cdelor02/mres-thesis/computer_vision/copper_wire_actuator_35fast_chamber_100g_weight_lift-2021-09-06.jpg_502.jpg

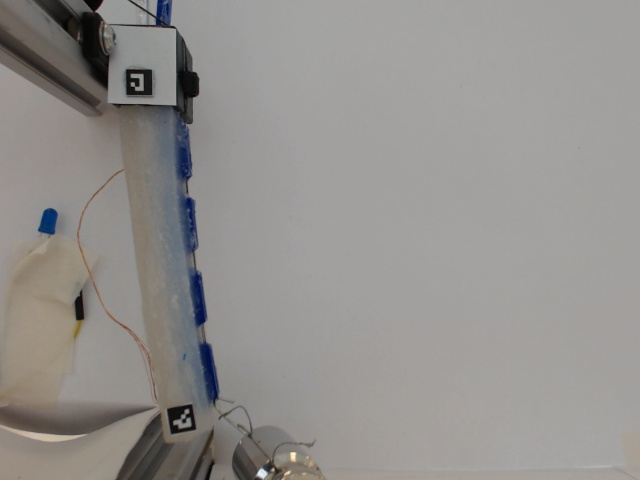
computer_vision/copper_wire_actuator_35fast_chamber_100g_weight_lift-2021-09-06.jpg_502.jpg
