cdelor02/mres-thesis/computer_vision/figure_images.png_1524.jpg

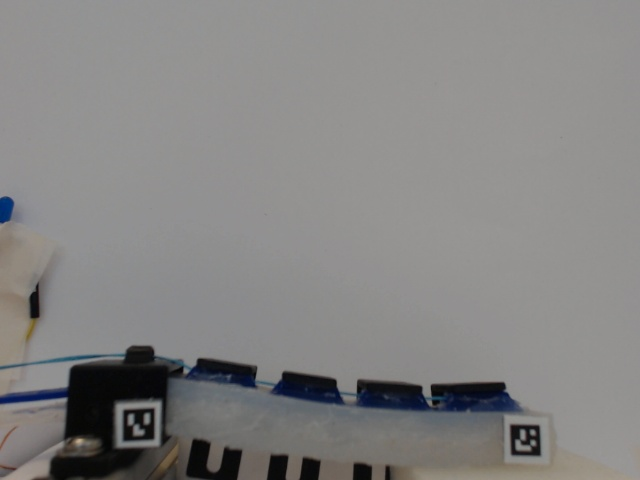
computer_vision/figure_images.png_1524.jpg
