cdelor02/mres-thesis/computer_vision/firstframe.jpg

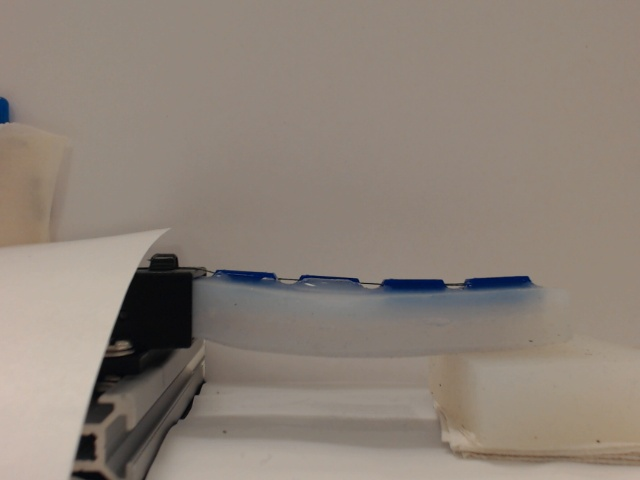
computer_vision/firstframe.jpg
