cdelor02/mres-thesis/computer_vision/firstframe_edited.jpg

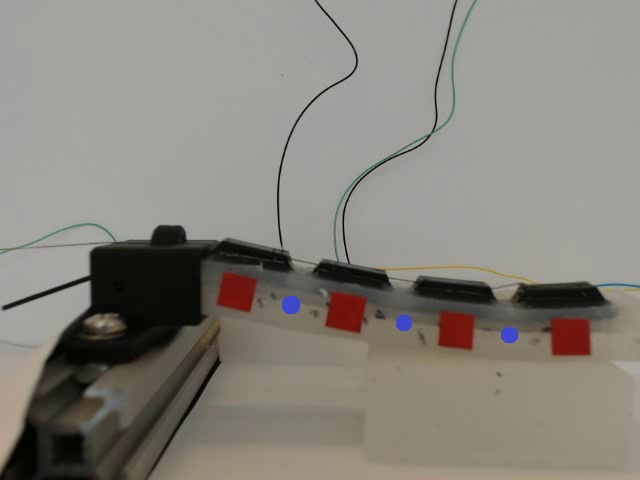
computer_vision/firstframe_edited.jpg
