cdelor02/mres-thesis/computer_vision/hihihi2021-09-06.jpg_659.jpg

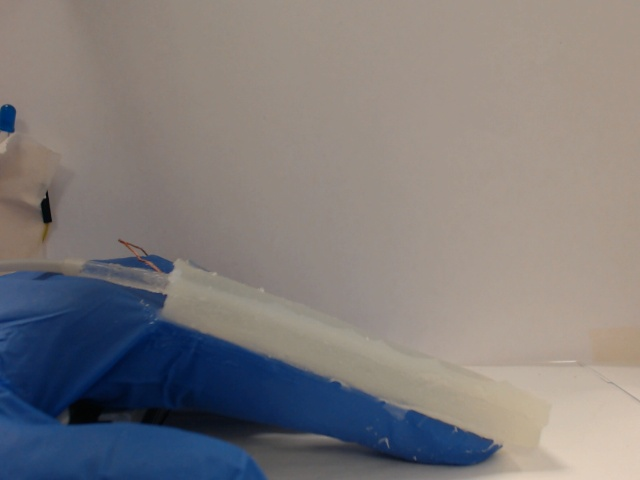
computer_vision/hihihi2021-09-06.jpg_659.jpg
