cdelor02/mres-thesis/computer_vision/imcap_187.jpg

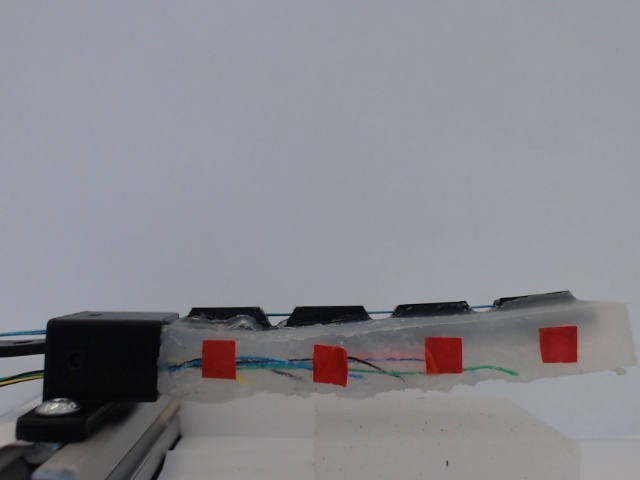
computer_vision/imcap_187.jpg
