cdelor02/mres-thesis/computer_vision/opencv_images/firstframe.jpg

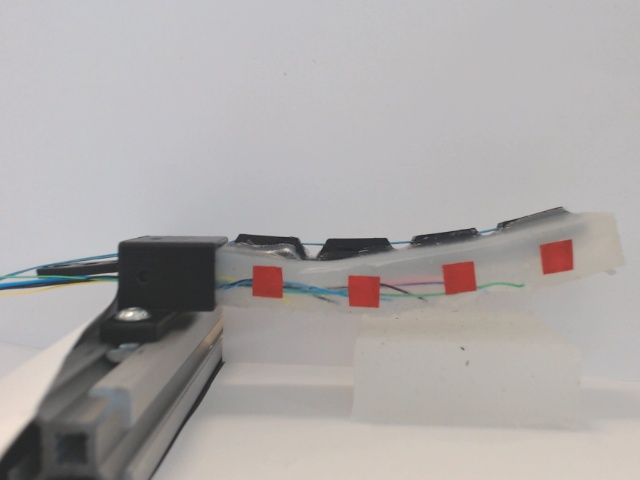
computer_vision/opencv_images/firstframe.jpg
