cdelor02/mres-thesis/computer_vision/opencv_images/myframe_348.jpg

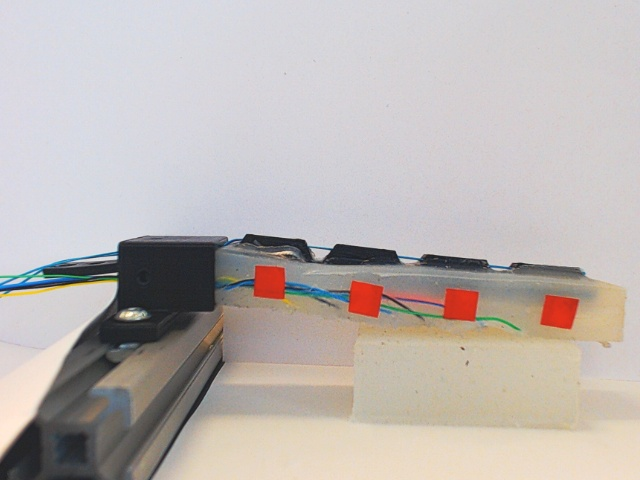
computer_vision/opencv_images/myframe_348.jpg
