cdelor02/mres-thesis/computer_vision/opencv_images/myframe_360.jpg

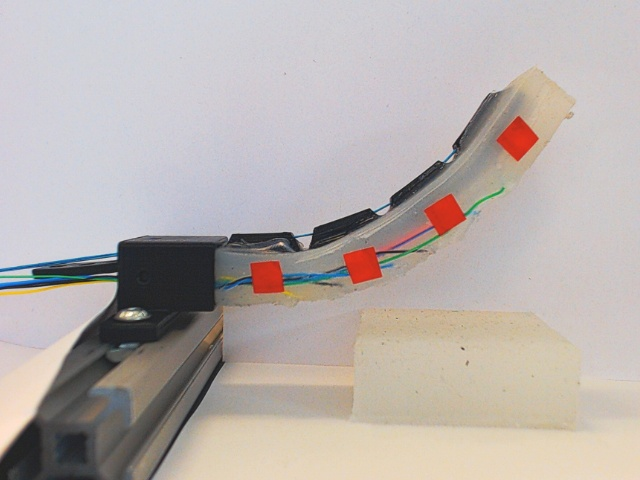
computer_vision/opencv_images/myframe_360.jpg
