cdelor02/mres-thesis/computer_vision/opencv_images/myframe_1371.jpg

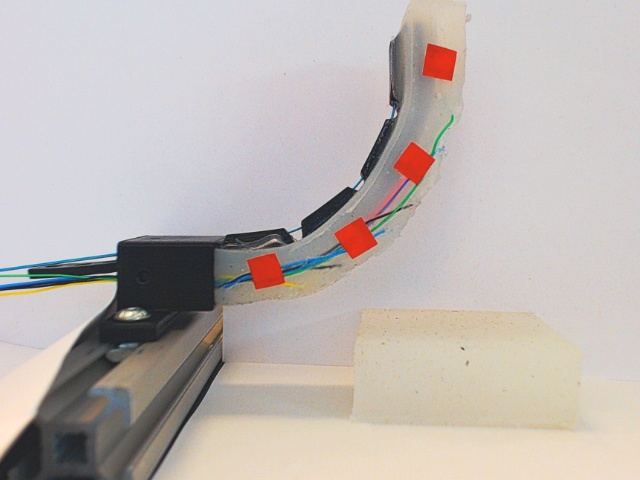
computer_vision/opencv_images/myframe_1371.jpg
