cdelor02/mres-thesis/computer_vision/opencv_images/myframe_1525.jpg

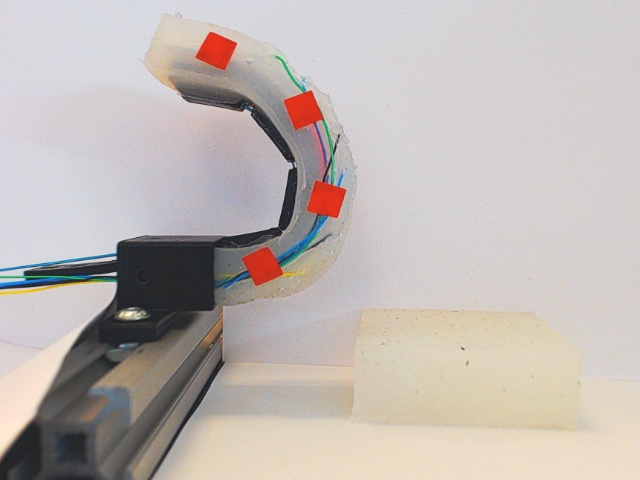
computer_vision/opencv_images/myframe_1525.jpg
