cdelor02/mres-thesis/computer_vision/opencv_images/tracked_points_paths.png

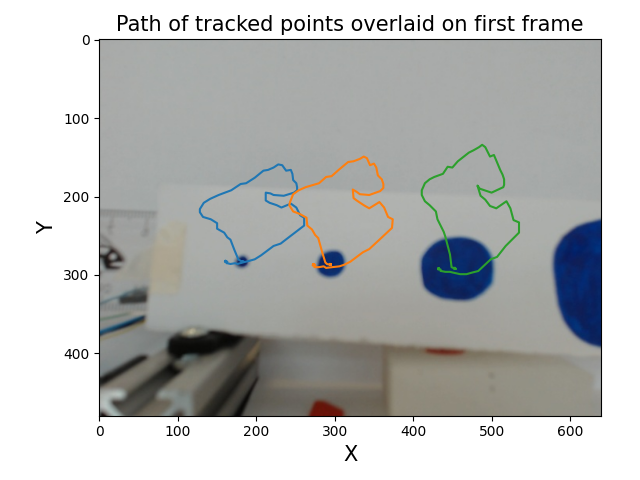
computer_vision/opencv_images/tracked_points_paths.png
