cdelor02/mres-thesis/computer_vision/opencv_images/tracked_points_simple_arcs.png

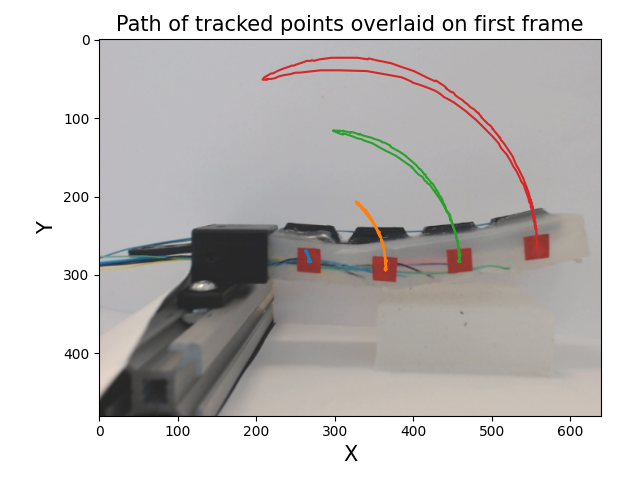
computer_vision/opencv_images/tracked_points_simple_arcs.png
