cdelor02/mres-thesis/computer_vision/red.png

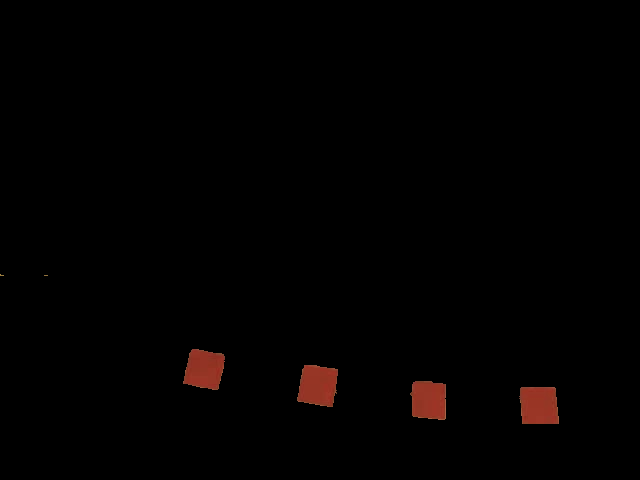
computer_vision/red.png
