cdelor02/mres-thesis/FPC_design/whole_system_block_diagram_v1.png

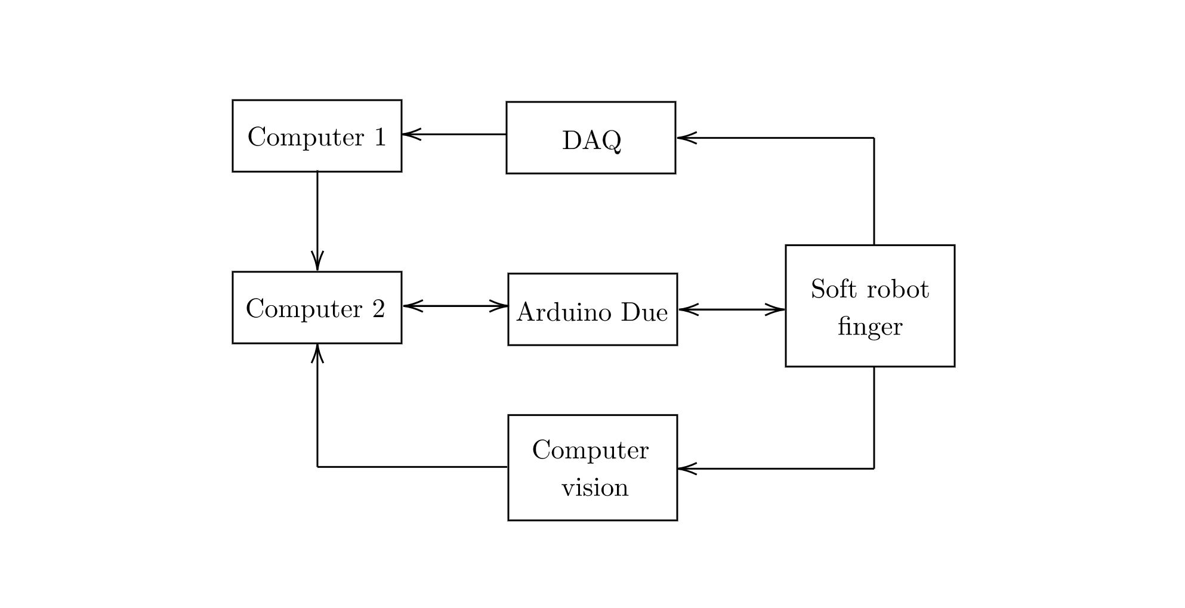
FPC_design/whole_system_block_diagram_v1.png
