cdelor02/mres-thesis/images/1_in_two_stages_duetimer_bettertest_data.png

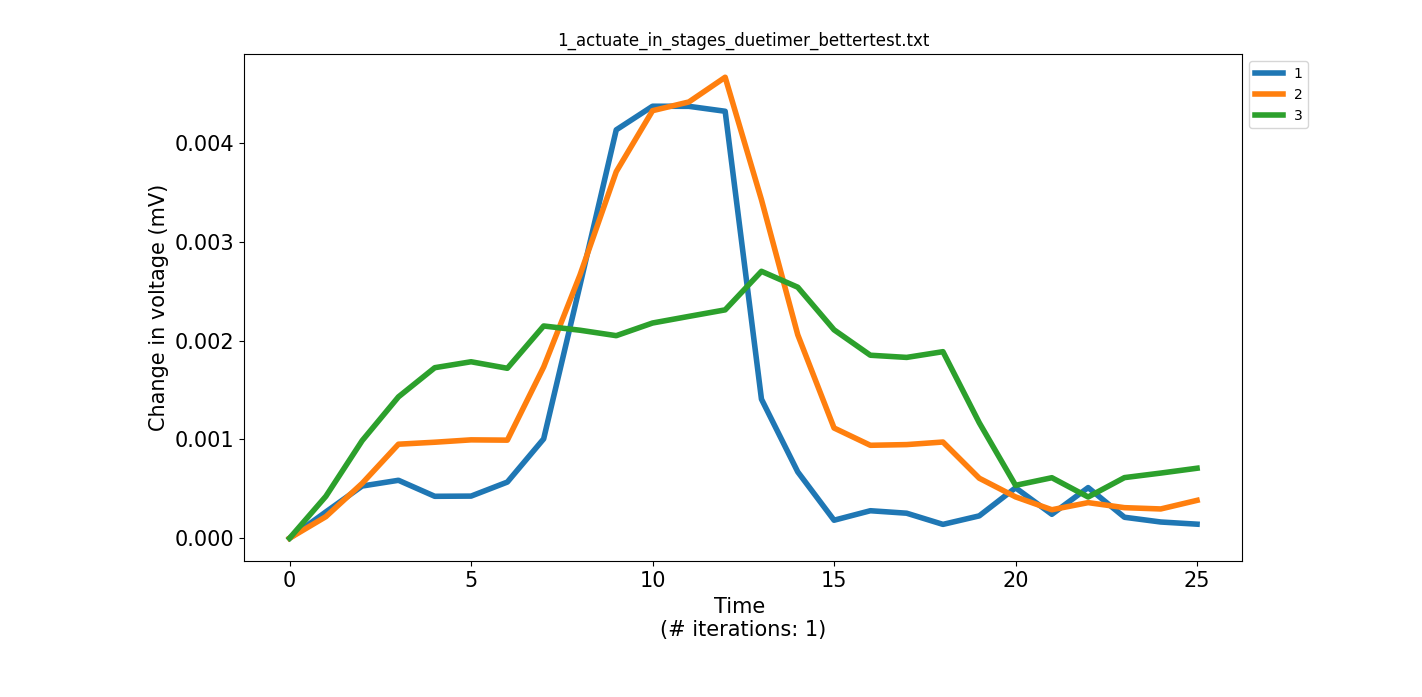
images/1_in_two_stages_duetimer_bettertest_data.png
