cdelor02/mres-thesis/images/5__duetimer_bettertest_data.png

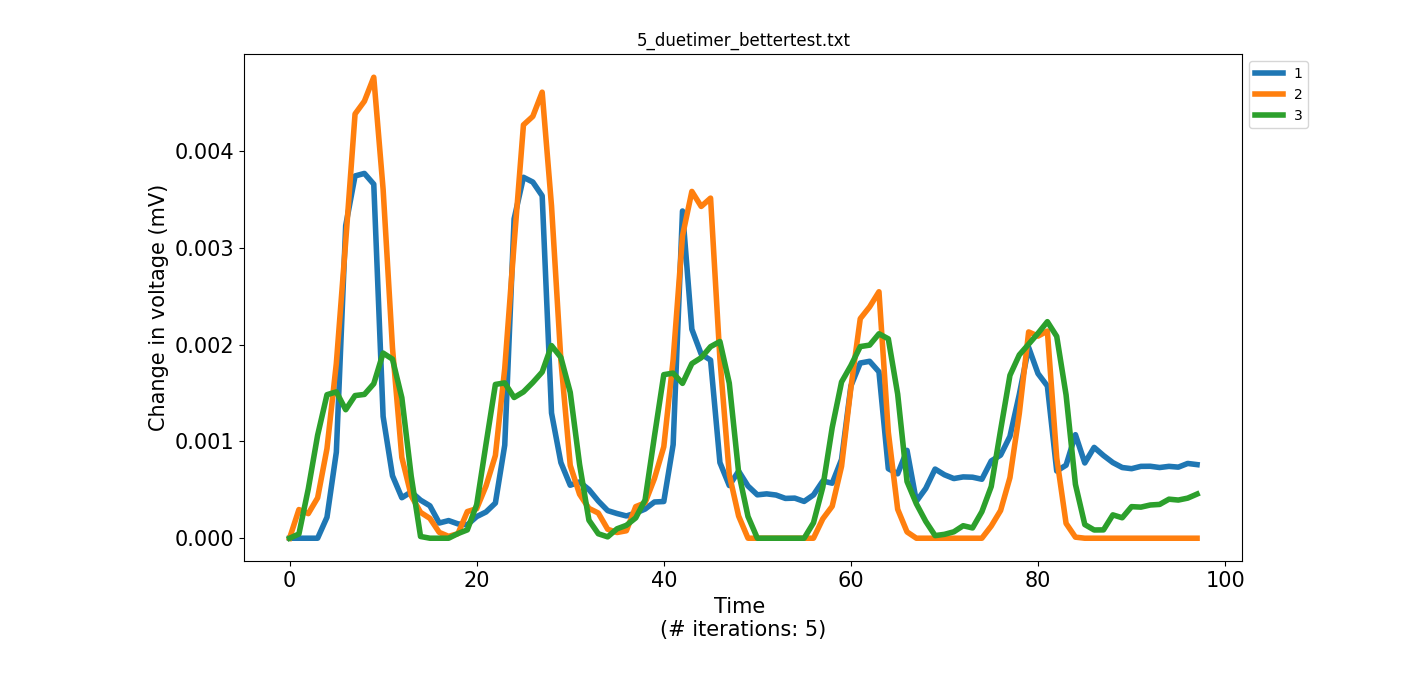
images/5__duetimer_bettertest_data.png
