cdelor02/mres-thesis/images/5_in_two_stages_duetimer_bettertest_data.png

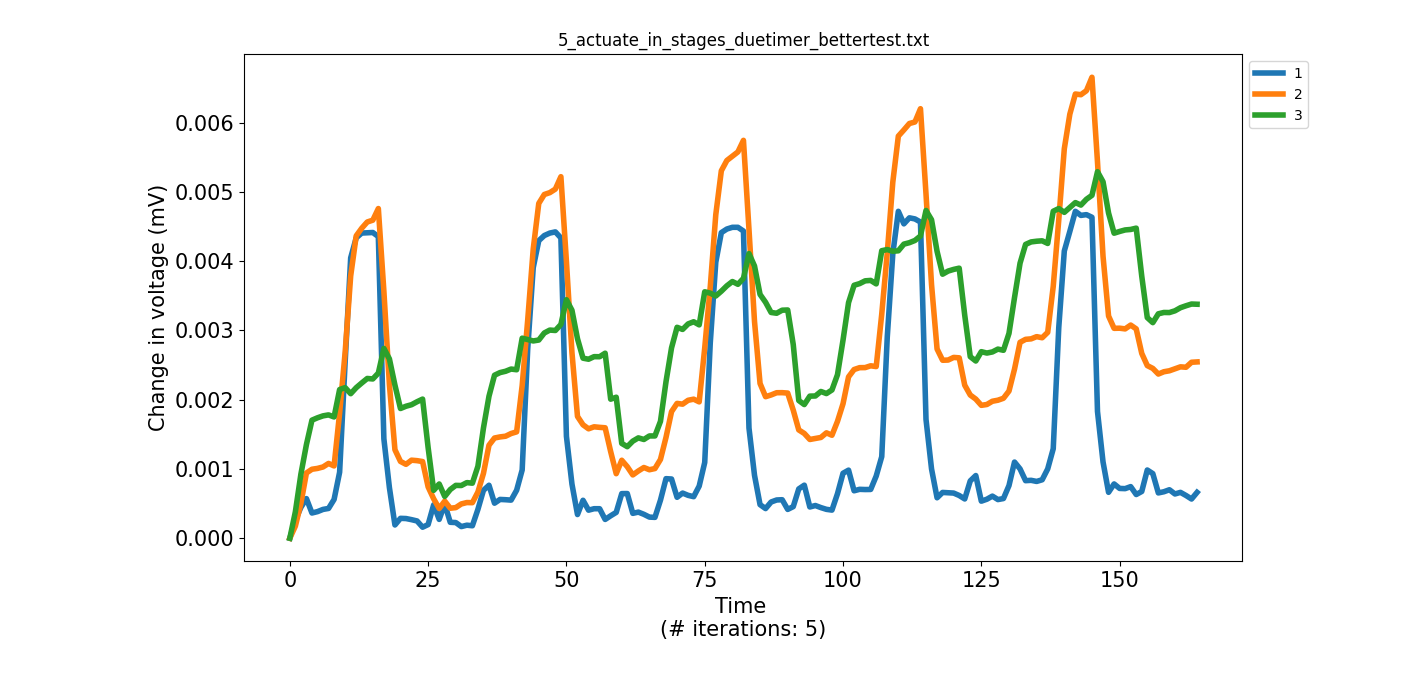
images/5_in_two_stages_duetimer_bettertest_data.png
