cdelor02/mres-thesis/images/10-iteration_episodes_eit_plots/ep2.png

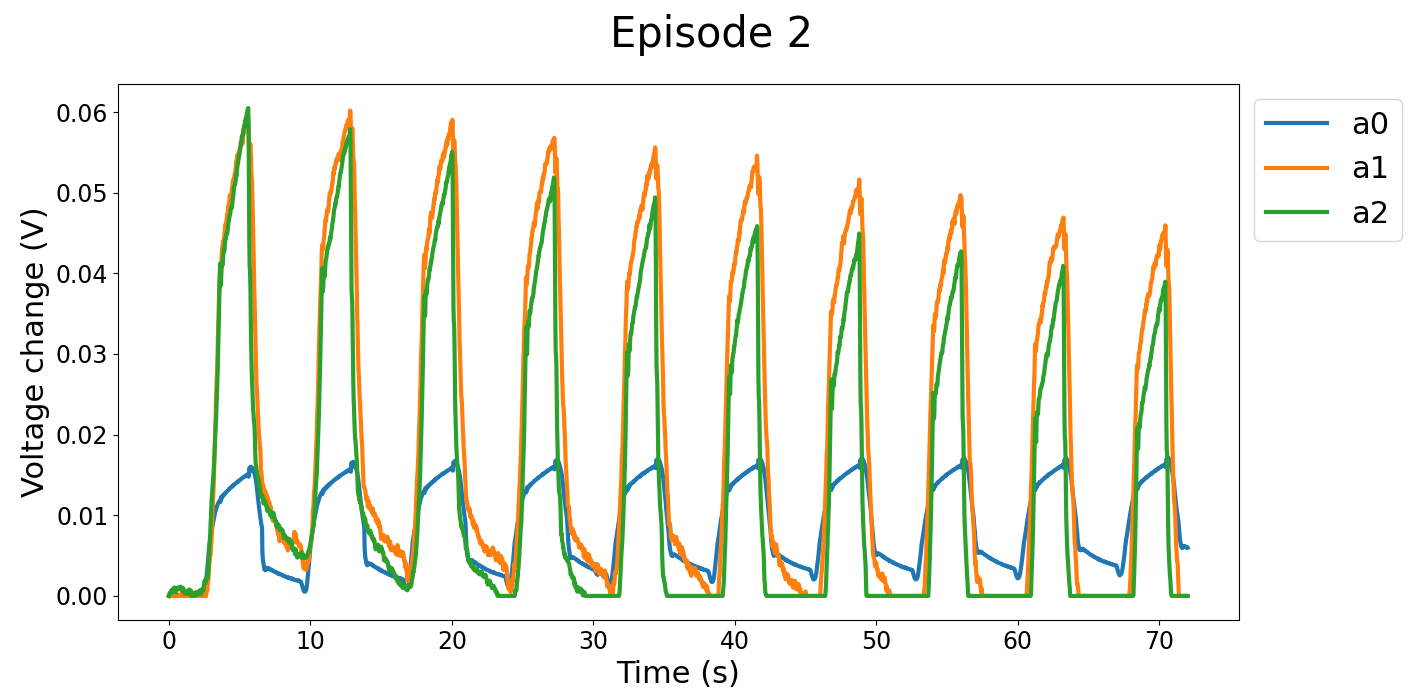
images/10-iteration_episodes_eit_plots/ep2.png
