cdelor02/mres-thesis/images/10-iteration_episodes_eit_plots/ep9.png

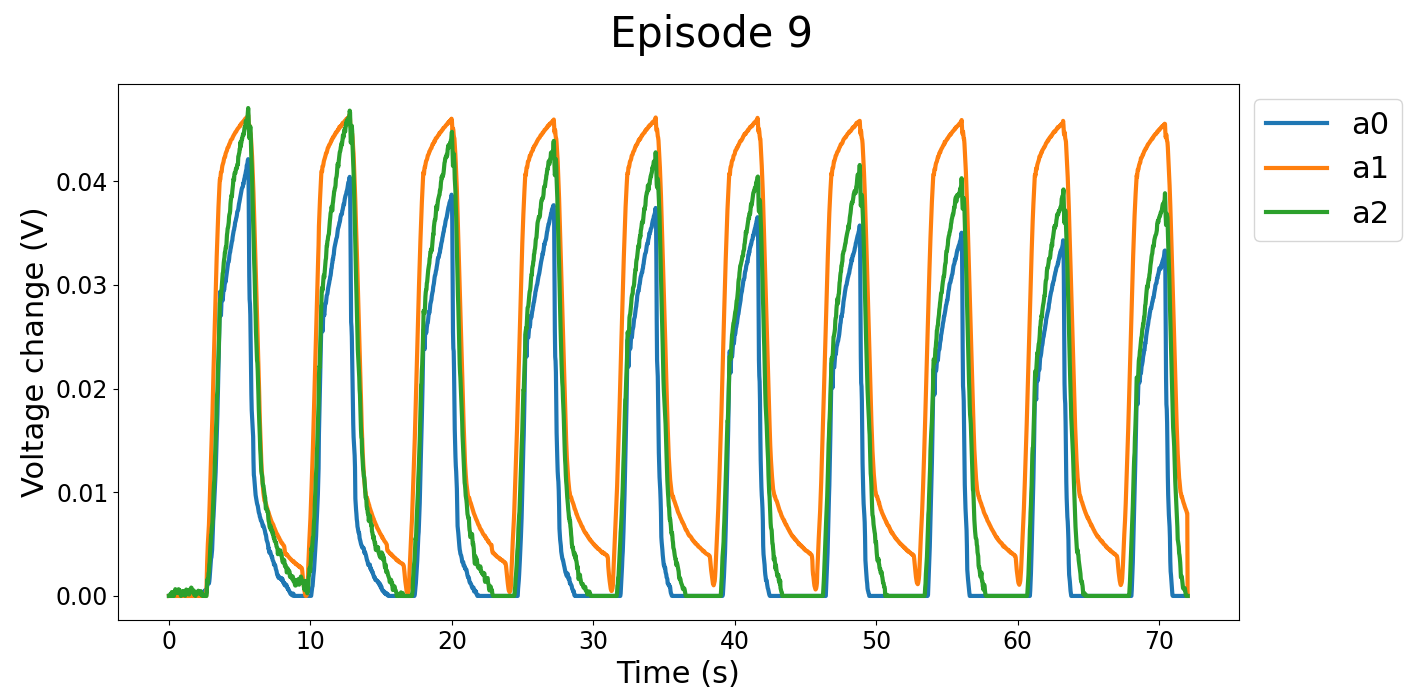
images/10-iteration_episodes_eit_plots/ep9.png
