cdelor02/mres-thesis/images/10_duetimer_bettertest_data.png

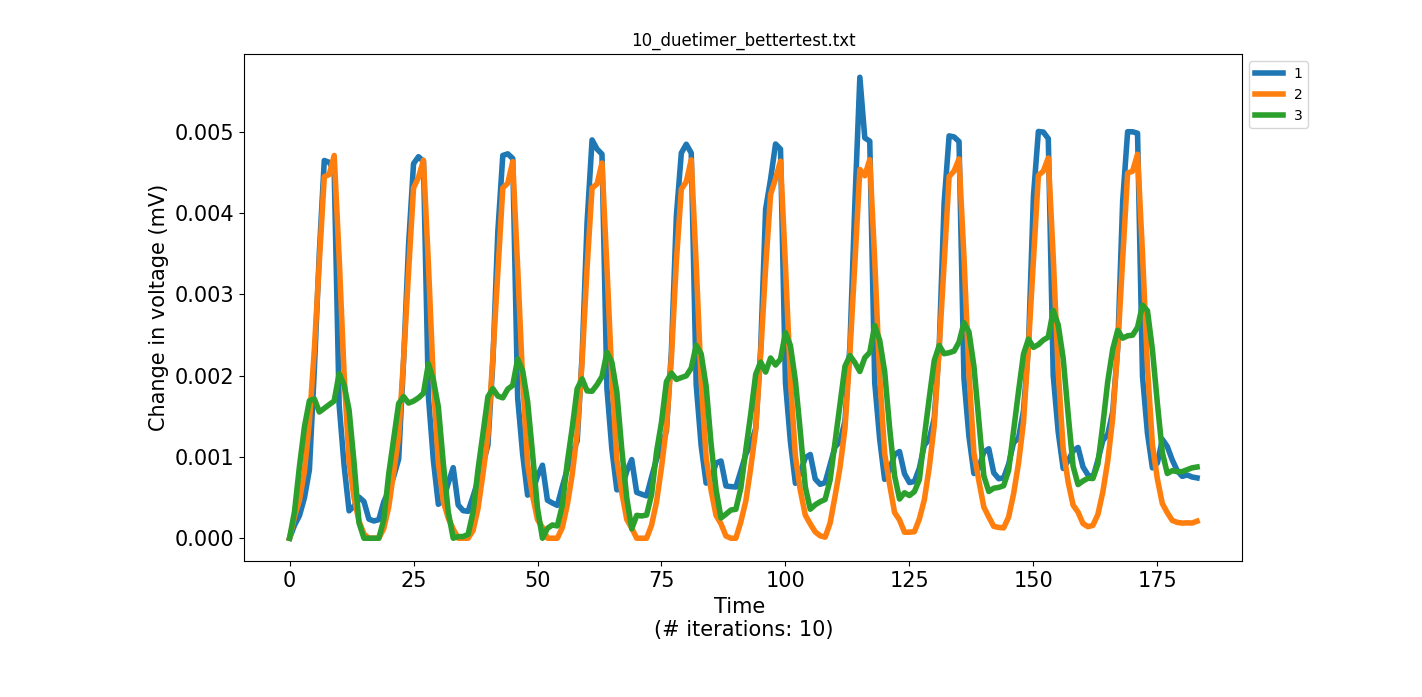
images/10_duetimer_bettertest_data.png
