cdelor02/mres-thesis/images/35fast_chamber_100g_weight_plots/35fast_chamber_100g_lift-flawed_data-had_to_be_adjusted_each_iteration.png

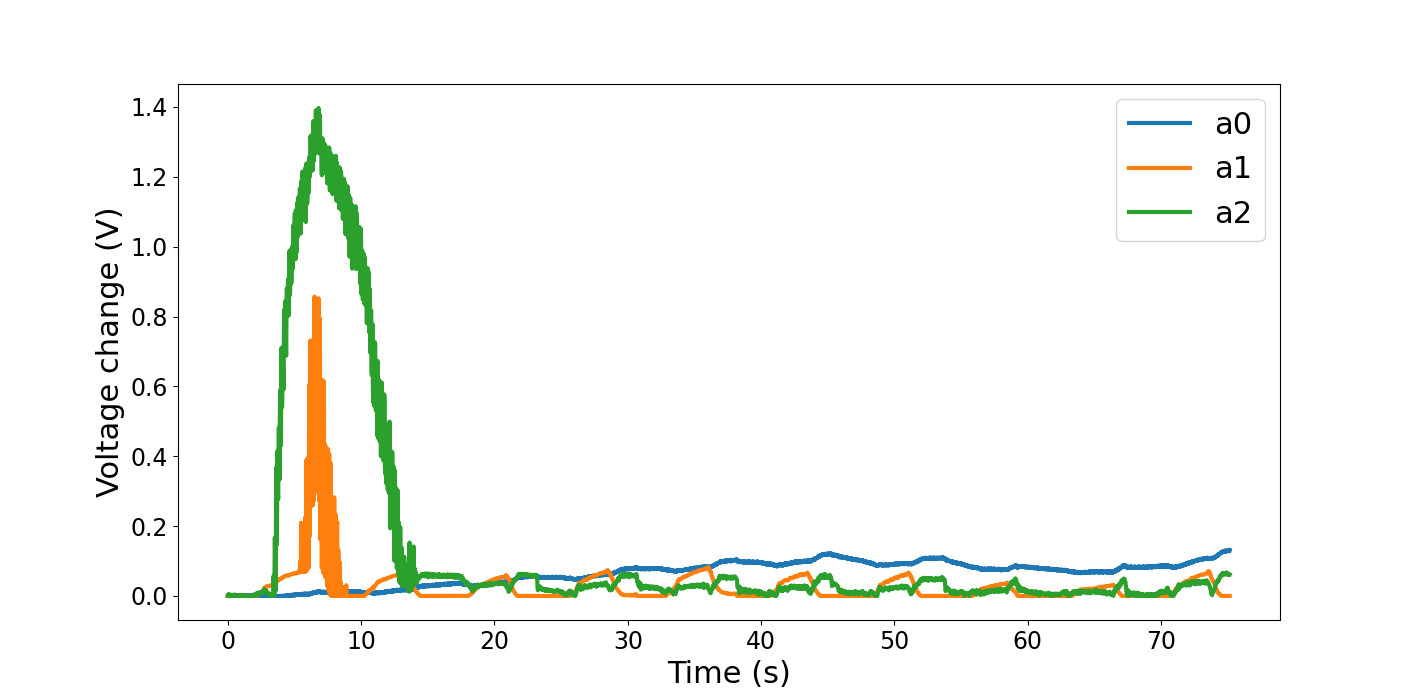
images/35fast_chamber_100g_weight_plots/35fast_chamber_100g_lift-flawed_data-had_to_be_adjusted_each_iteration.png
