cdelor02/mres-thesis/images/35fast_chamber_100g_weight_plots/35fast_chamber_100g_lift-flawed_data_cropped_to_good.png

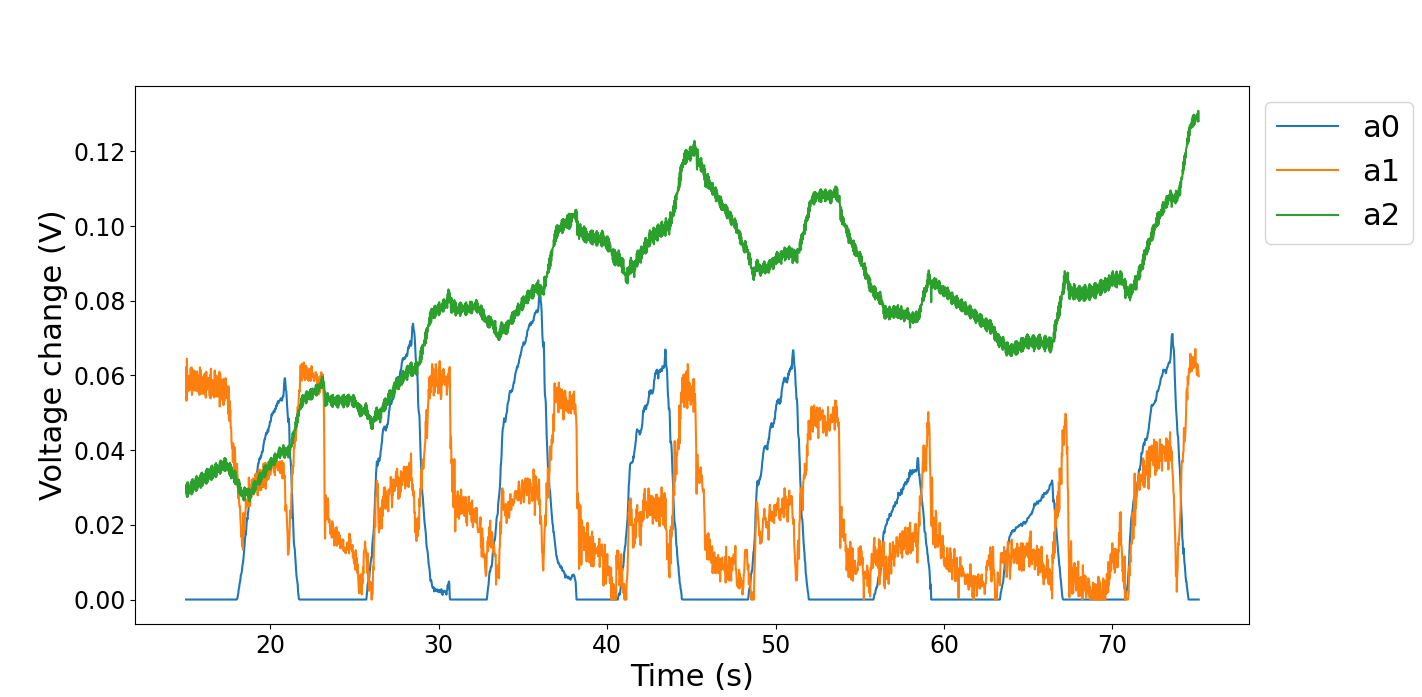
images/35fast_chamber_100g_weight_plots/35fast_chamber_100g_lift-flawed_data_cropped_to_good.png
