cdelor02/mres-thesis/images/35fast_chamber_100g_weight_plots/35fast_chamber_100g_lift.png

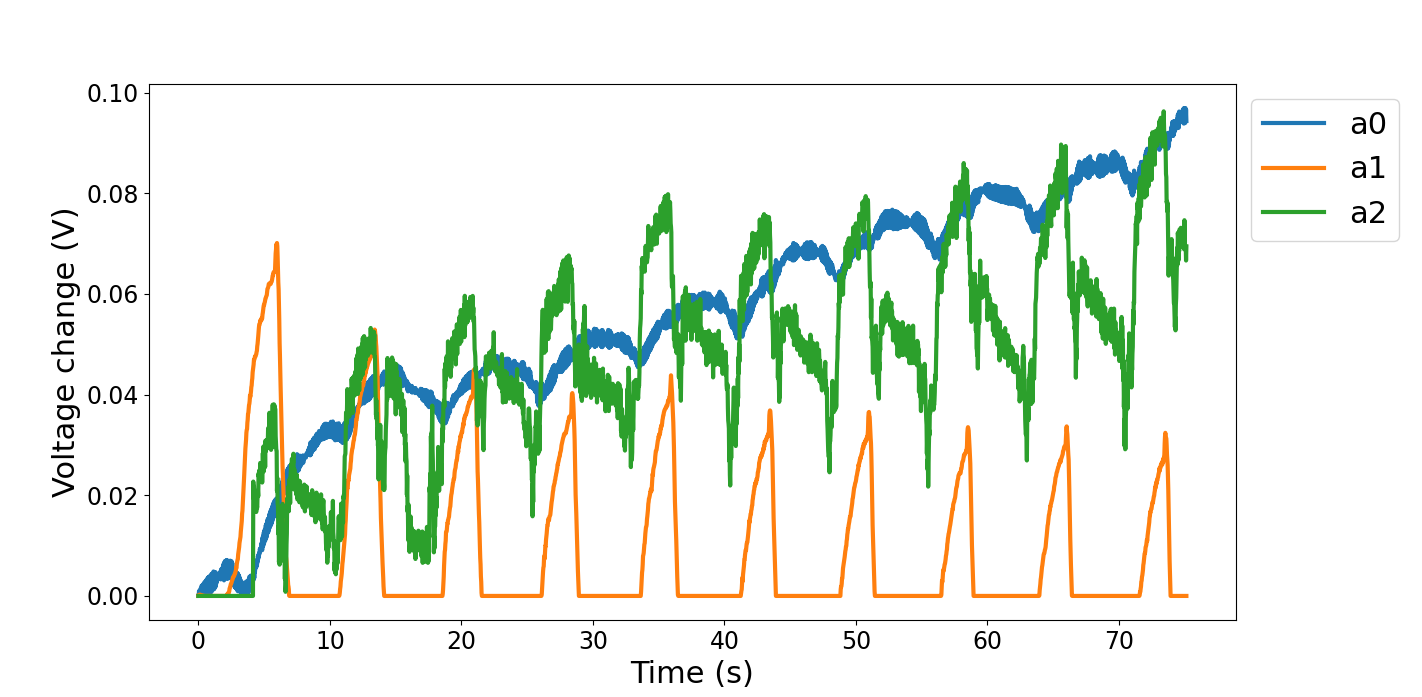
images/35fast_chamber_100g_weight_plots/35fast_chamber_100g_lift.png
