cdelor02/mres-thesis/images/35fast_chamber_100g_weight_plots/35fast_chamber_vertical_no_weight.png

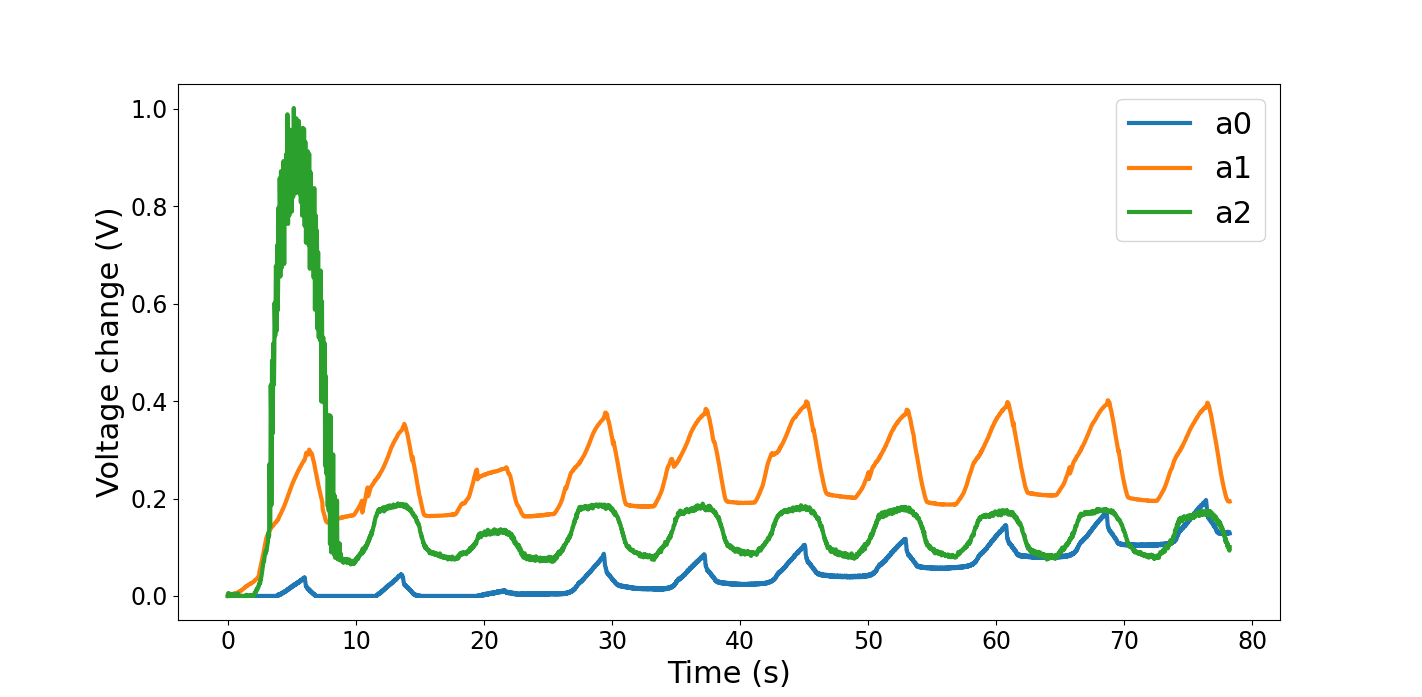
images/35fast_chamber_100g_weight_plots/35fast_chamber_vertical_no_weight.png
