cdelor02/mres-thesis/images/35fast_chamber_100g_weight_plots/weight_vs_noweight_EIT_signals.png

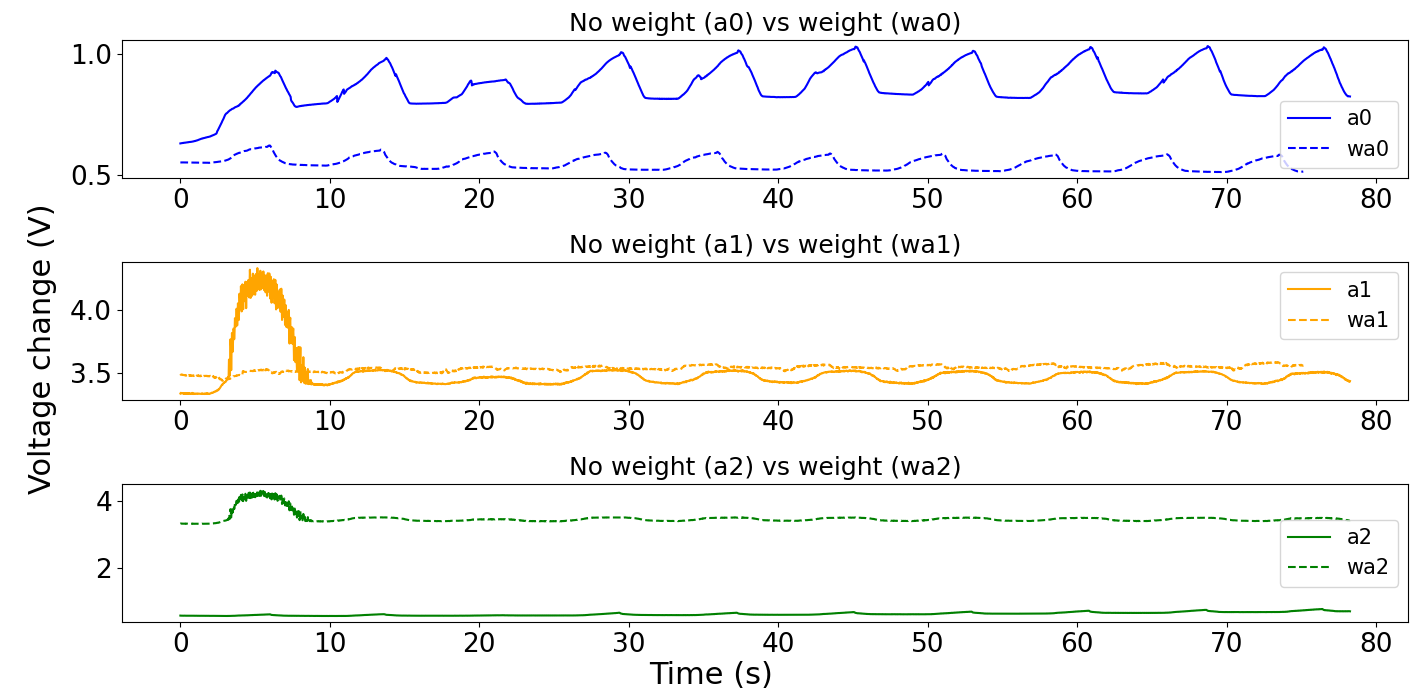
images/35fast_chamber_100g_weight_plots/weight_vs_noweight_EIT_signals.png
