cdelor02/mres-thesis/images/actuator_cross-section_electrode_pins.png

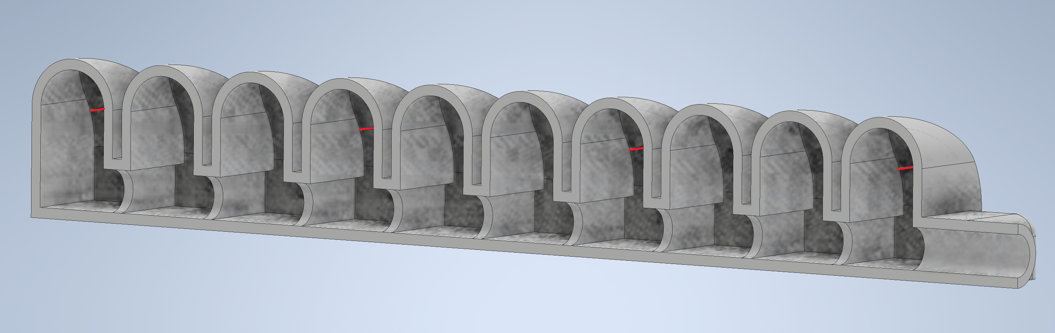
images/actuator_cross-section_electrode_pins.png
