cdelor02/mres-thesis/images/actuator_parallel_EIT_chamber_iso.jpg

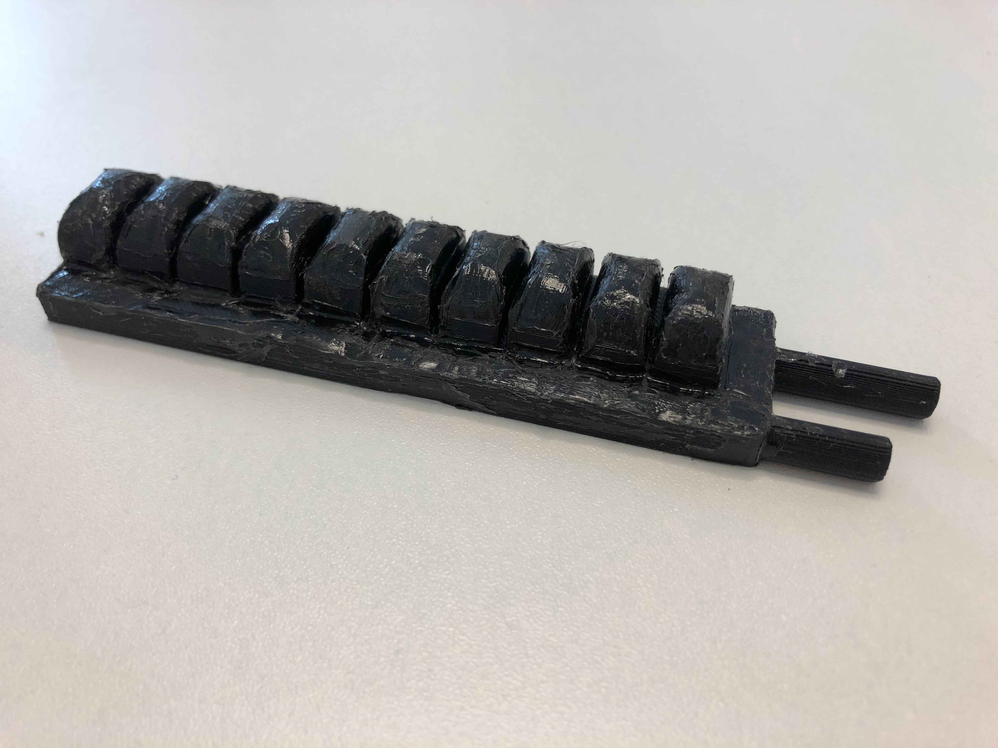
images/actuator_parallel_EIT_chamber_iso.jpg
