cdelor02/mres-thesis/images/actuator_parallel_EIT_chamber_mounted_wired.jpg

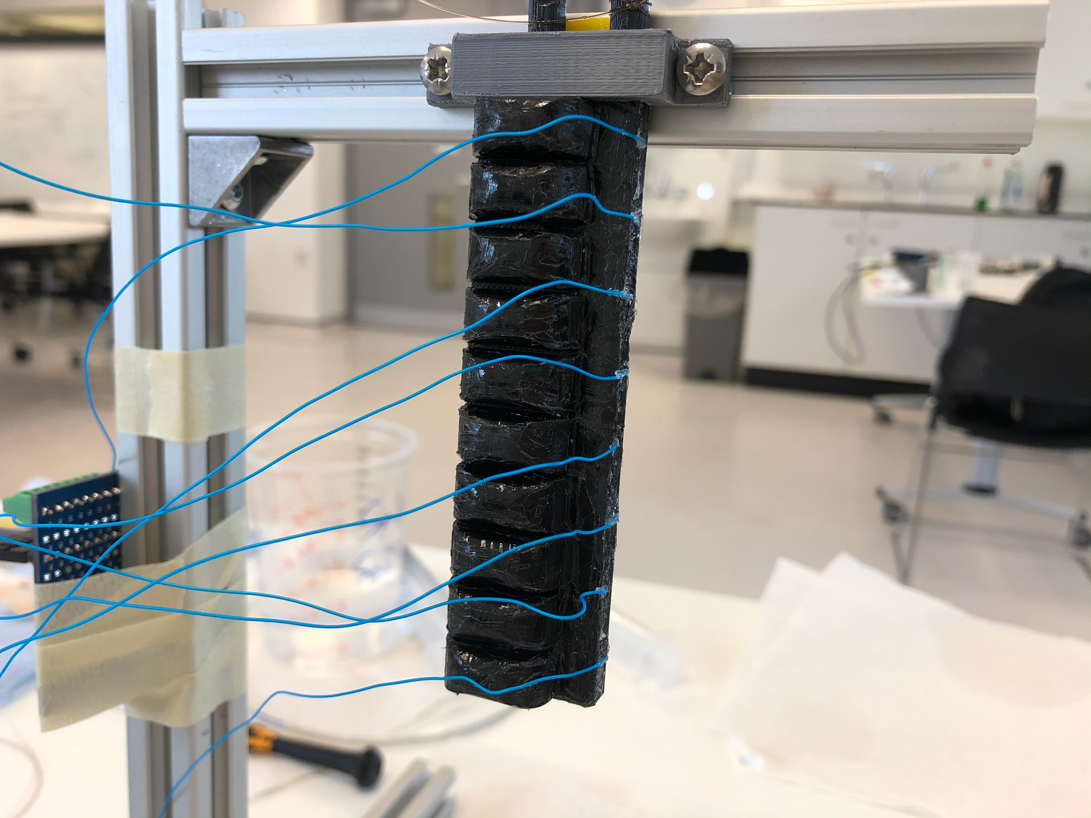
images/actuator_parallel_EIT_chamber_mounted_wired.jpg
