cdelor02/mres-thesis/images/actuator_tube_w_electrodes.jpg

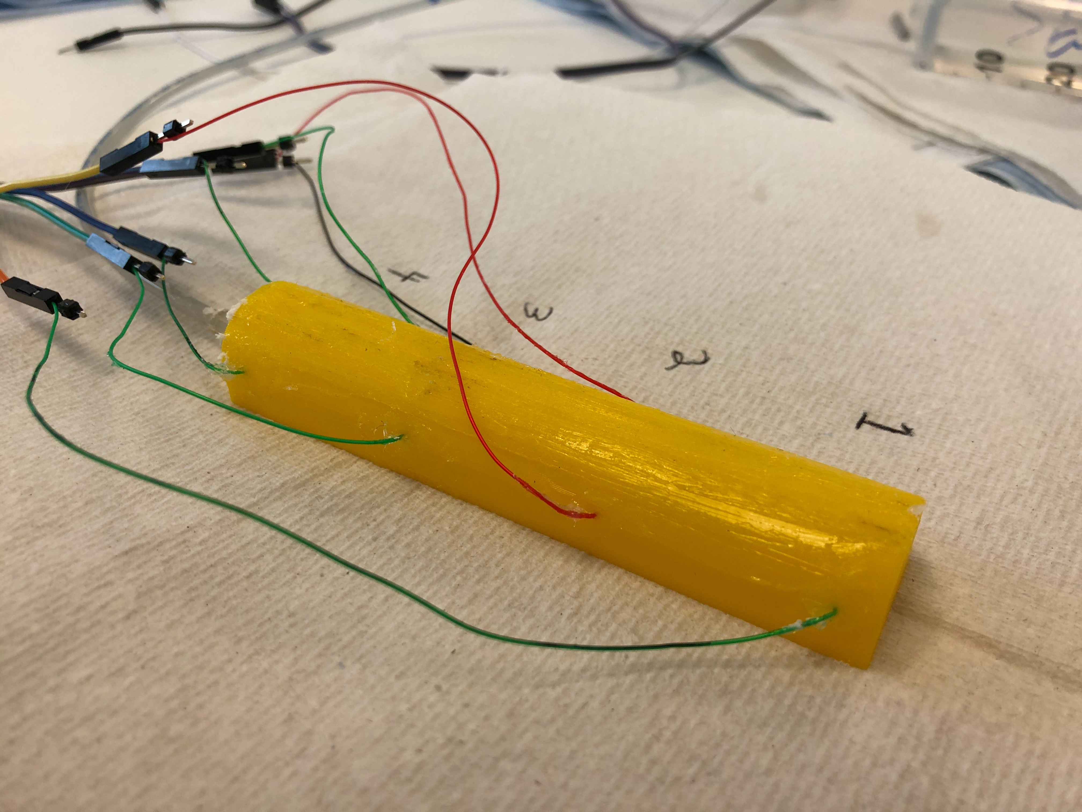
images/actuator_tube_w_electrodes.jpg
