cdelor02/mres-thesis/images/anterior_electrodes_actuator.jpg

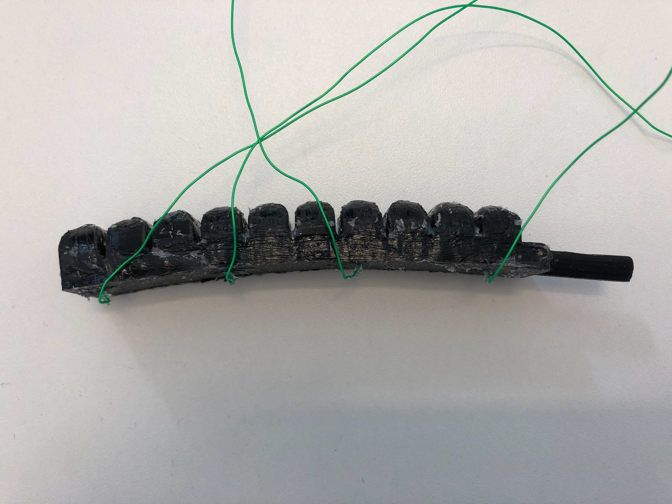
images/anterior_electrodes_actuator.jpg
