cdelor02/mres-thesis/images/bending_angle_vs_voltage_standard_deviations-2021-09-05.png

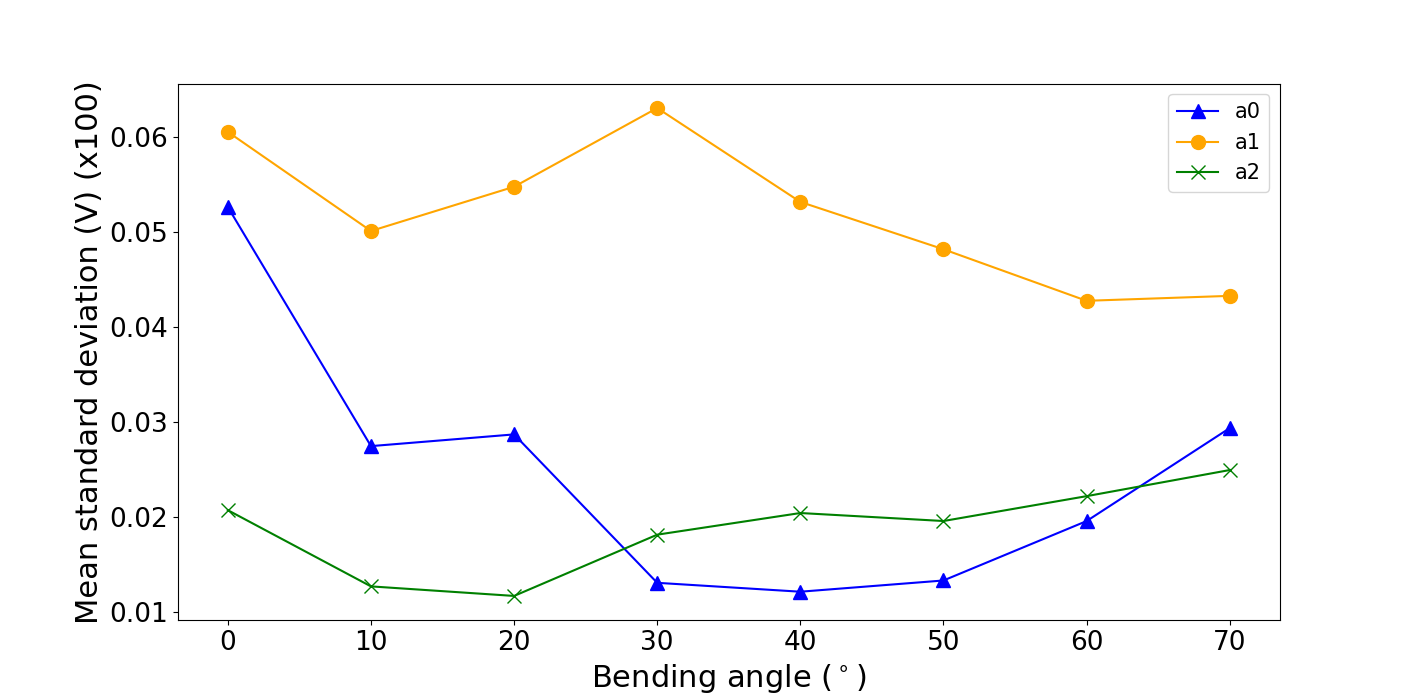
images/bending_angle_vs_voltage_standard_deviations-2021-09-05.png
