cdelor02/mres-thesis/images/bending_angle_vs_voltages-2021-09-03.png

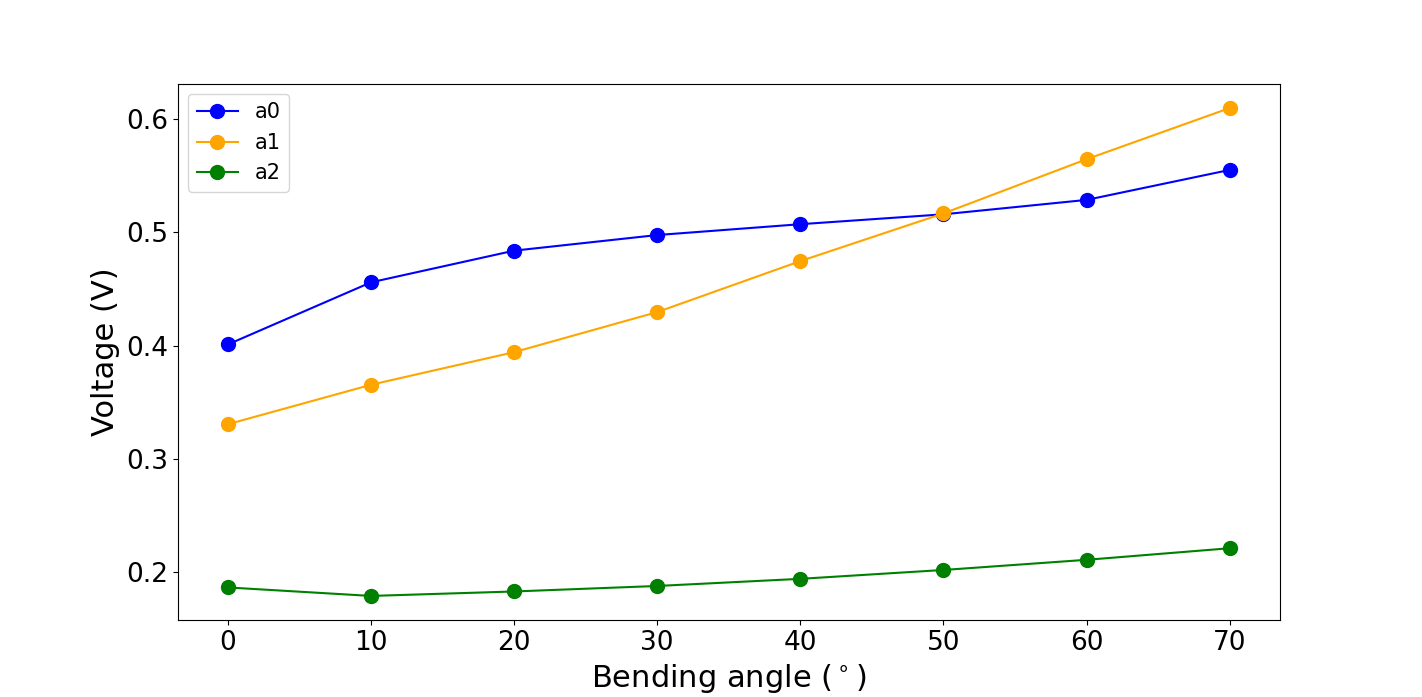
images/bending_angle_vs_voltages-2021-09-03.png
