cdelor02/mres-thesis/images/bone_piece_side_view.png

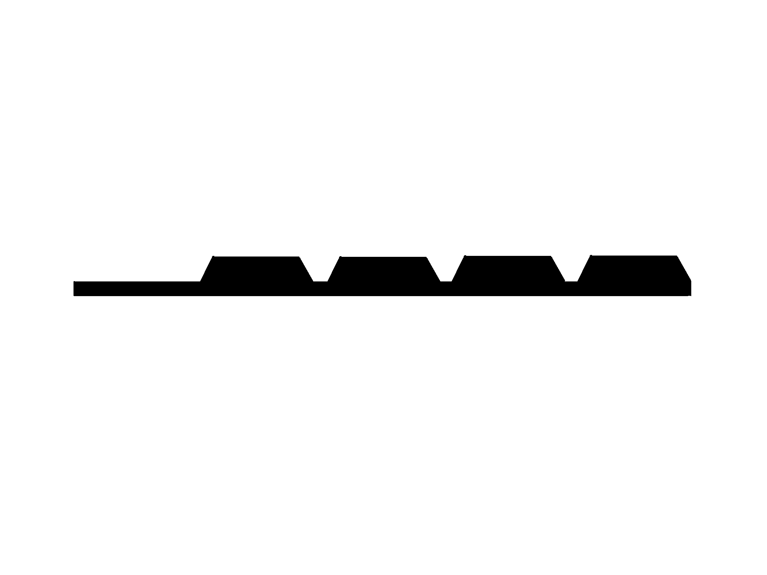
images/bone_piece_side_view.png
