cdelor02/mres-thesis/images/continuous.png

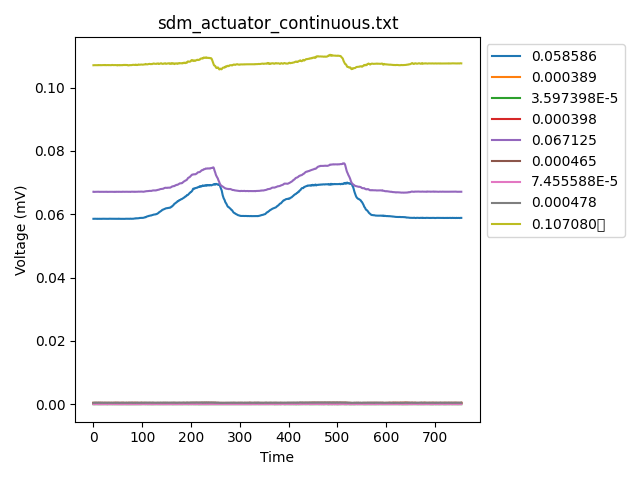
images/continuous.png
