cdelor02/mres-thesis/images/continuous_best_plot.png

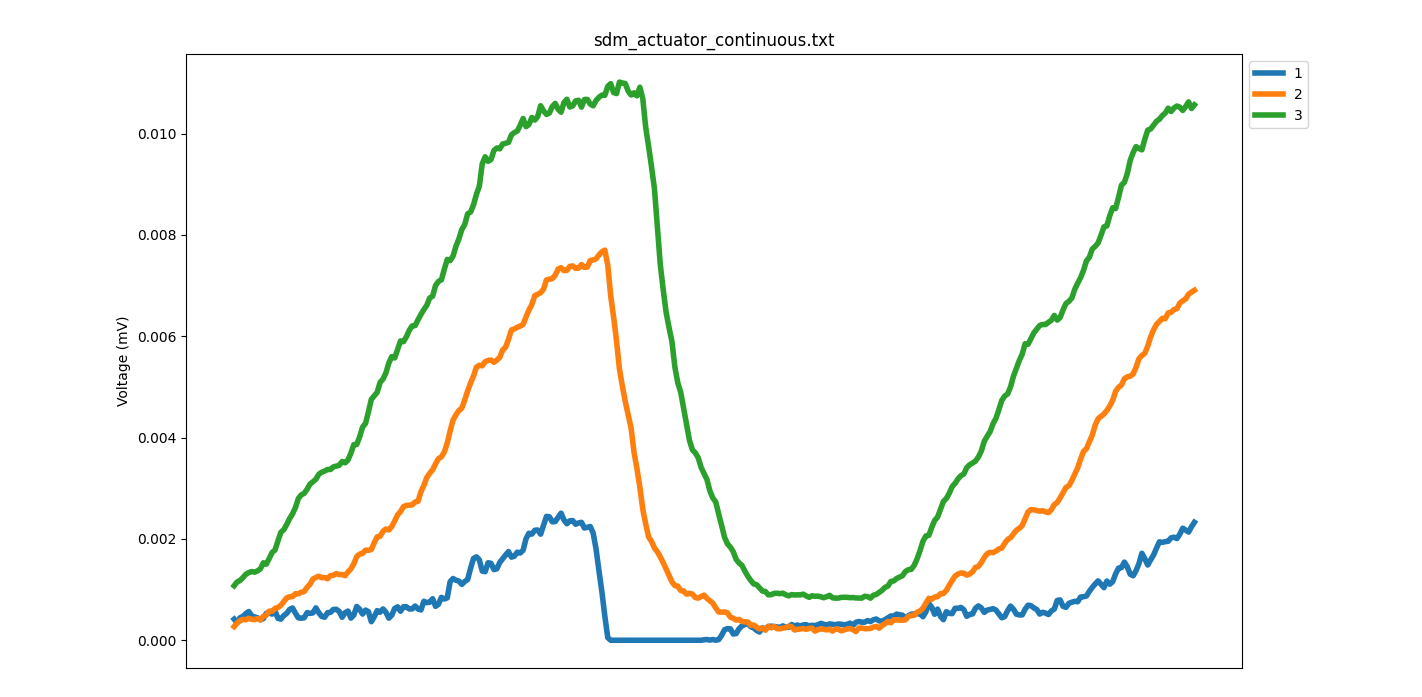
images/continuous_best_plot.png
