cdelor02/mres-thesis/images/continuous_no_x_labels.png

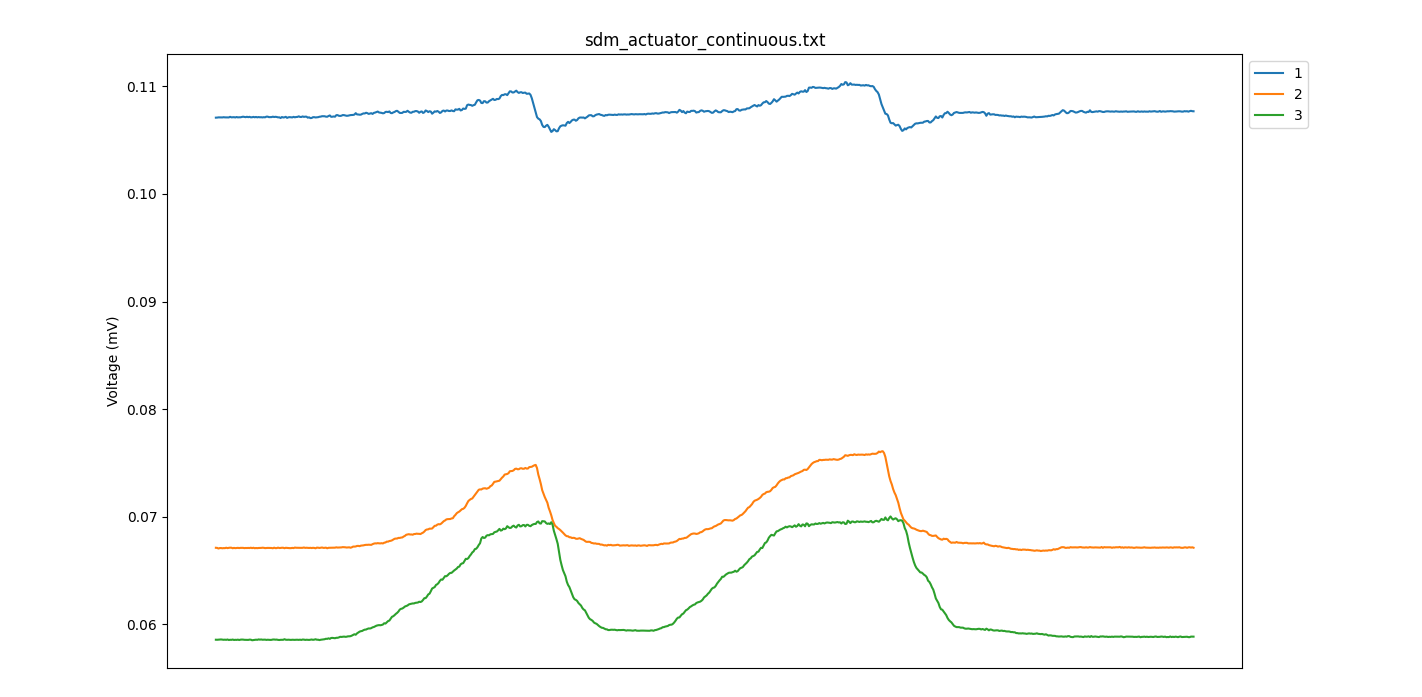
images/continuous_no_x_labels.png
