cdelor02/mres-thesis/images/copper_actuator_500_samples_40Hz--EIT_vs_stepper_data.png

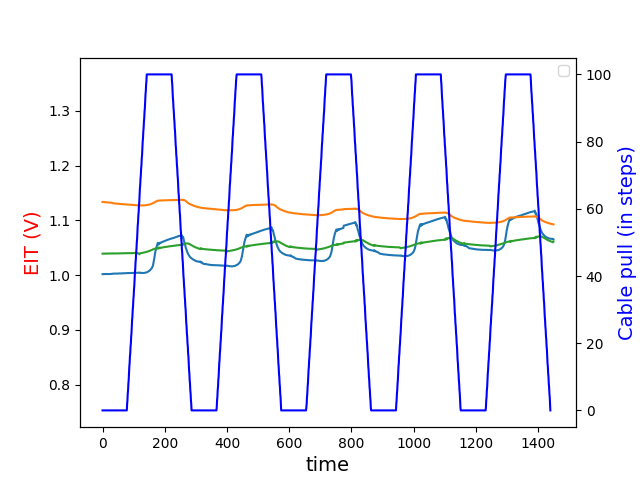
images/copper_actuator_500_samples_40Hz--EIT_vs_stepper_data.png
