cdelor02/mres-thesis/images/current_field_stim_1.png

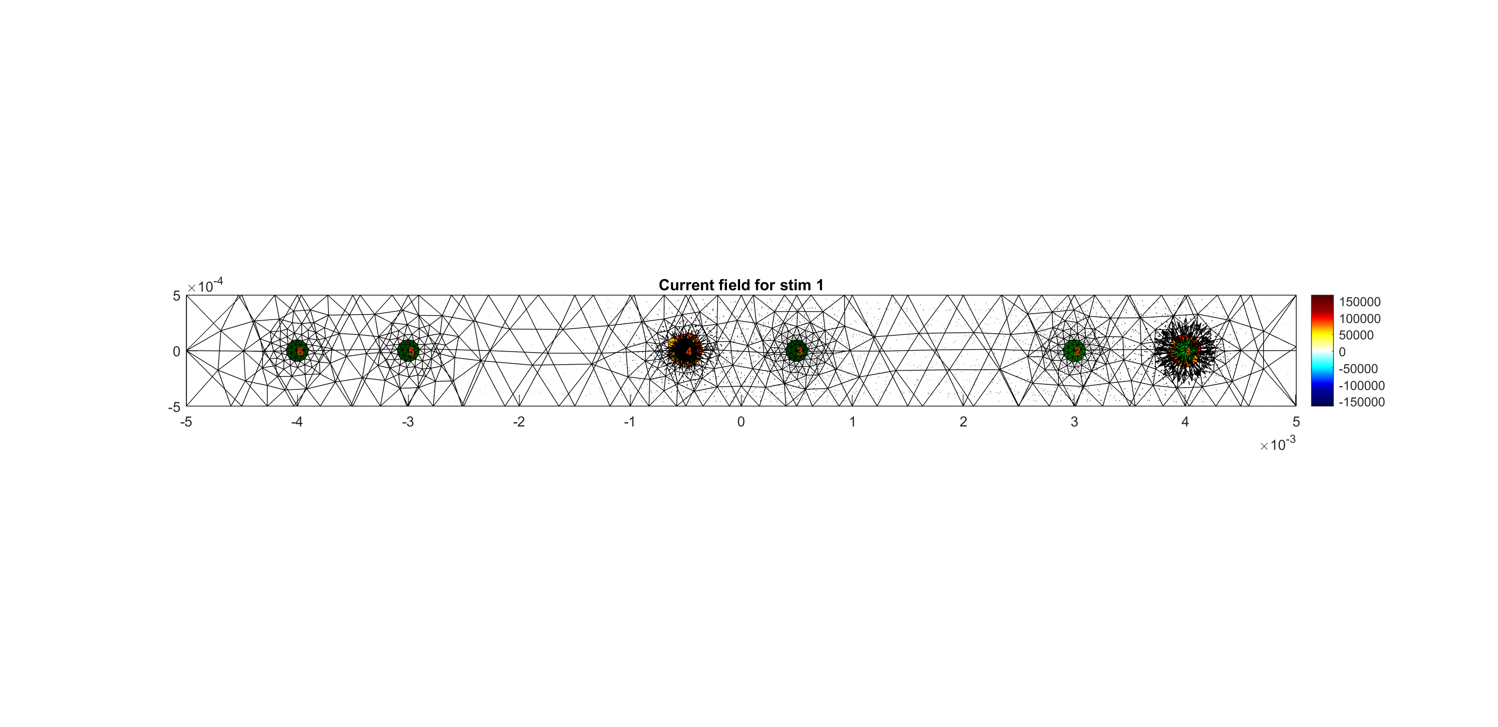
images/current_field_stim_1.png
