cdelor02/mres-thesis/images/eit_chamber_glove_plots/eit_chamber_glove_ep2.png

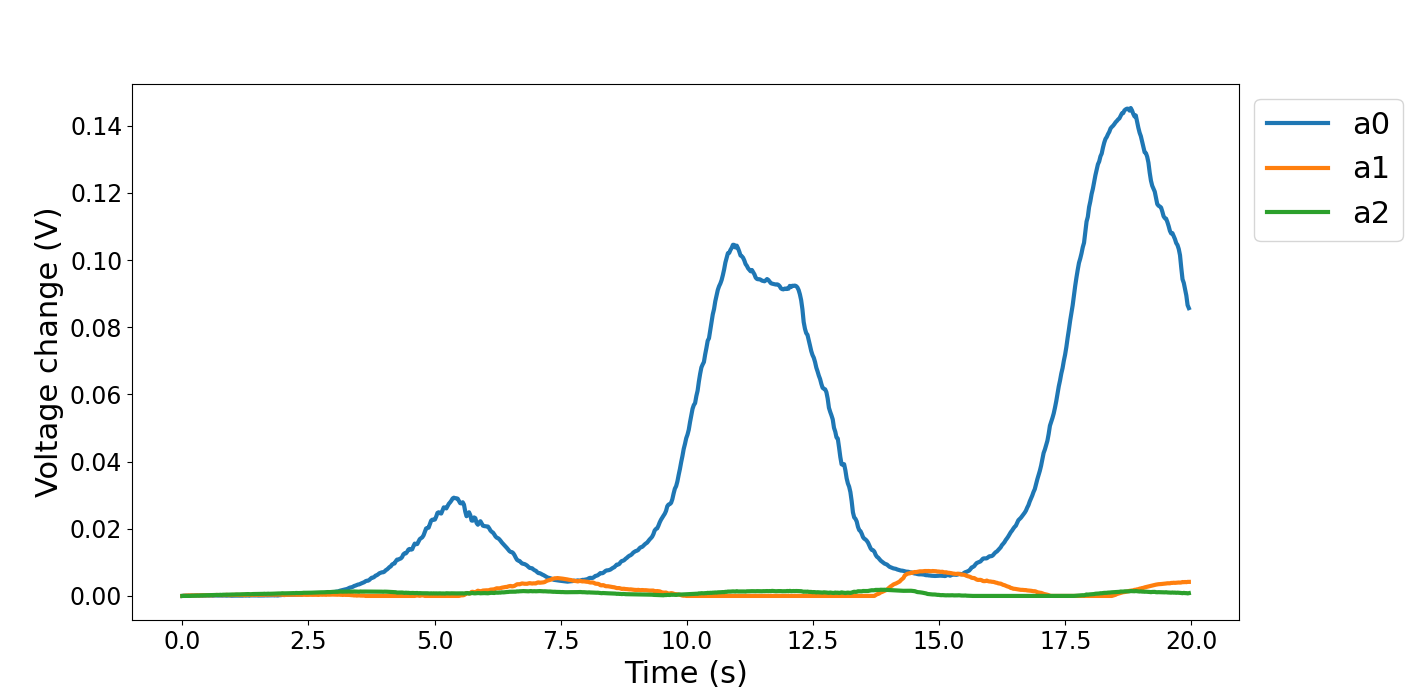
images/eit_chamber_glove_plots/eit_chamber_glove_ep2.png
