cdelor02/mres-thesis/images/eit_chamber_two_electrode_pairs.jpg

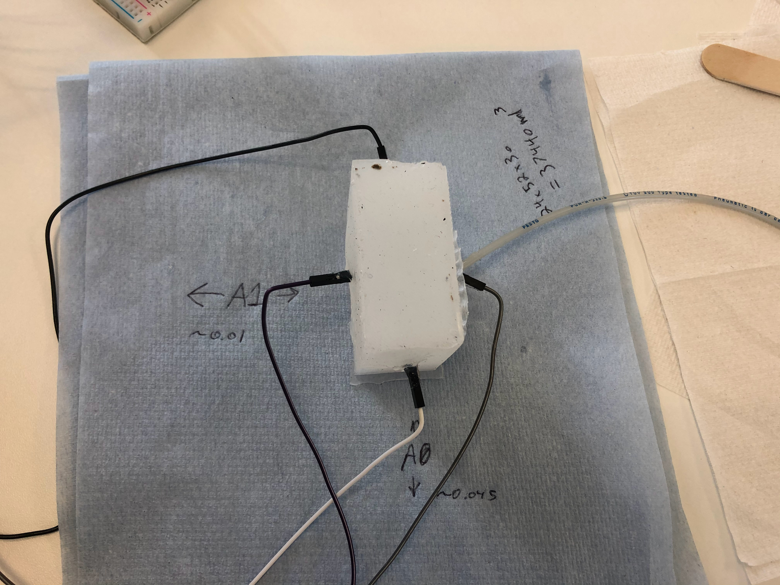
images/eit_chamber_two_electrode_pairs.jpg
