cdelor02/mres-thesis/images/electrode_locations_hollow_straight_finger.png

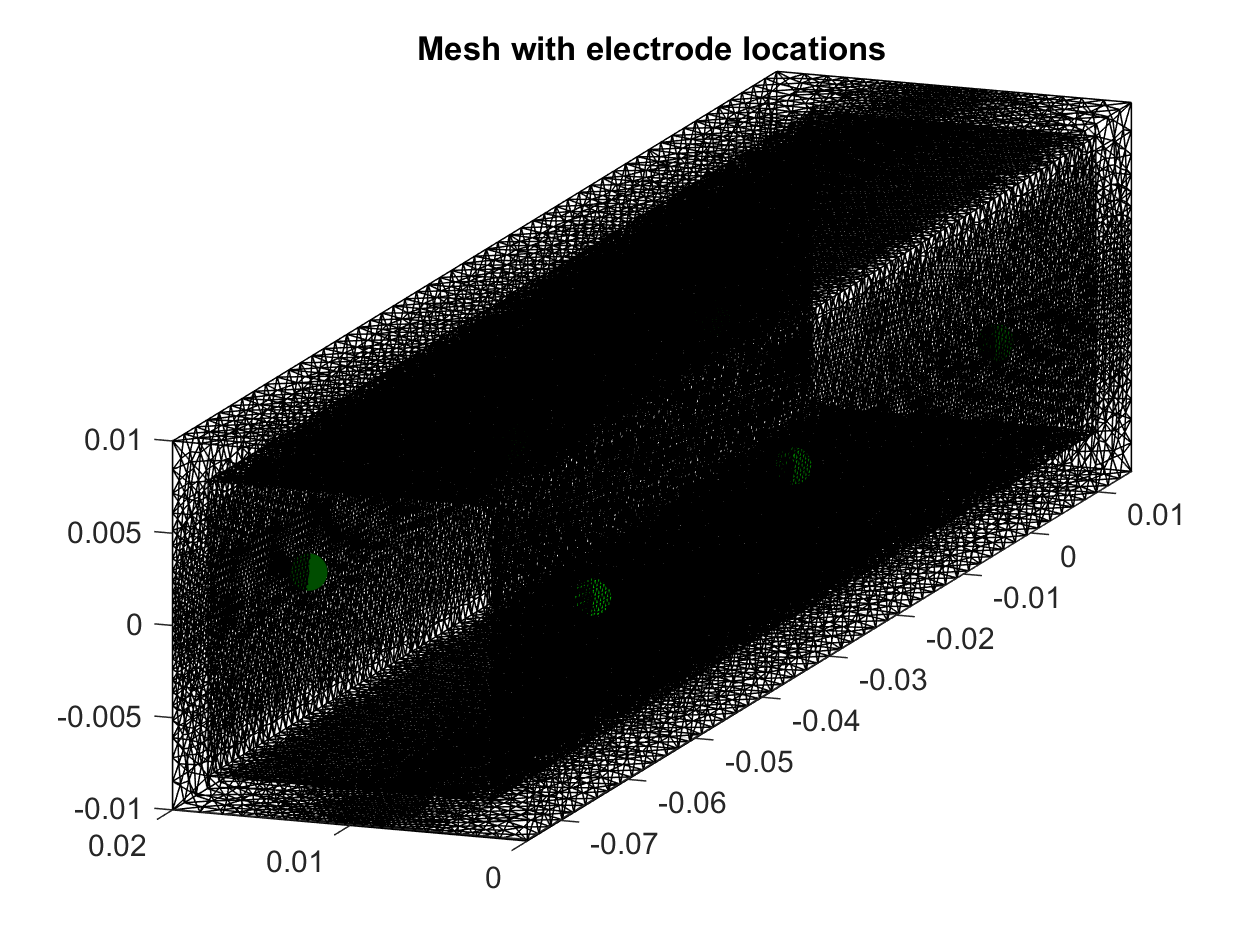
images/electrode_locations_hollow_straight_finger.png
