cdelor02/mres-thesis/images/ep11_all_channels_values_plotted.png

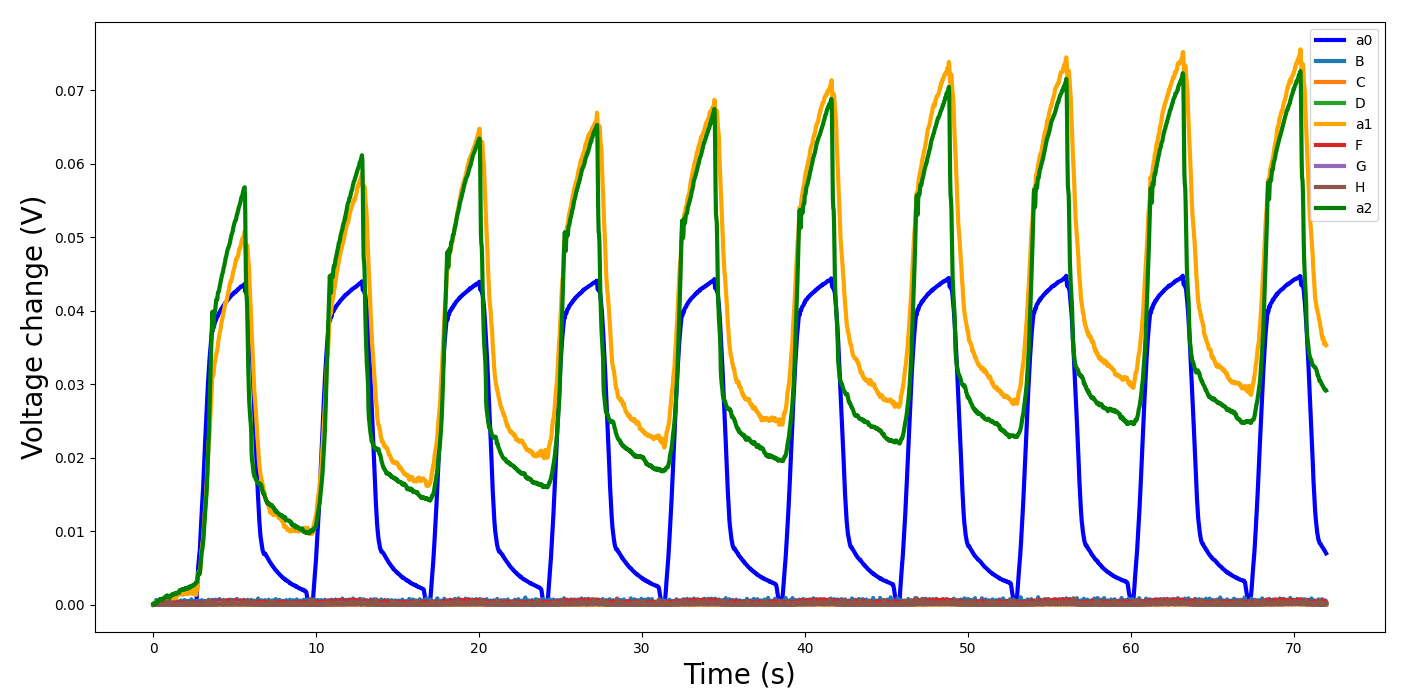
images/ep11_all_channels_values_plotted.png
