cdelor02/mres-thesis/images/final_eit_chamber_eidors_iso_view.png

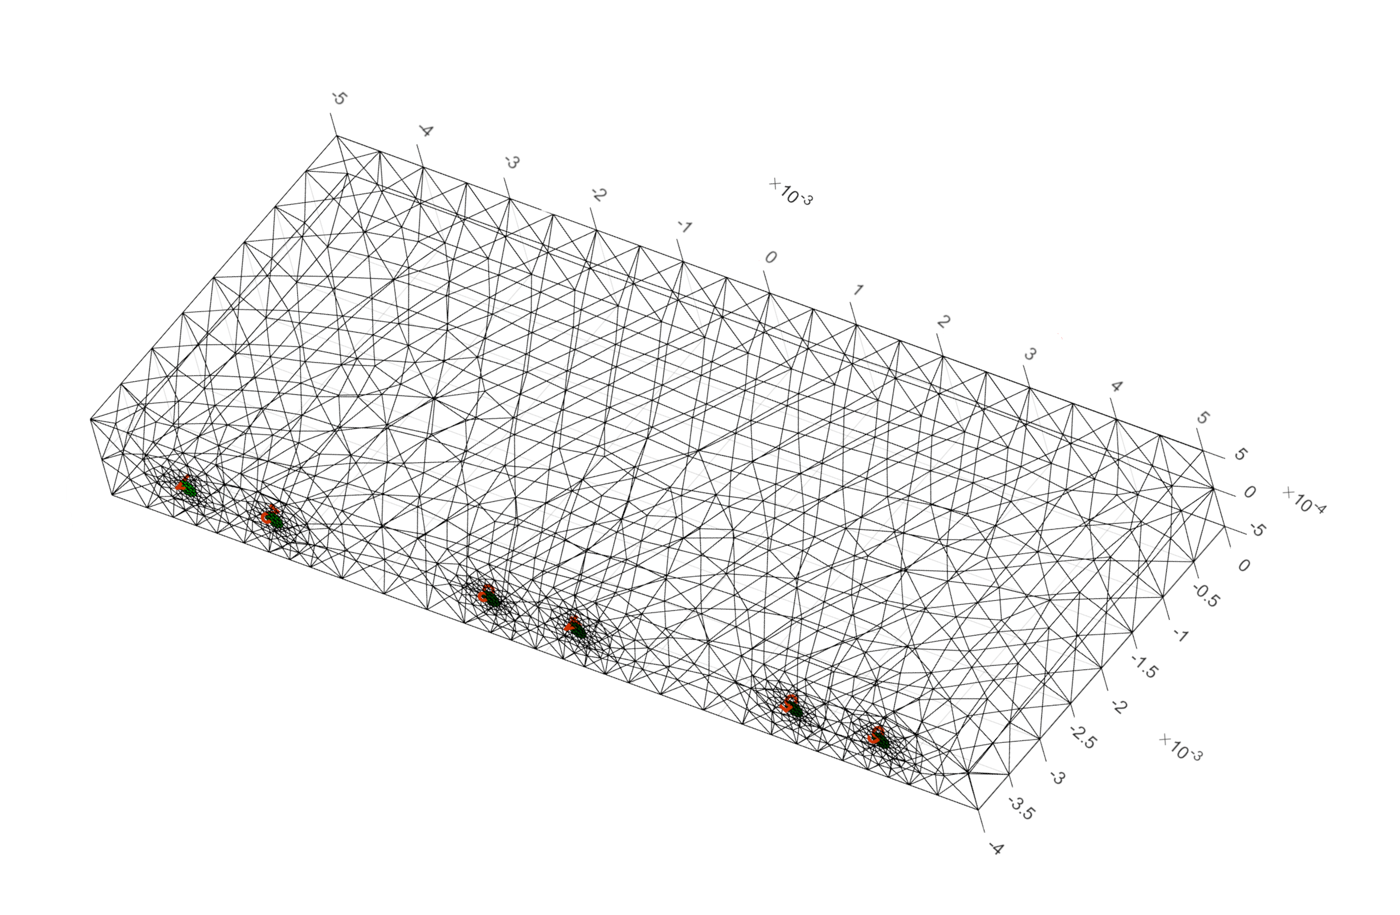
images/final_eit_chamber_eidors_iso_view.png
