cdelor02/mres-thesis/images/finger_one_bend_h_J.png

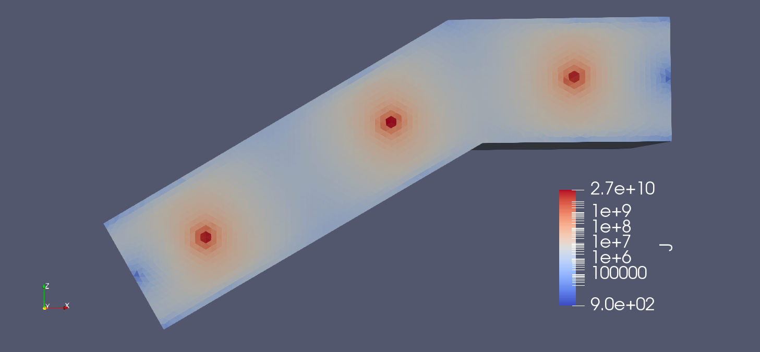
images/finger_one_bend_h_J.png
