cdelor02/mres-thesis/images/finger_straight_h_J.png

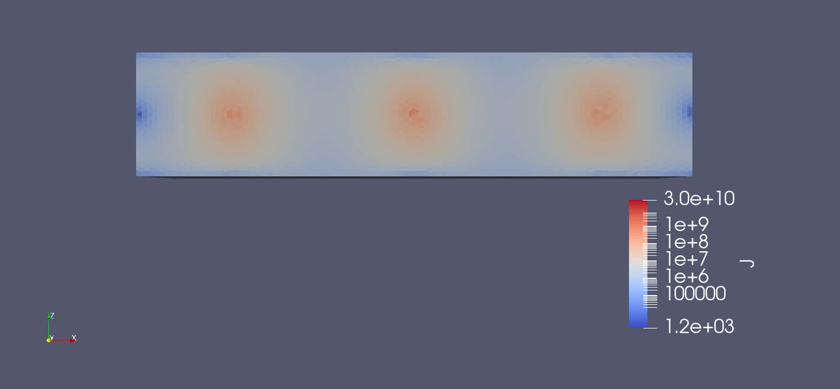
images/finger_straight_h_J.png
