cdelor02/mres-thesis/images/finger_straight_J_log_scale_conductivity.png

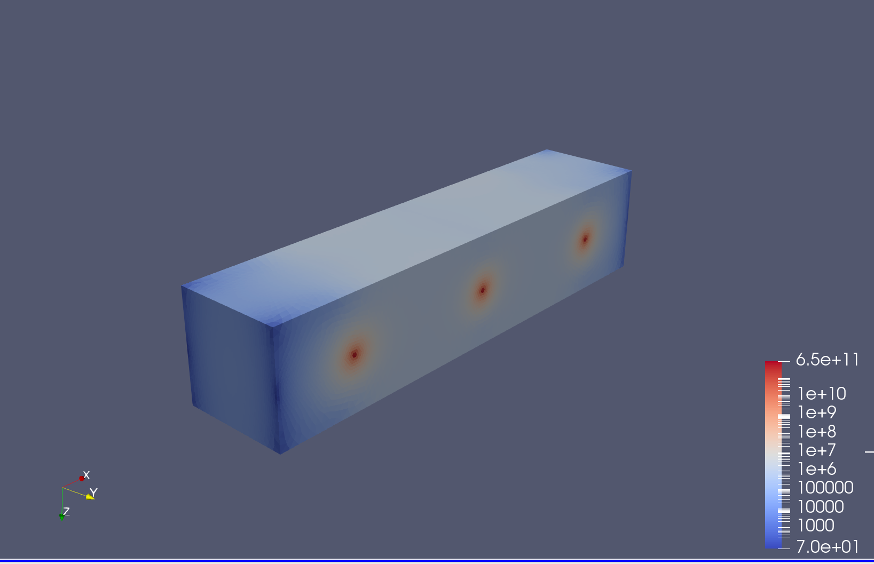
images/finger_straight_J_log_scale_conductivity.png
