cdelor02/mres-thesis/images/finger_straight_stim_1_current_field_low_mesh_count.png

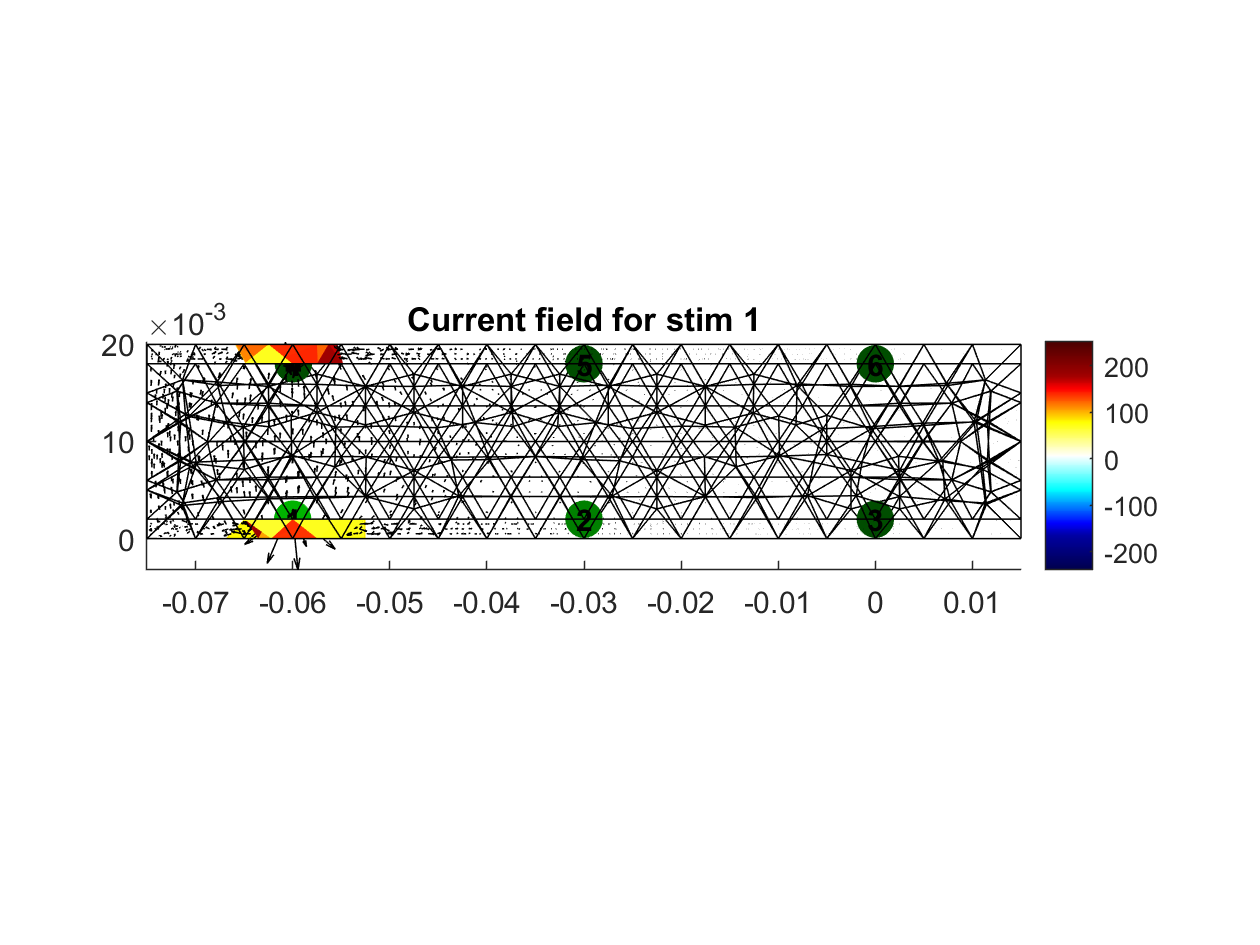
images/finger_straight_stim_1_current_field_low_mesh_count.png
