cdelor02/mres-thesis/images/finger_two_bend_fem_xz.png

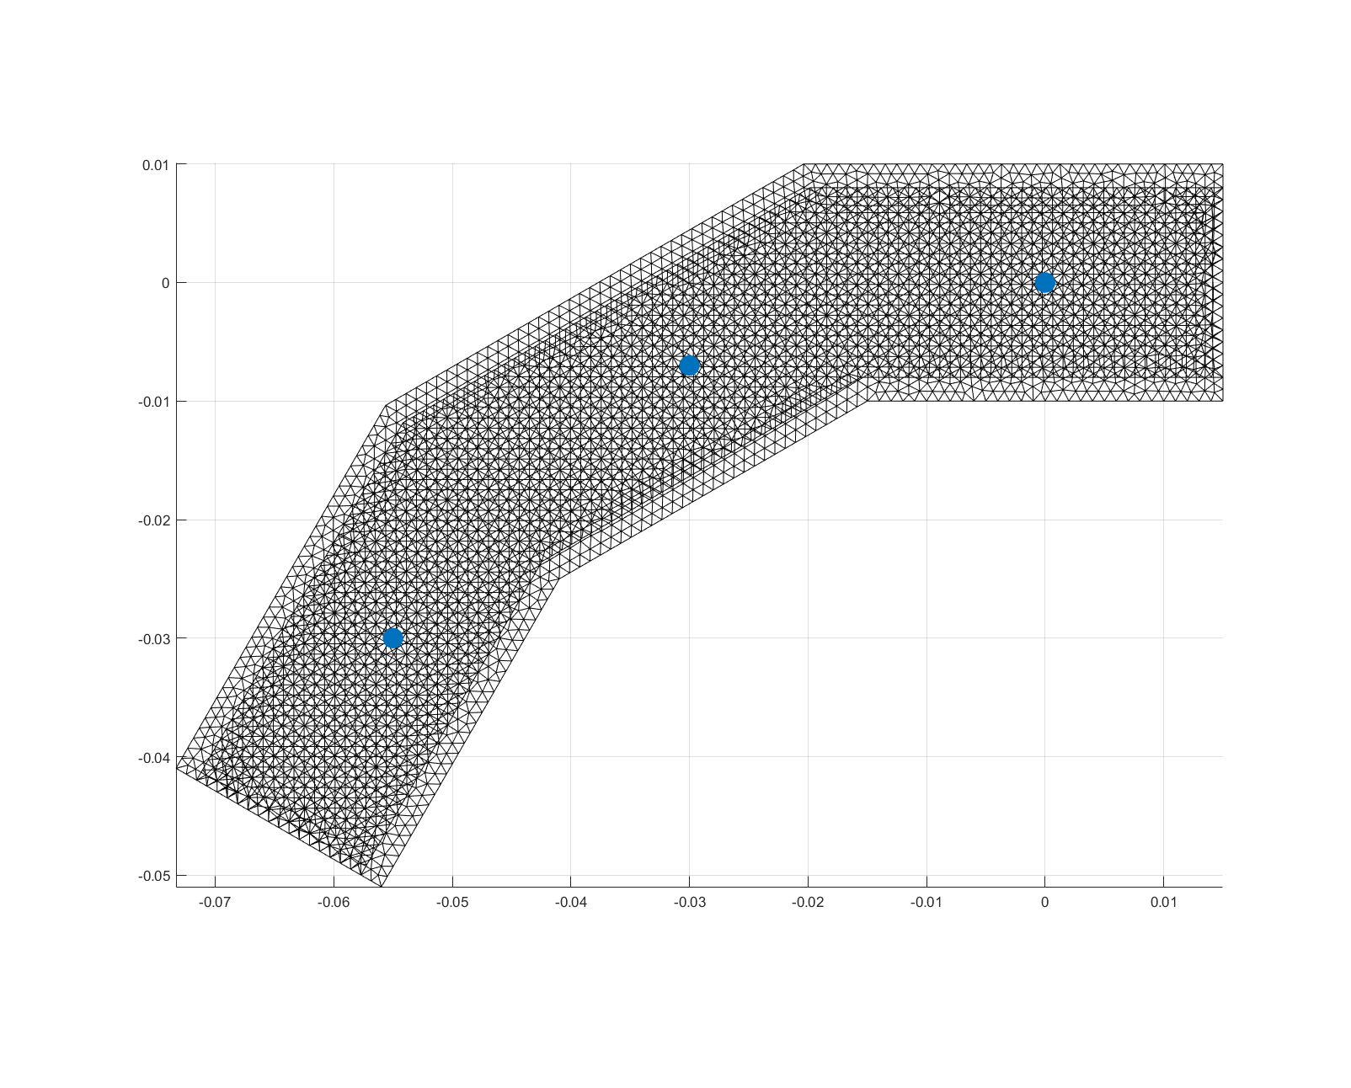
images/finger_two_bend_fem_xz.png
