cdelor02/mres-thesis/images/finger_two_bend_h_J.png

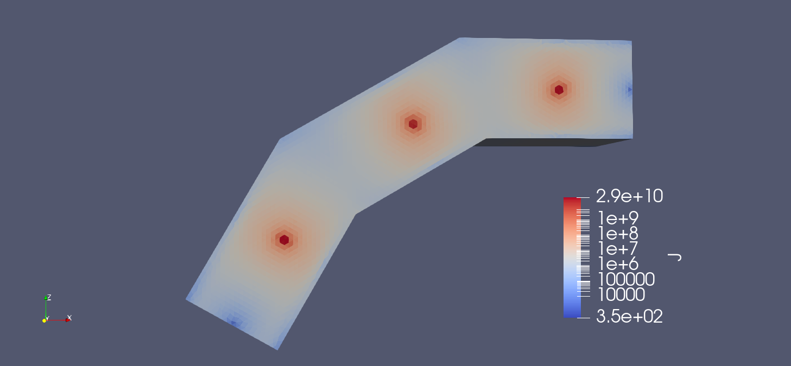
images/finger_two_bend_h_J.png
