cdelor02/mres-thesis/images/header_pins_for_electrode.jpg

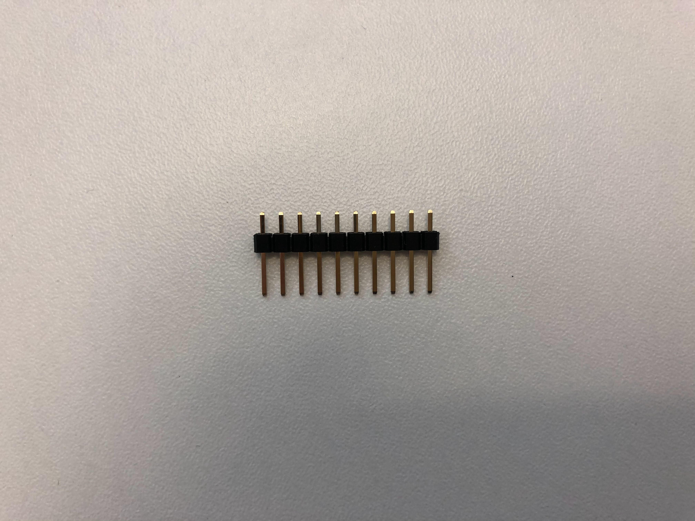
images/header_pins_for_electrode.jpg
