cdelor02/mres-thesis/images/incremental.png

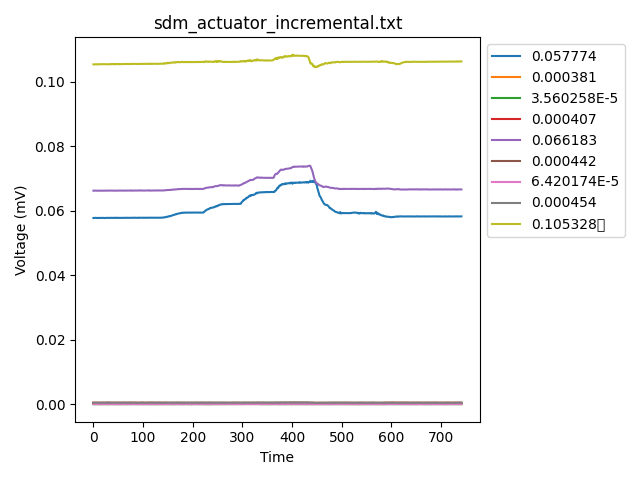
images/incremental.png
