cdelor02/mres-thesis/images/incremental_best_correct_bigger_text.png

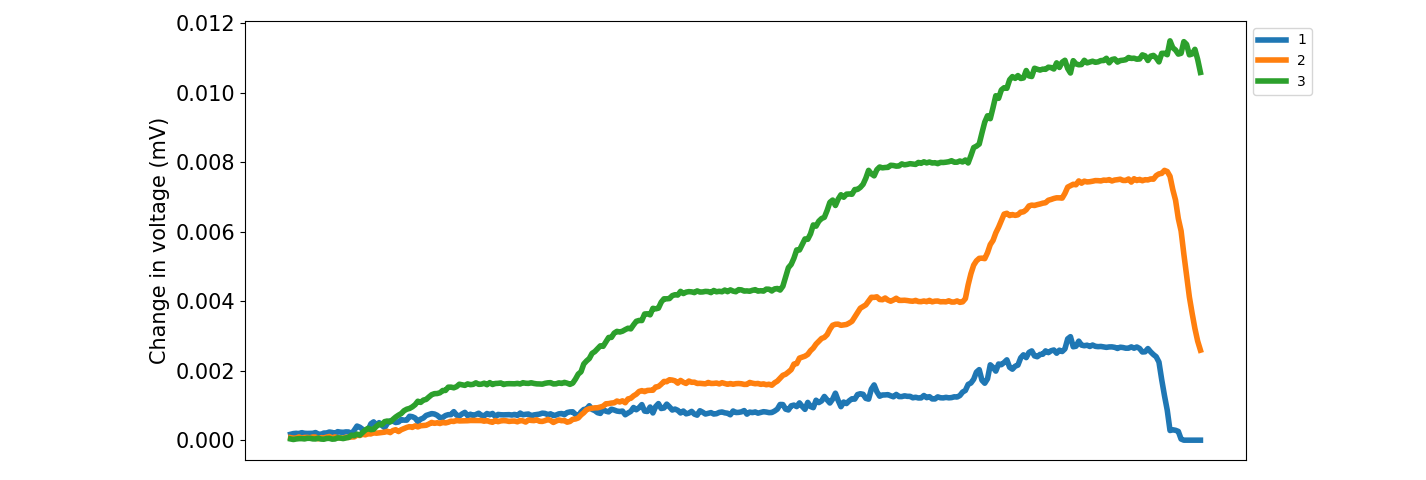
images/incremental_best_correct_bigger_text.png
