cdelor02/mres-thesis/images/incremental_best_correct_y_label.png

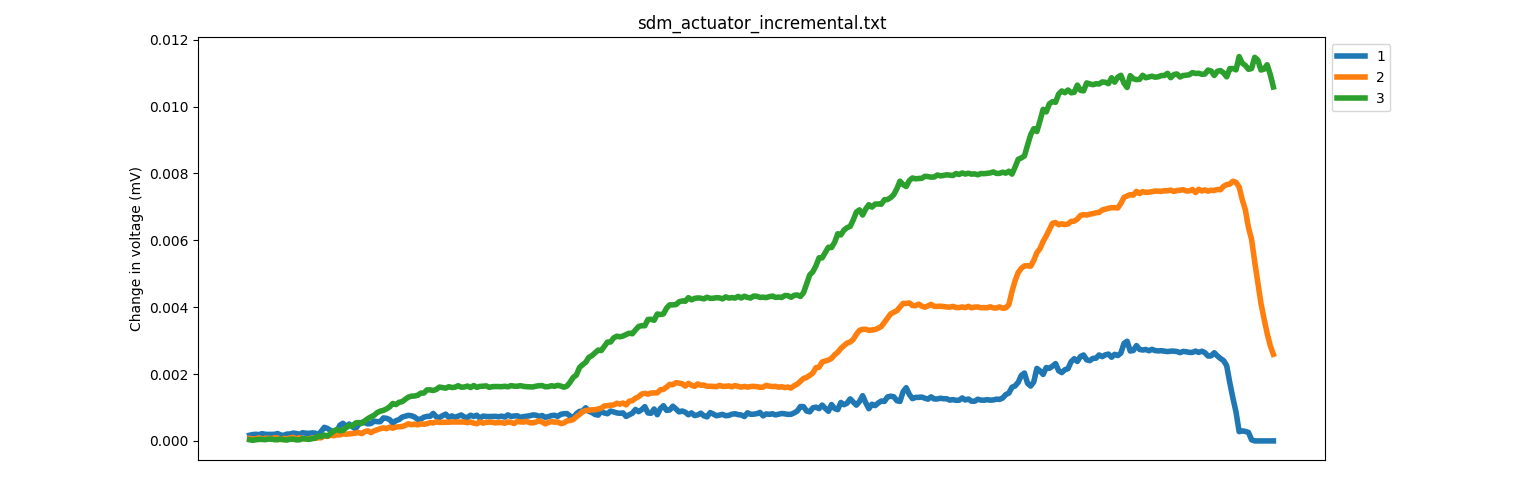
images/incremental_best_correct_y_label.png
