cdelor02/mres-thesis/images/incremental_horizontal_heatmap_plot.png

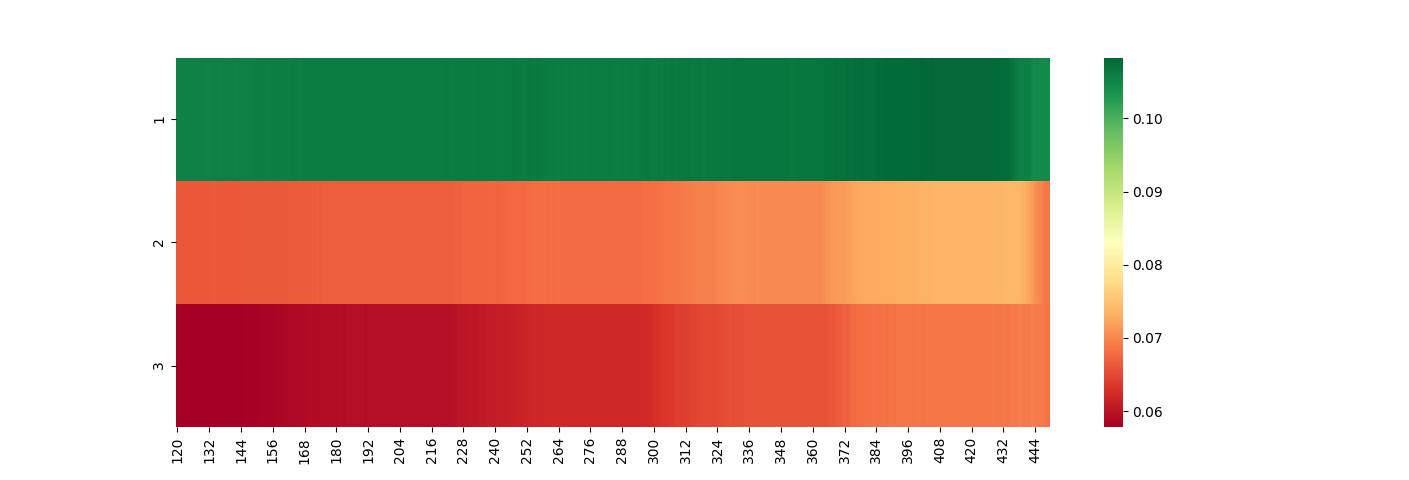
images/incremental_horizontal_heatmap_plot.png
