cdelor02/mres-thesis/images/incremental_no_x_labels.png

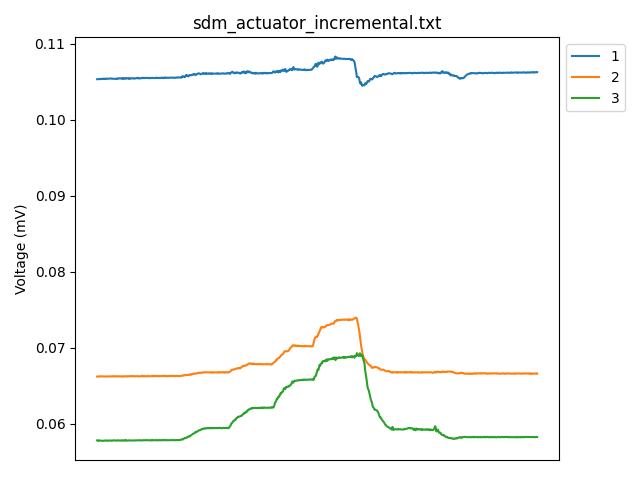
images/incremental_no_x_labels.png
