cdelor02/mres-thesis/images/incremental_no_x_labels_interesting_data_only_long_plot.png

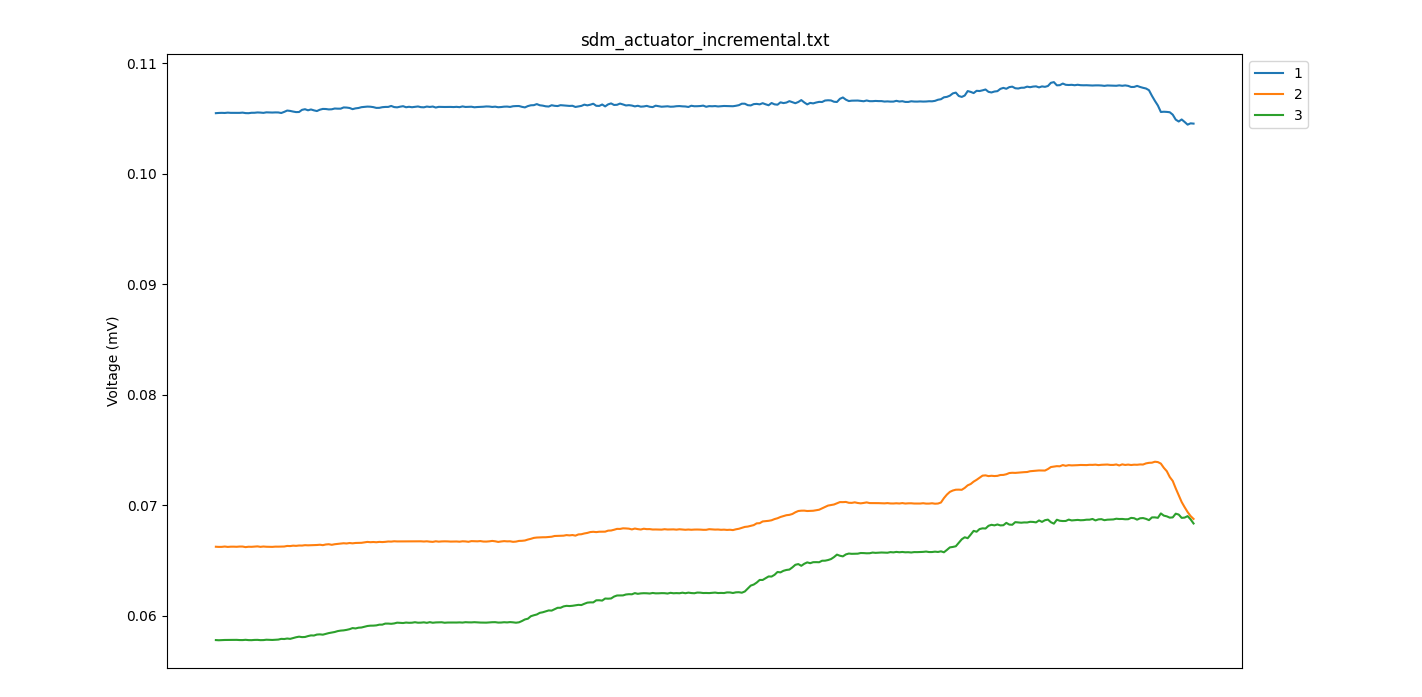
images/incremental_no_x_labels_interesting_data_only_long_plot.png
