cdelor02/mres-thesis/images/marker_detection_example_fewer_points_zoom.png

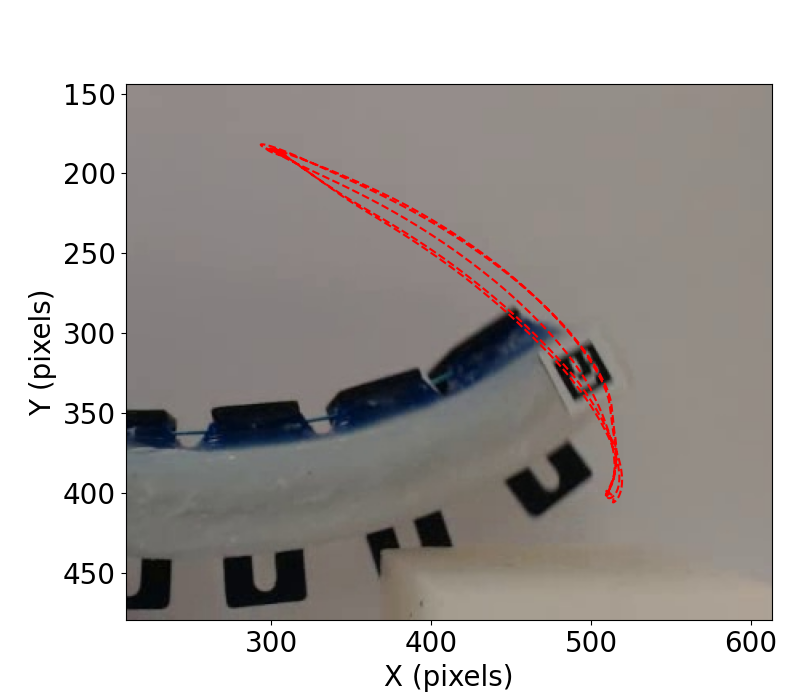
images/marker_detection_example_fewer_points_zoom.png
