cdelor02/mres-thesis/images/marker_detection_example_full.png

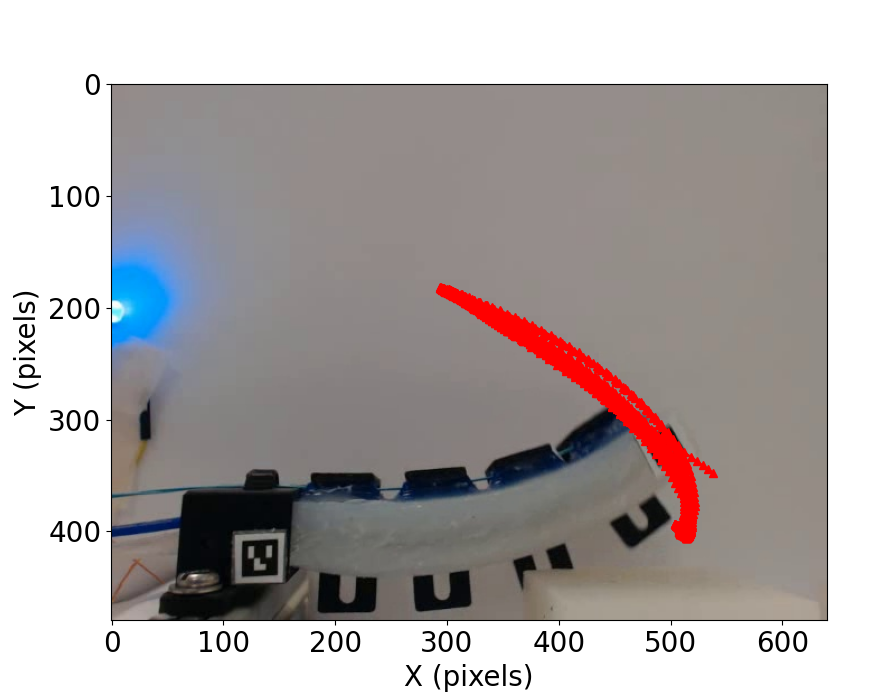
images/marker_detection_example_full.png
