cdelor02/mres-thesis/images/marker_detection_example_full_fewer_points.png

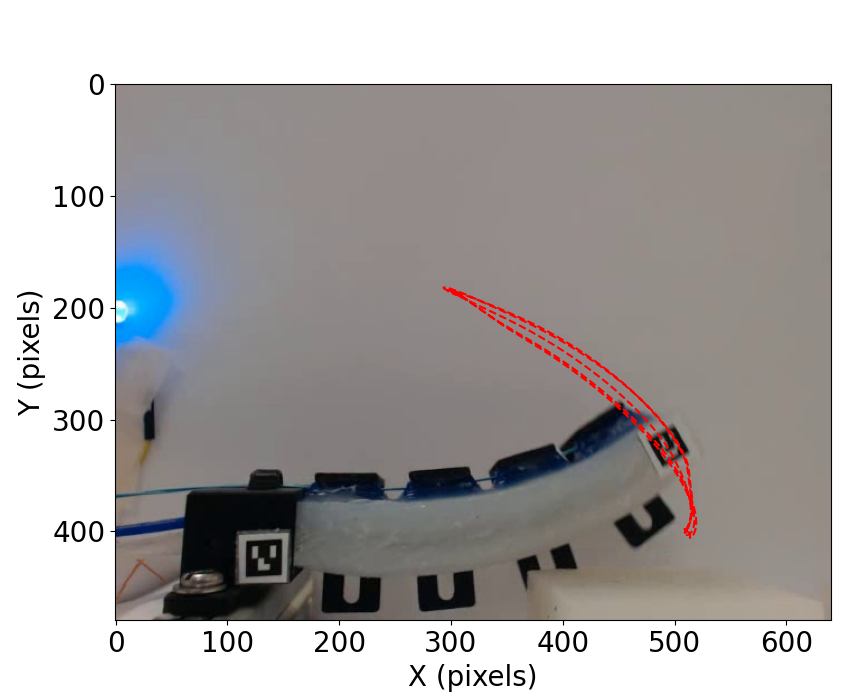
images/marker_detection_example_full_fewer_points.png
