cdelor02/mres-thesis/images/marker_detection_example_zoom2.png

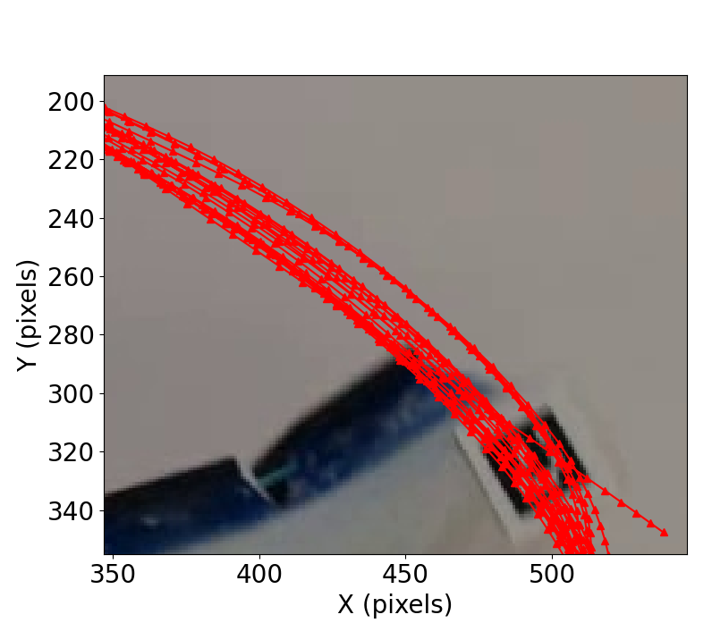
images/marker_detection_example_zoom2.png
