cdelor02/mres-thesis/images/marker_detection_example_zoom.png

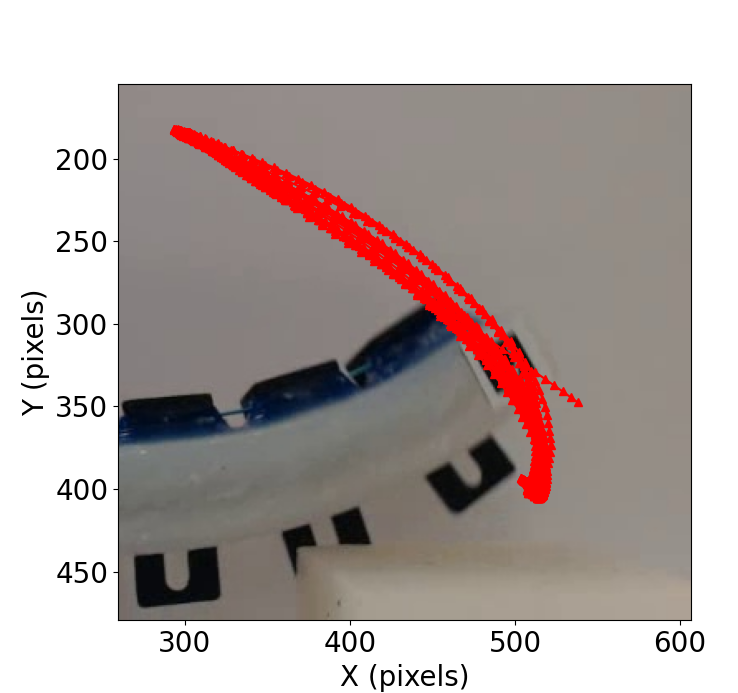
images/marker_detection_example_zoom.png
