cdelor02/mres-thesis/images/means_of_flex_voltages_across_all_episodes.png

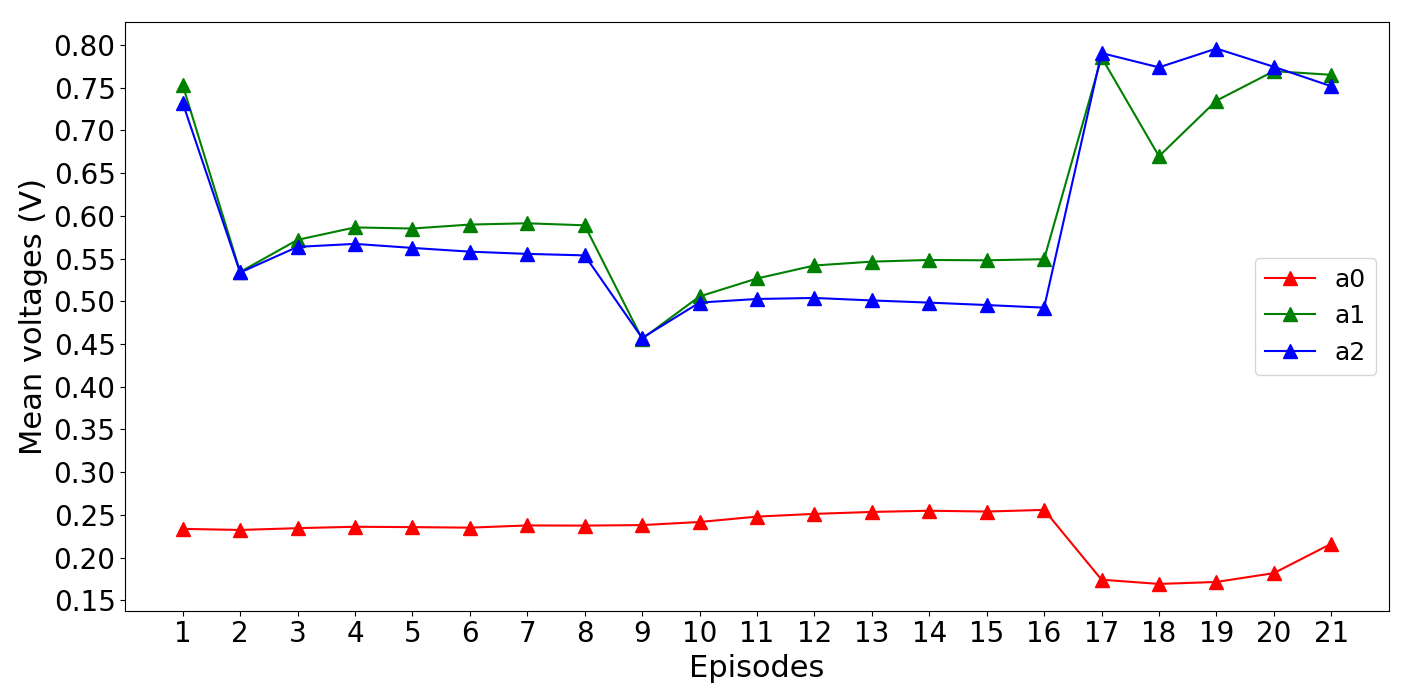
images/means_of_flex_voltages_across_all_episodes.png
