cdelor02/mres-thesis/images/opencv_red_contour_tracking.png

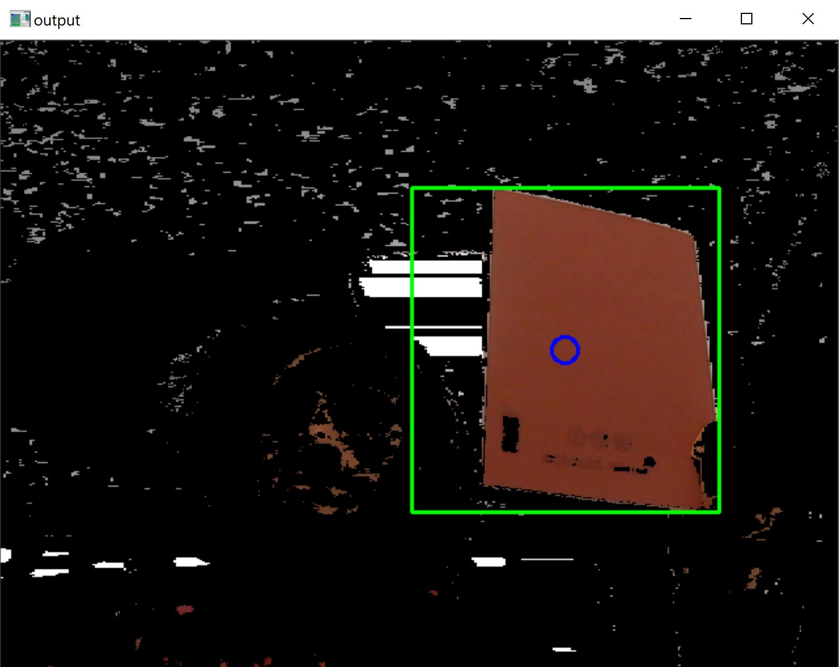
images/opencv_red_contour_tracking.png
