cdelor02/mres-thesis/images/pneunet_first_bend_chamber_voltages.png

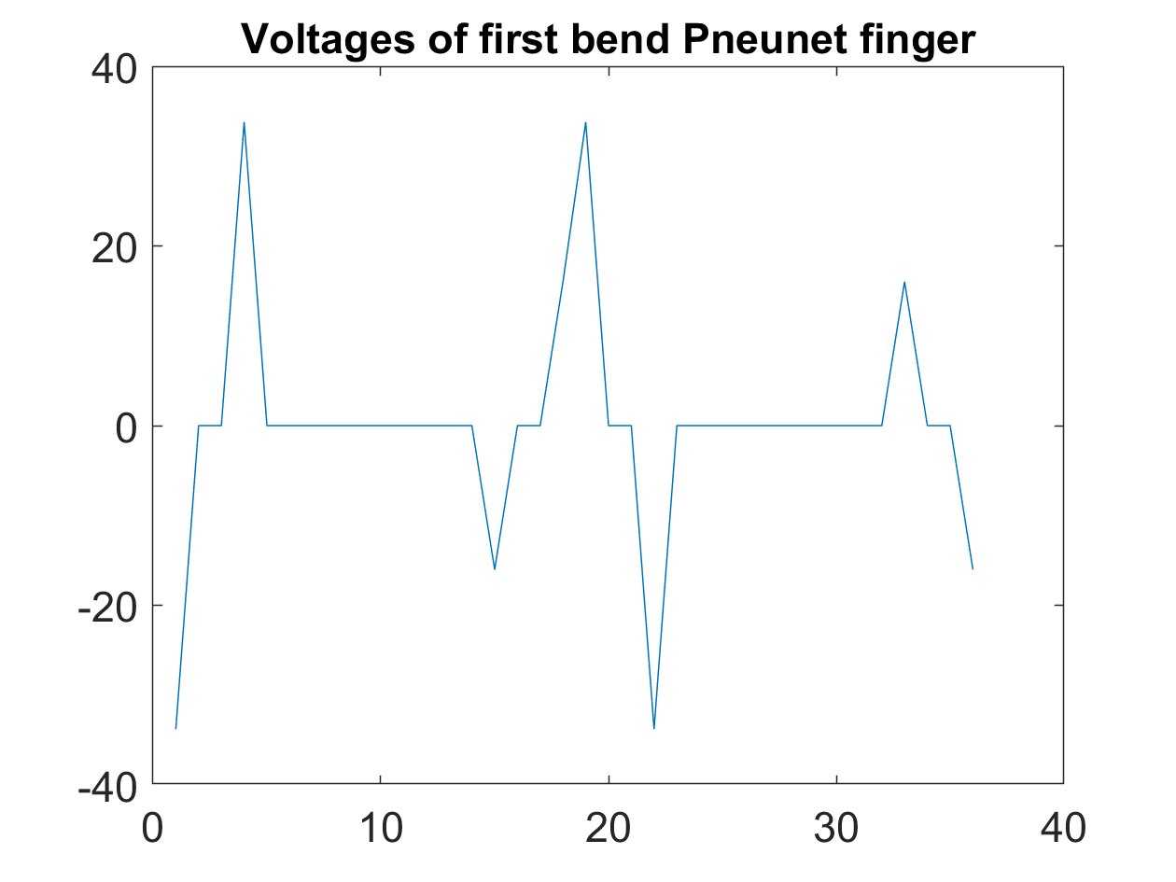
images/pneunet_first_bend_chamber_voltages.png
