cdelor02/mres-thesis/images/pneunet_first_bend_INFLATED_voltages.png

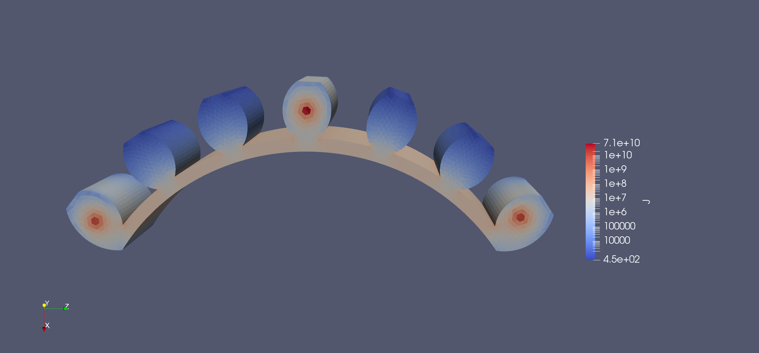
images/pneunet_first_bend_INFLATED_voltages.png
