cdelor02/mres-thesis/images/pneunet_first_bend_J.png

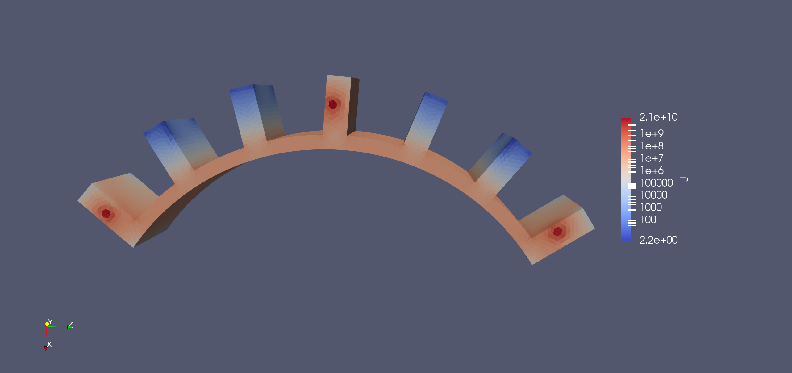
images/pneunet_first_bend_J.png
