cdelor02/mres-thesis/images/pneunet_mesh_electrode_locations.png

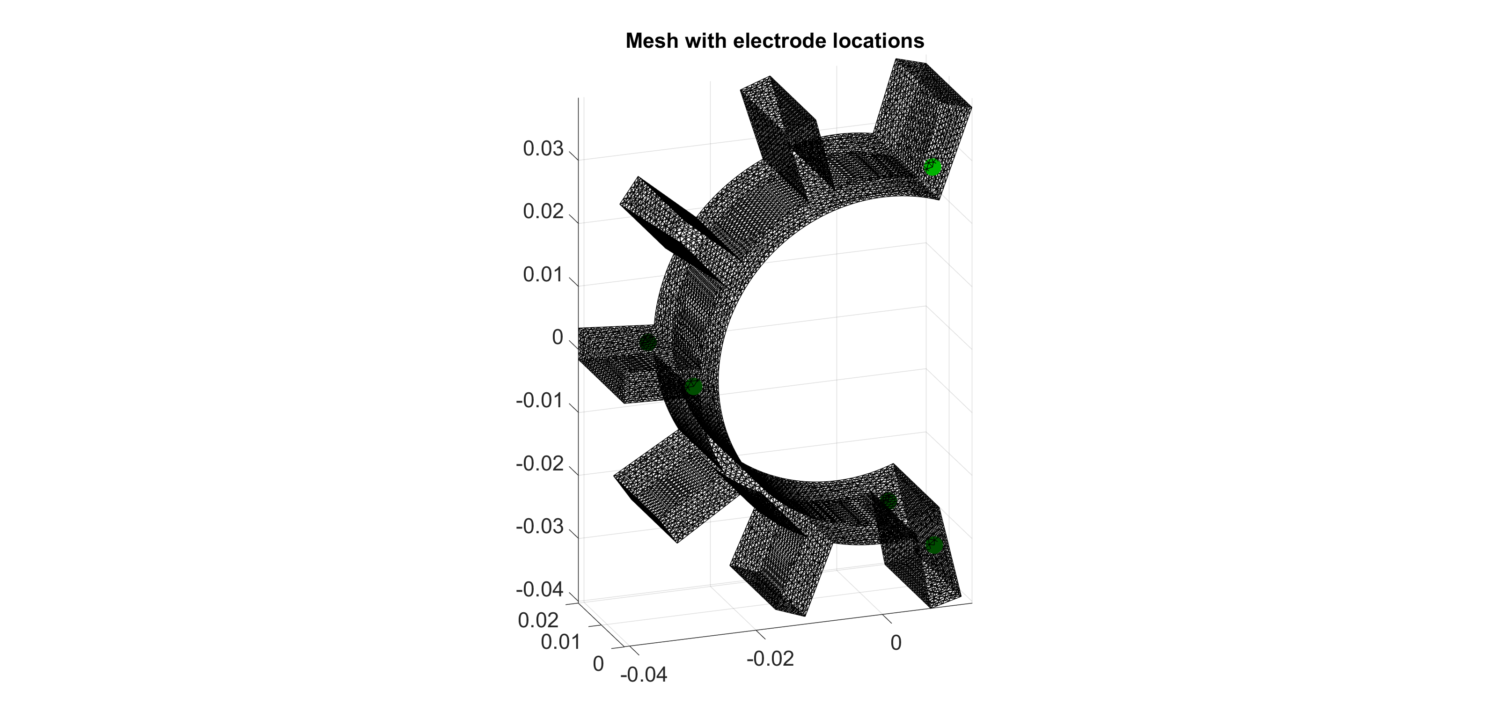
images/pneunet_mesh_electrode_locations.png
