cdelor02/mres-thesis/images/pneunet_second_bend_J.png

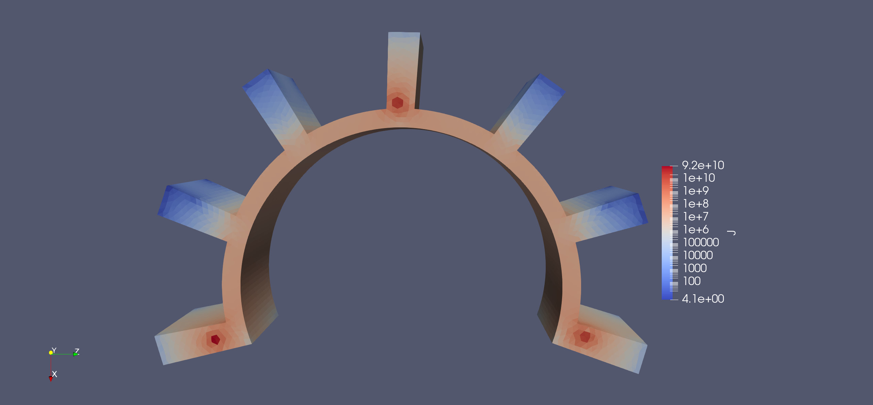
images/pneunet_second_bend_J.png
