cdelor02/mres-thesis/images/pneunet_straight_chamber_voltages.png

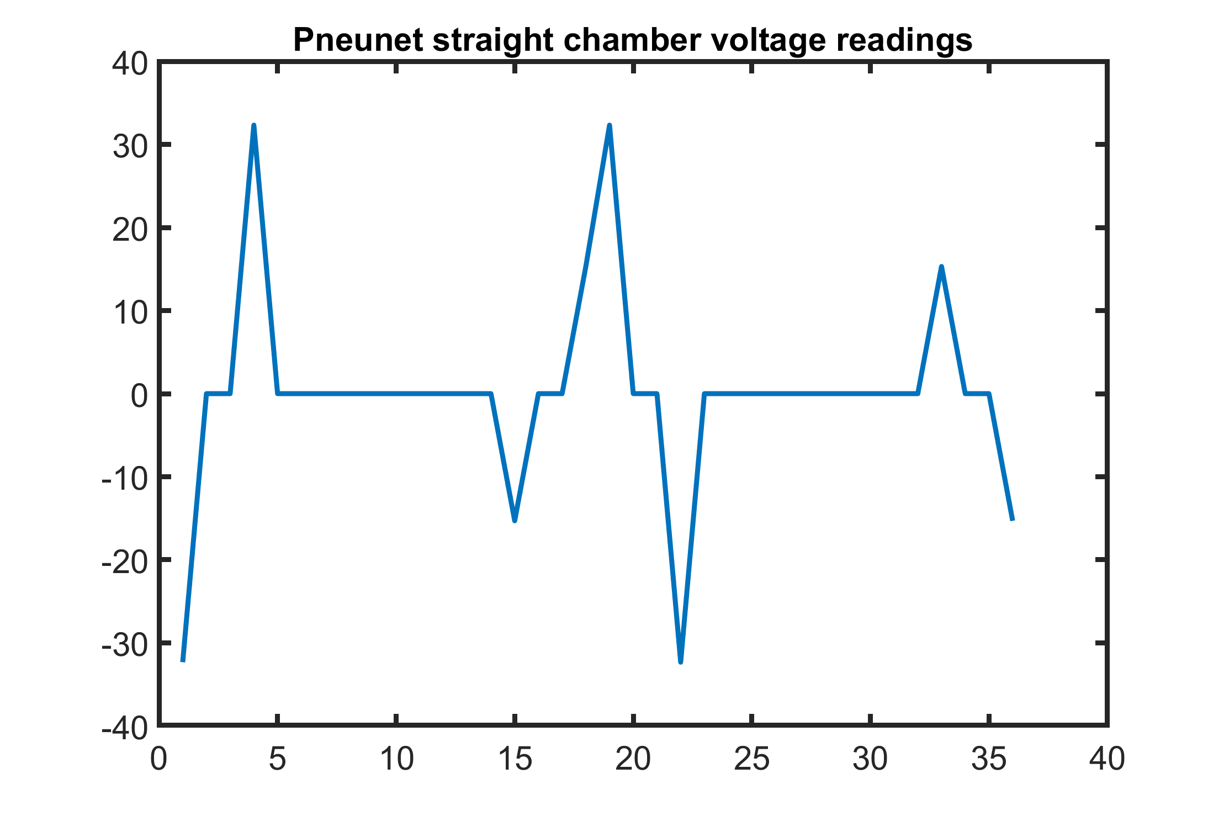
images/pneunet_straight_chamber_voltages.png
