cdelor02/mres-thesis/images/sdm_actuator_continuous.png

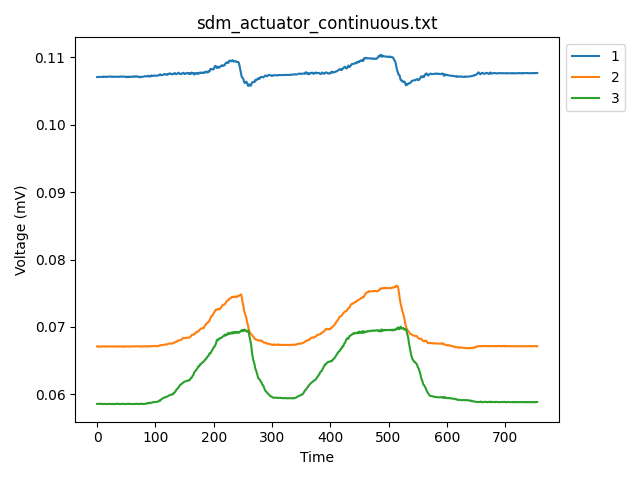
images/sdm_actuator_continuous.png
