cdelor02/mres-thesis/images/sdm_actuator_incremental.png

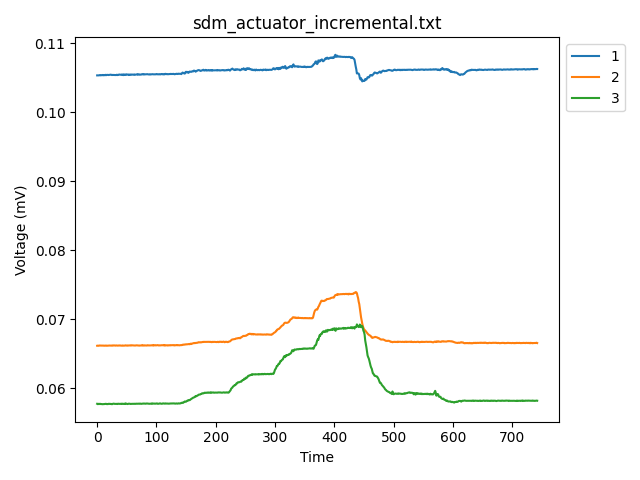
images/sdm_actuator_incremental.png
