cdelor02/mres-thesis/images/sdm_actuator_tip_contact.png

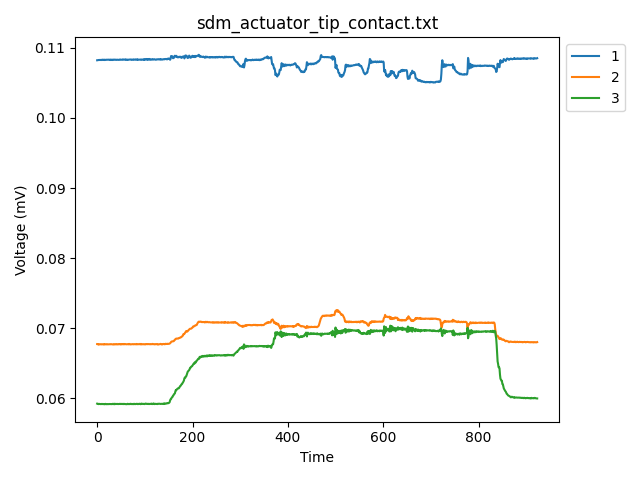
images/sdm_actuator_tip_contact.png
