cdelor02/mres-thesis/images/SDM_finger_w_chamber_flexed.jpg

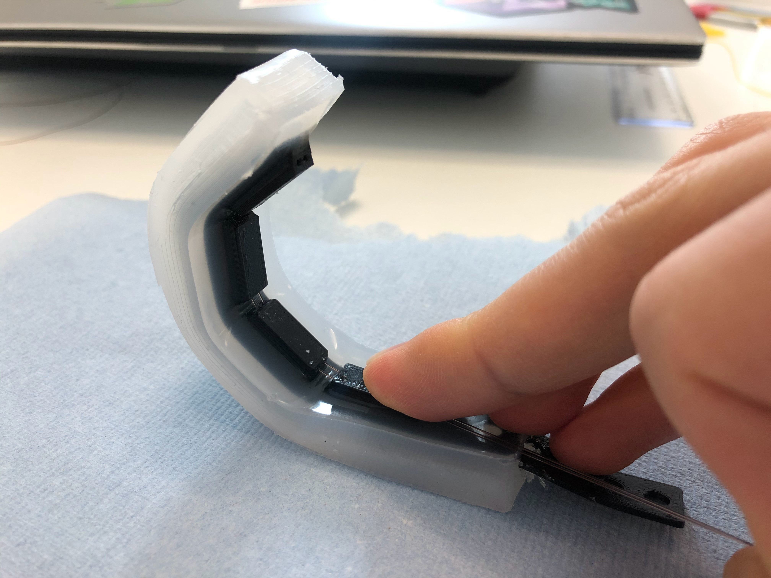
images/SDM_finger_w_chamber_flexed.jpg
