cdelor02/mres-thesis/images/SDM_finger_w_chamber_iso.jpg

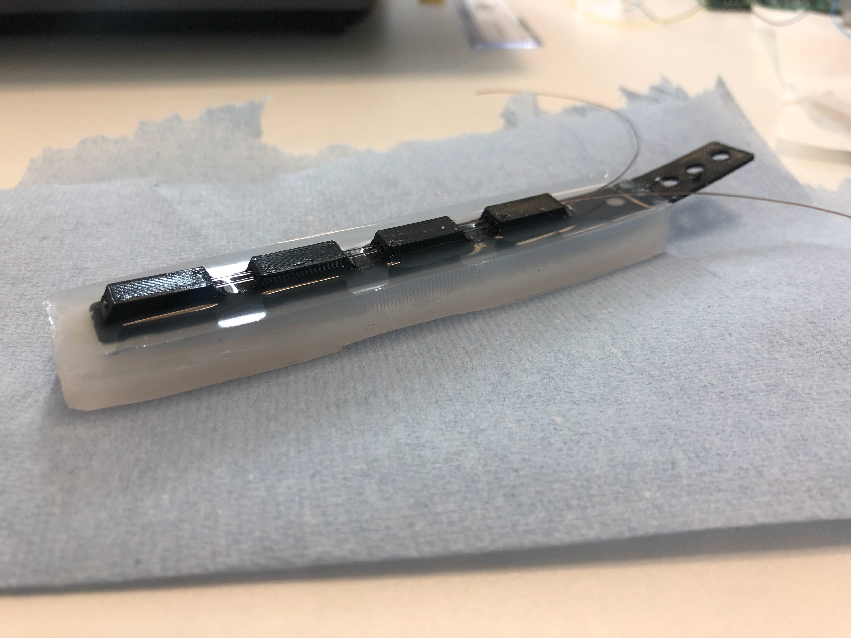
images/SDM_finger_w_chamber_iso.jpg
