cdelor02/mres-thesis/images/sdm_tip_contact.png

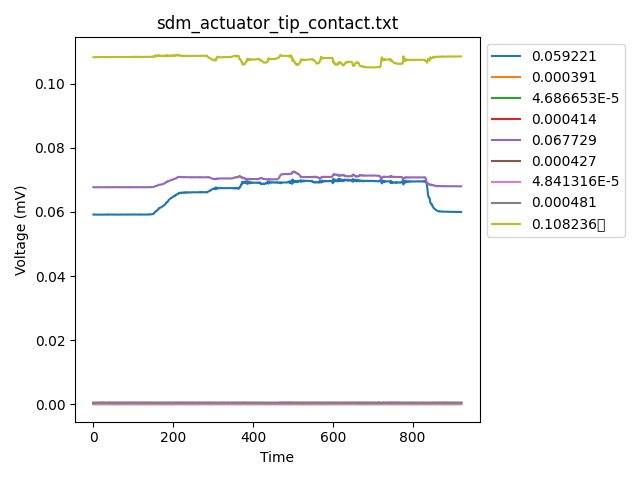
images/sdm_tip_contact.png
