cdelor02/mres-thesis/images/standard_deviation_of_flex_voltages_across_all_episodes.png

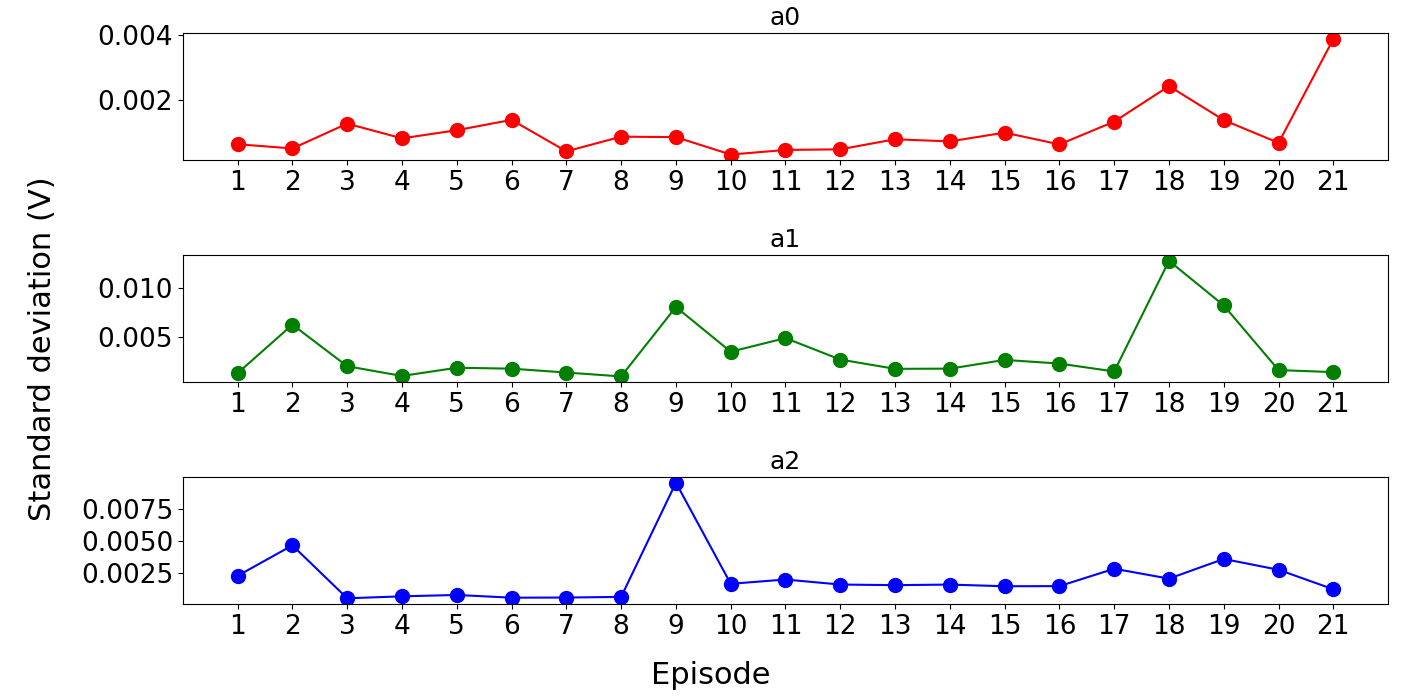
images/standard_deviation_of_flex_voltages_across_all_episodes.png
