cdelor02/mres-thesis/images/two_bend_finger_v_baseline_meas.png

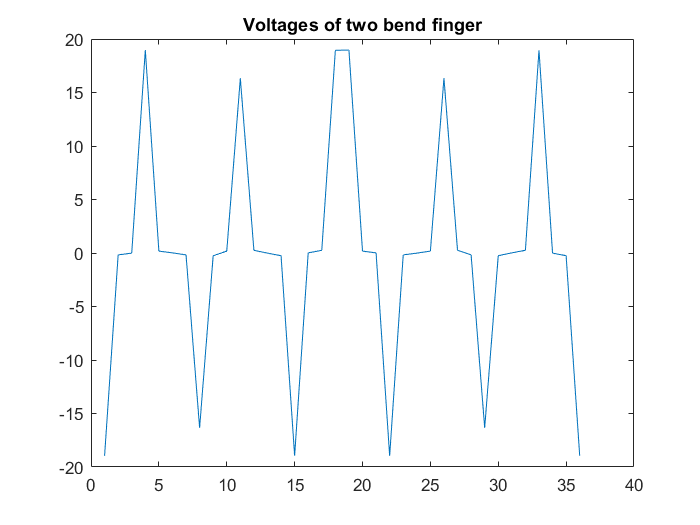
images/two_bend_finger_v_baseline_meas.png
