cdelor02/mres-thesis/images/voltages_overlaid.png

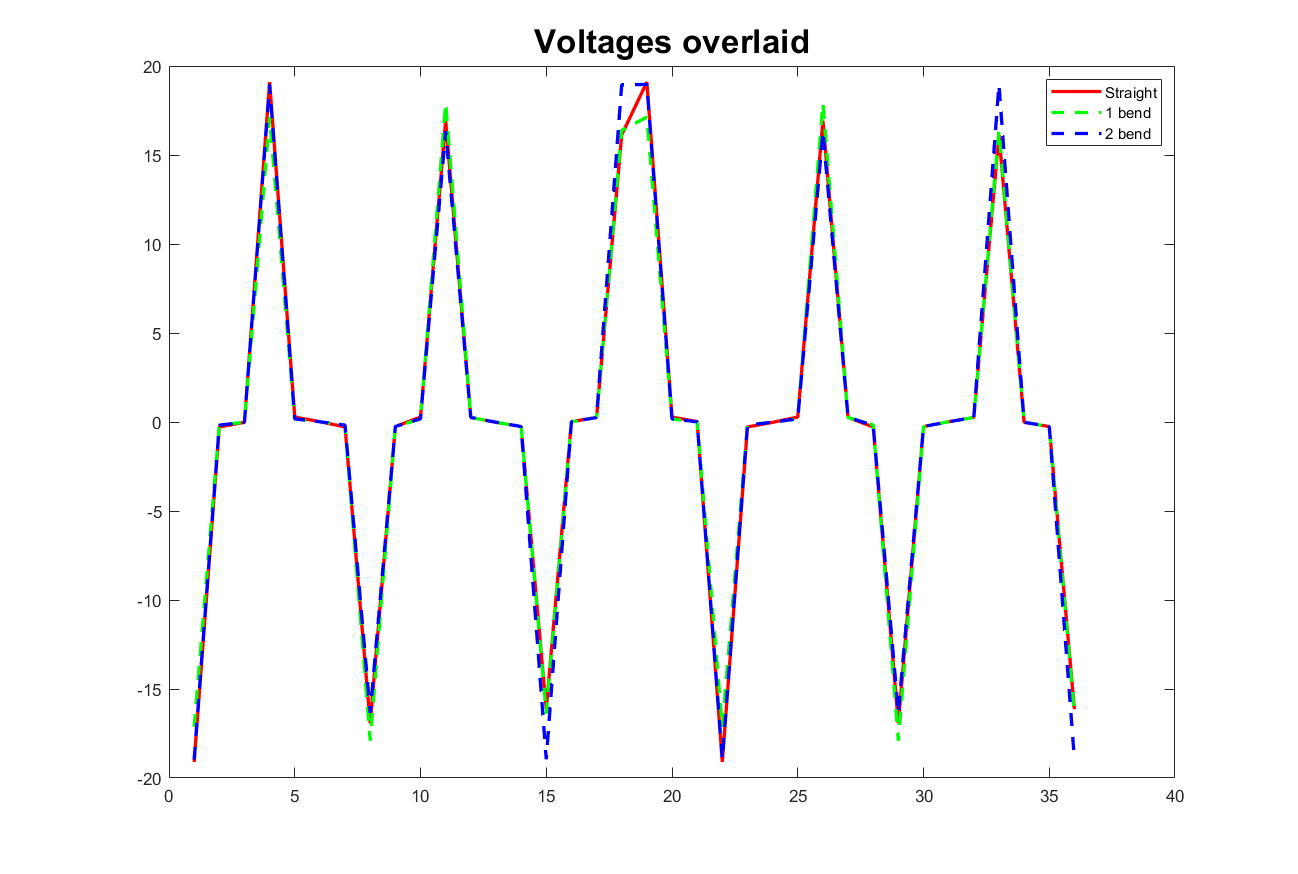
images/voltages_overlaid.png
