cdelor02/mres-thesis/images/voltages_overlaid_zoom.png

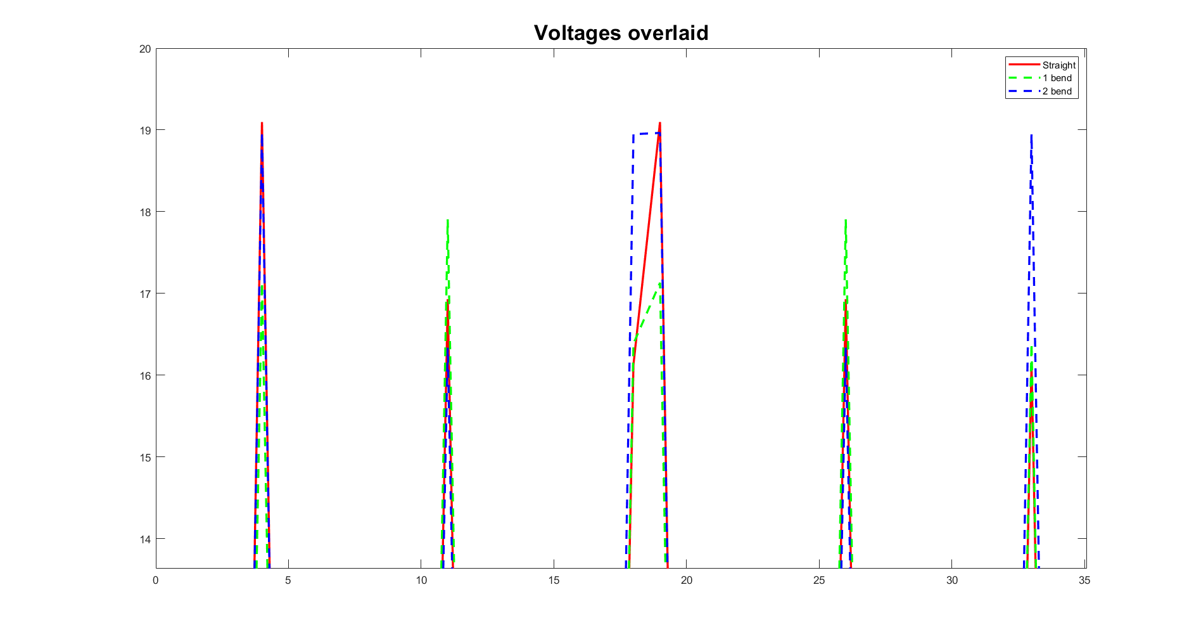
images/voltages_overlaid_zoom.png
