cdelor02/mres-thesis/images/wired_actuator_side.jpg

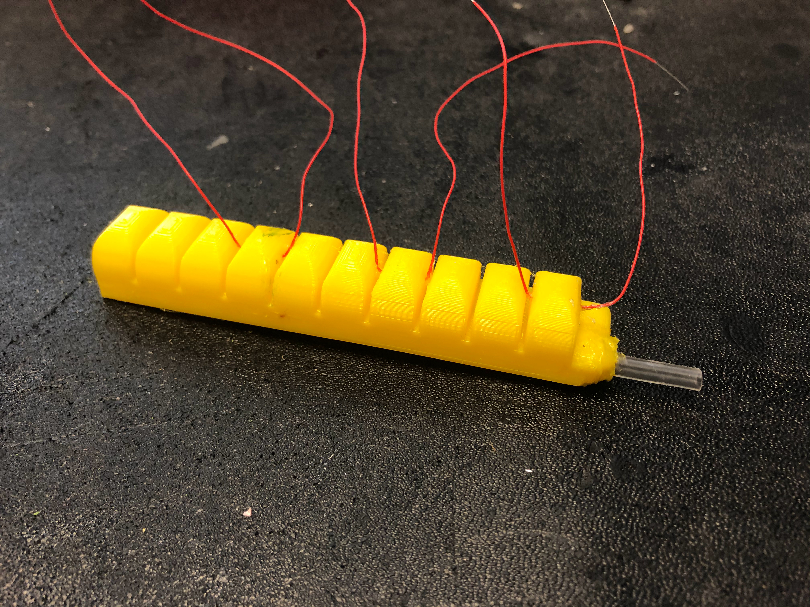
images/wired_actuator_side.jpg
