cdelor02/mres-thesis/images/wired_actuator_side_view.jpg

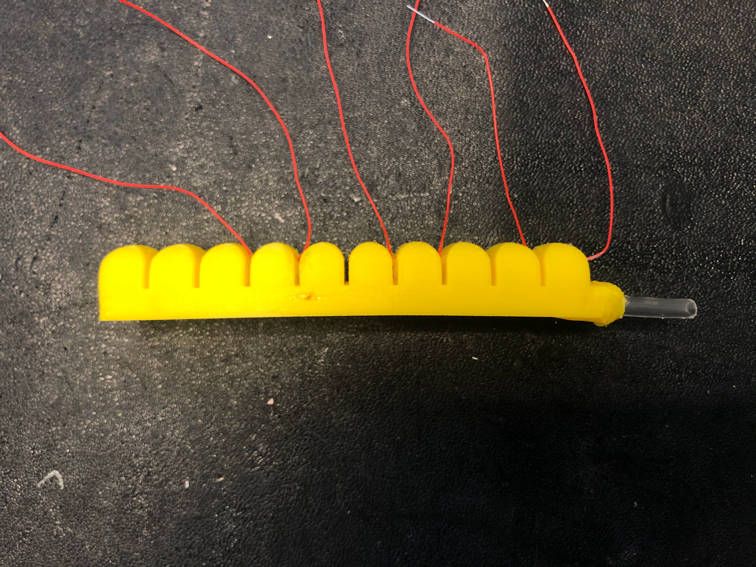
images/wired_actuator_side_view.jpg
