cdelor02/mres-thesis/journal_club_presentation/soft_robot_actuator_figures/Fig_S3_sensor_response_to_tip_contact-kinematic-modeling.png

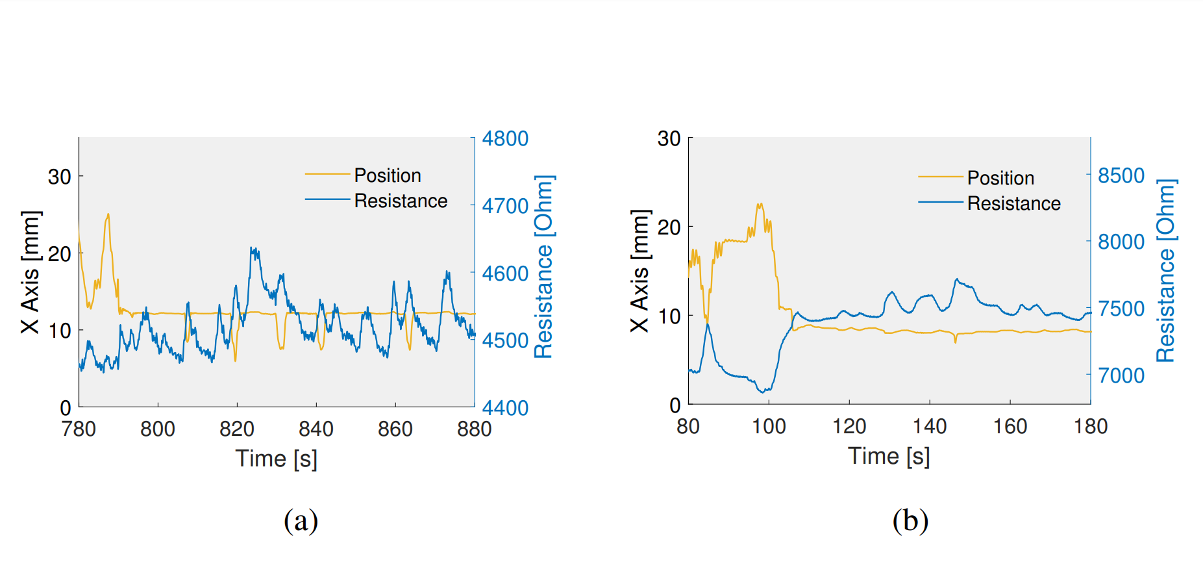
journal_club_presentation/soft_robot_actuator_figures/Fig_S3_sensor_response_to_tip_contact-kinematic-modeling.png
