cdelor02/mres-thesis/journal_club_presentation/soft_robot_actuator_figures/Figure_S1_modeling_architecture.png

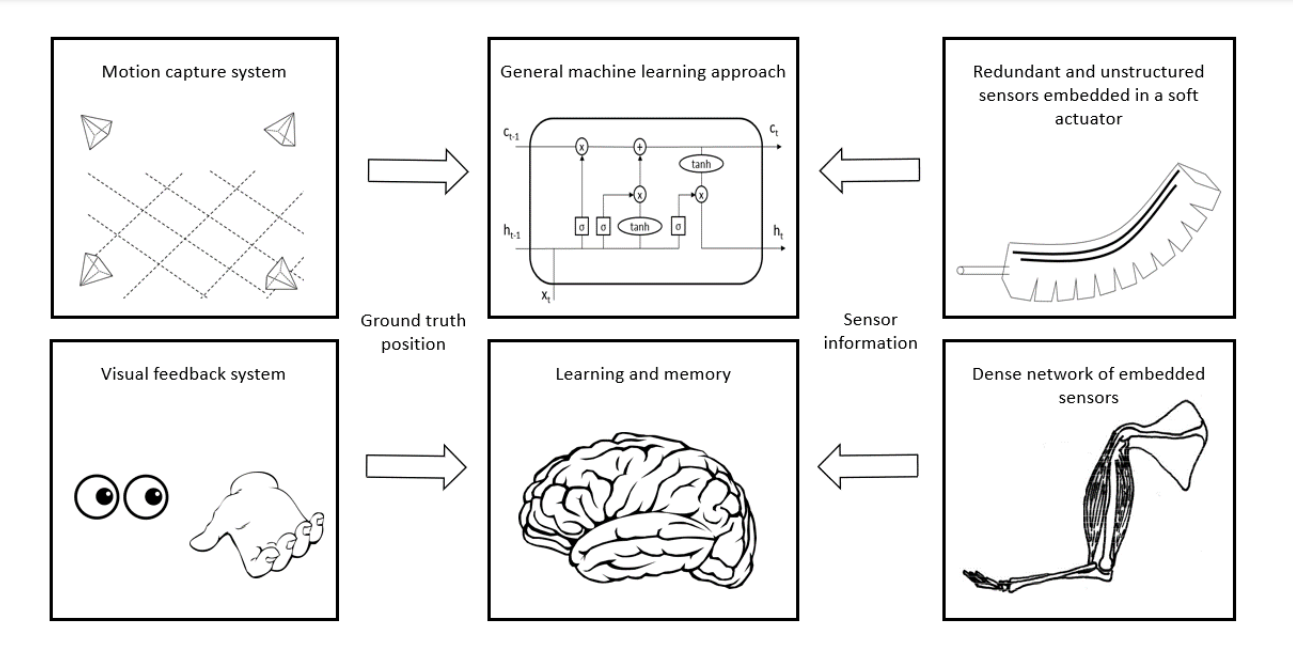
journal_club_presentation/soft_robot_actuator_figures/Figure_S1_modeling_architecture.png
