cdelor02/mres-thesis/literature_review/figures/41598_2019_41774_Fig3_HTML.jpg

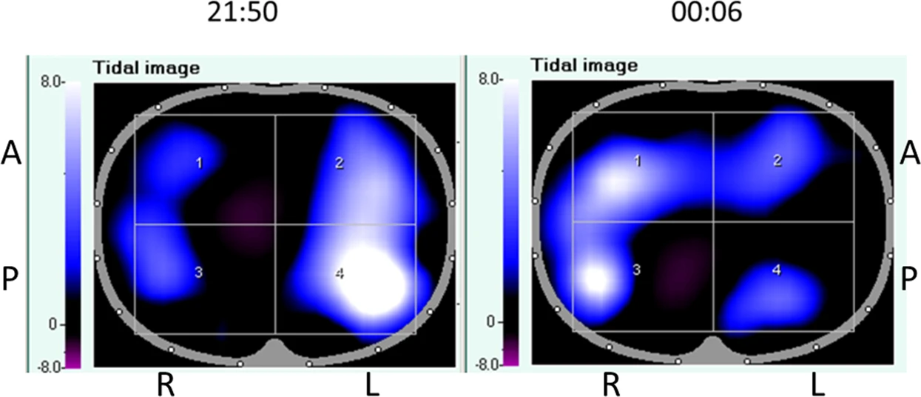
literature_review/figures/41598_2019_41774_Fig3_HTML.jpg
