cdelor02/mres-thesis/literature_review/figures/EIT_principles_diagram.jpg

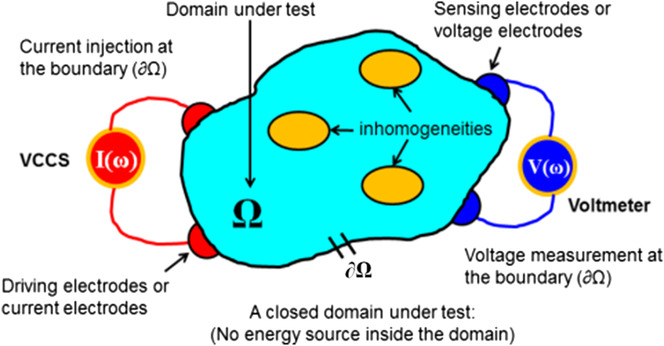
literature_review/figures/EIT_principles_diagram.jpg
