cdelor02/mres-thesis/literature_review/figures/soft_robot_actuator_types.jpg

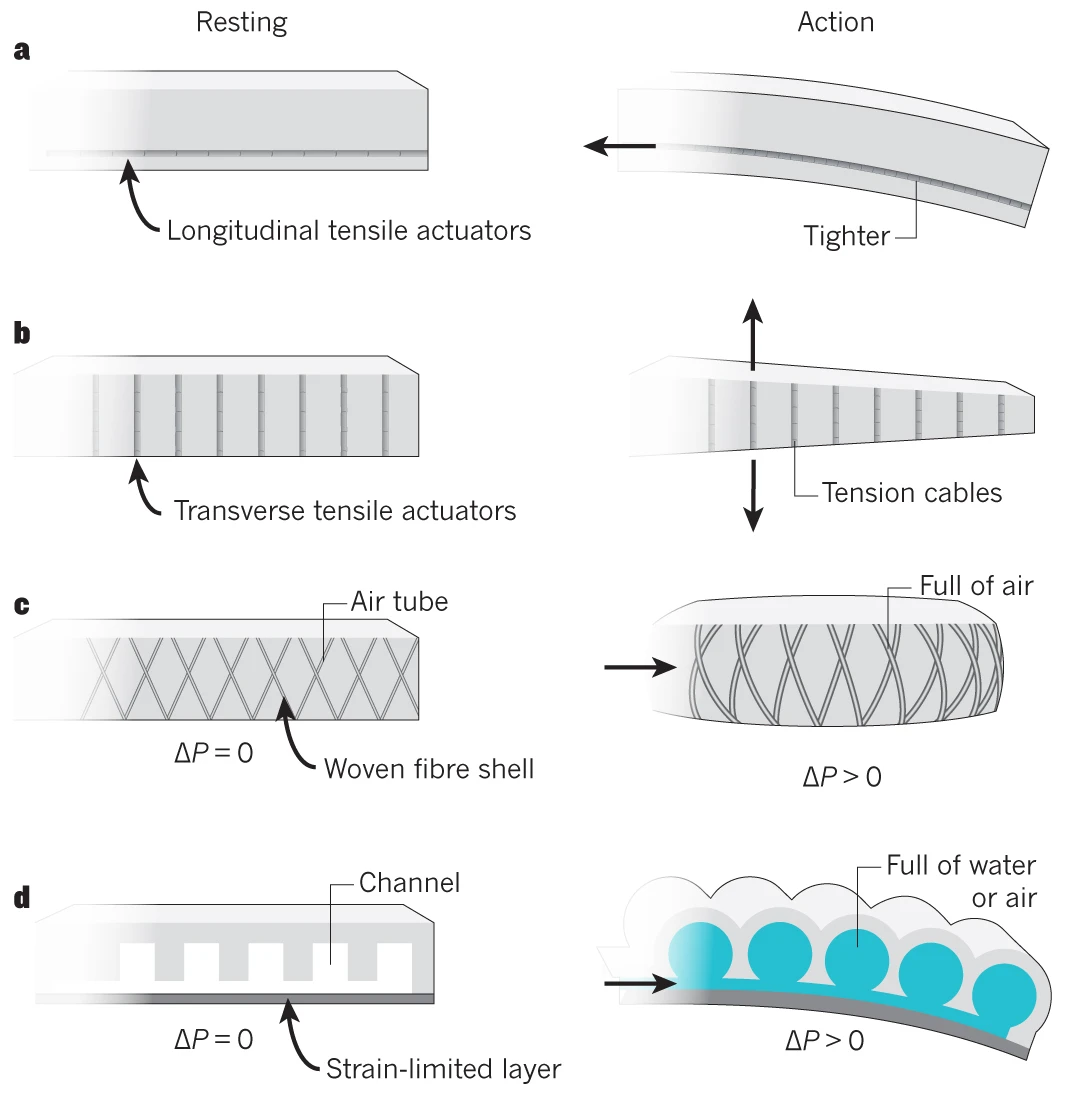
literature_review/figures/soft_robot_actuator_types.jpg
