cdelor02/mres-thesis/literature_review/figures/soft_robot_examples.jpg

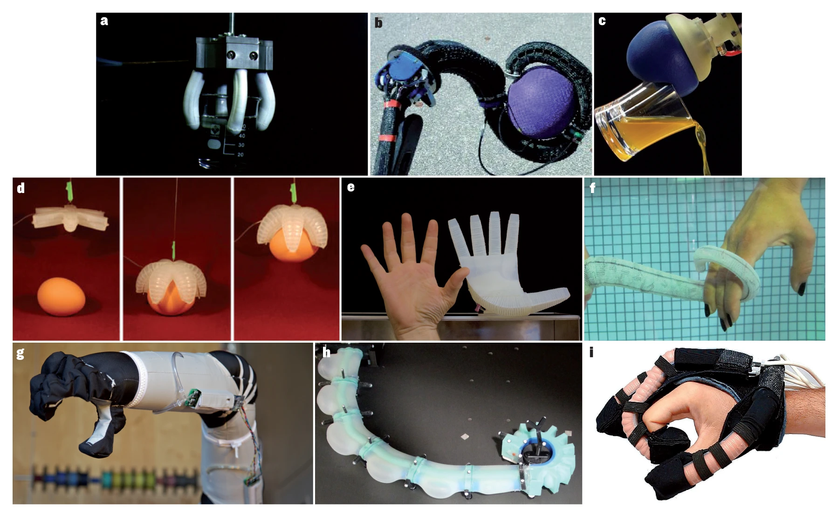
literature_review/figures/soft_robot_examples.jpg
