cdelor02/mres-thesis/ML/EIT_vs_cable_pull_data--5_iterations.jpg

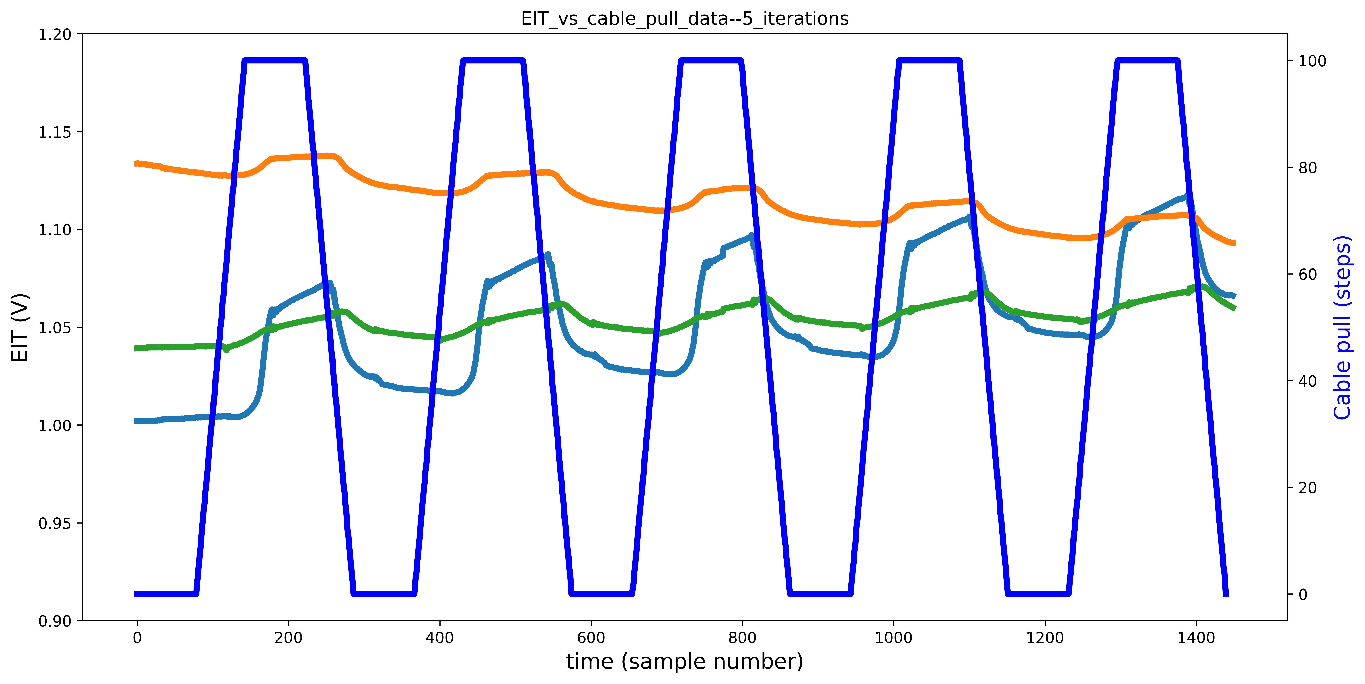
ML/EIT_vs_cable_pull_data--5_iterations.jpg
