cdelor02/mres-thesis/ML/EIT_vs_cable_pull_data--5_iterations_bigger_font.jpg

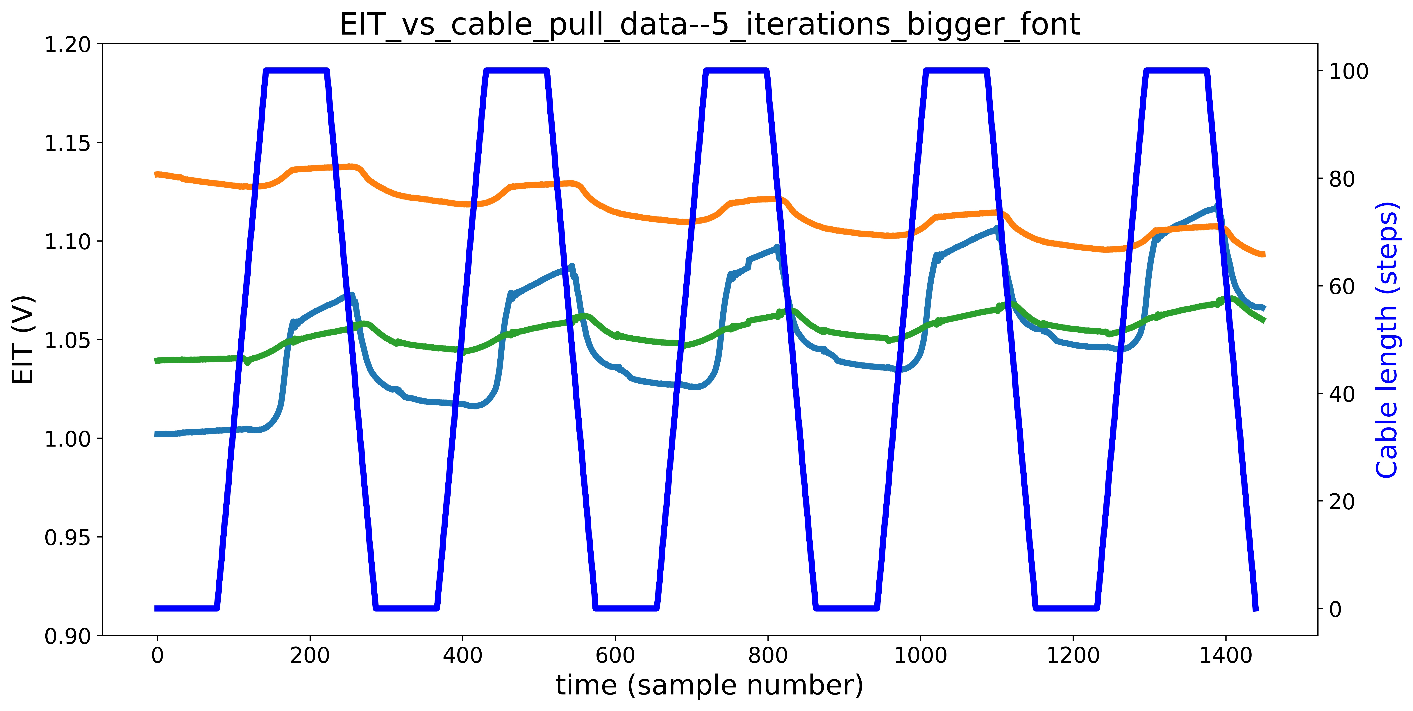
ML/EIT_vs_cable_pull_data--5_iterations_bigger_font.jpg
