cdelor02/mres-thesis/ML/finger_with_plotted_trajectory.png

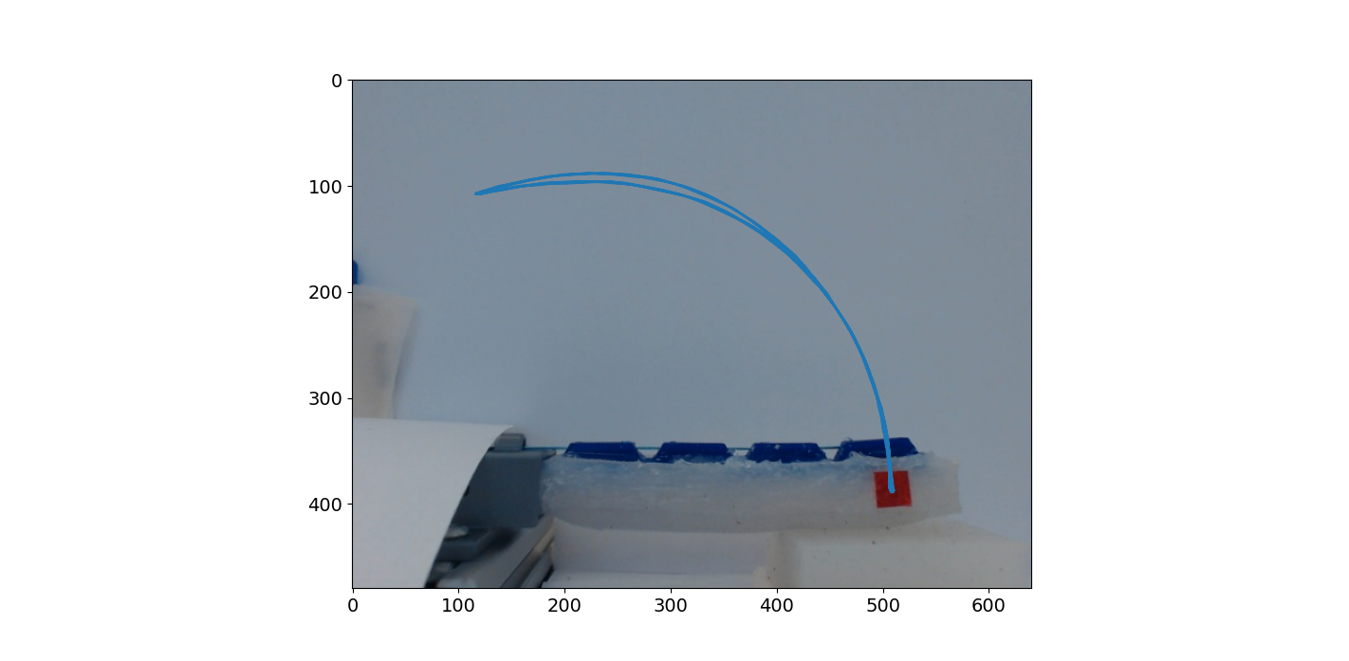
ML/finger_with_plotted_trajectory.png
