cdelor02/mres-thesis/ML/plotted_theta_values_500_samples_40Hz-2021-08-17.png

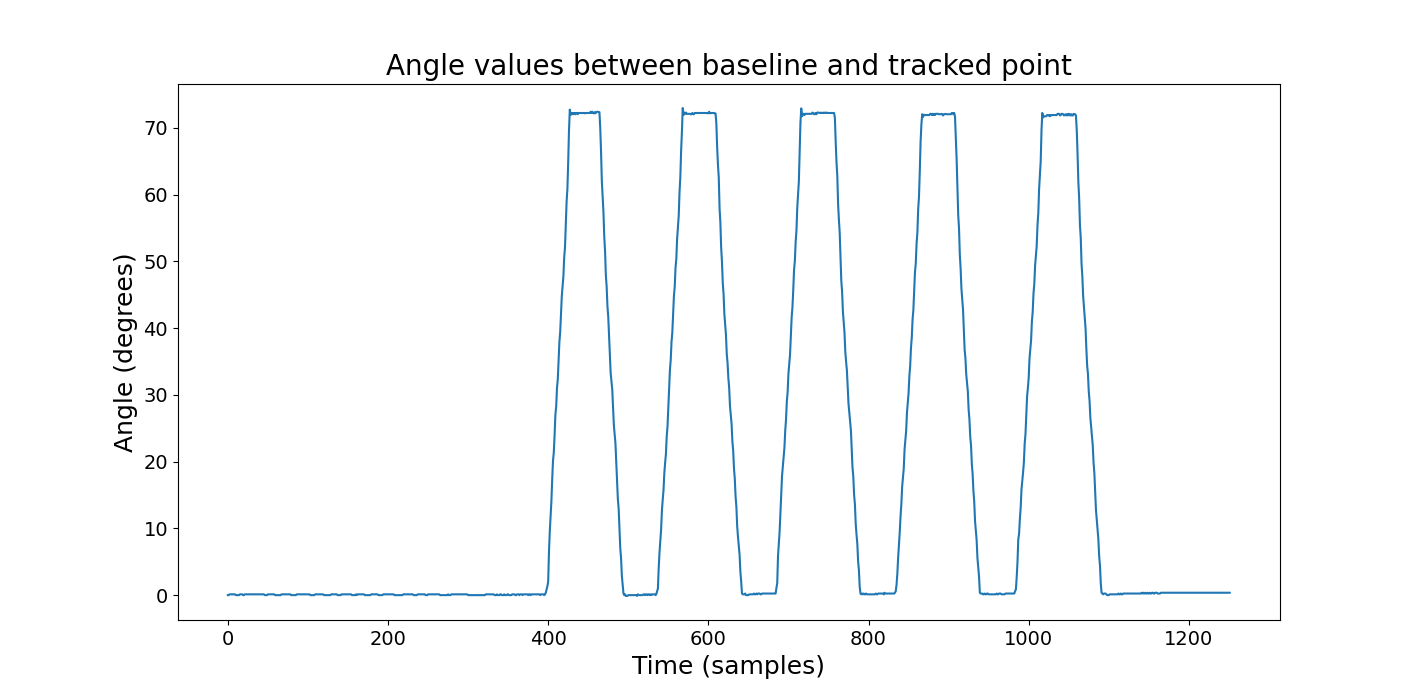
ML/plotted_theta_values_500_samples_40Hz-2021-08-17.png
