cdelor02/mres-thesis/poster/actuator_diagram.png

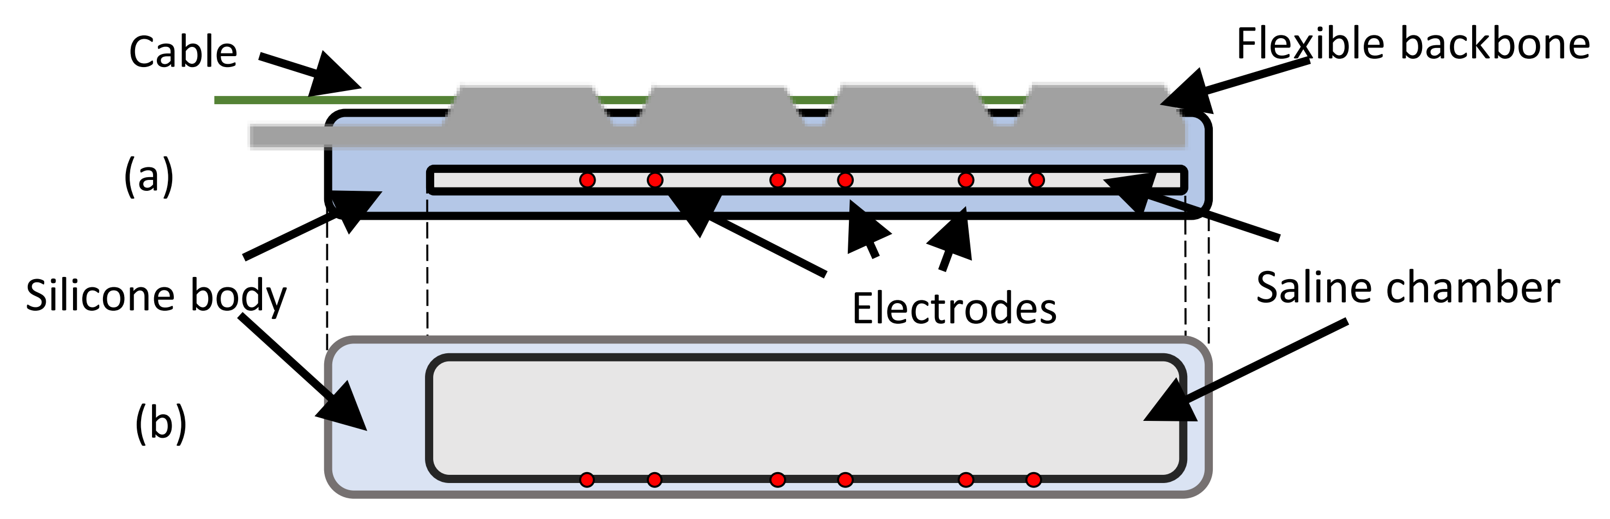
poster/actuator_diagram.png
