cdelor02/mres-thesis/poster/actuator_diagram_w_description.png

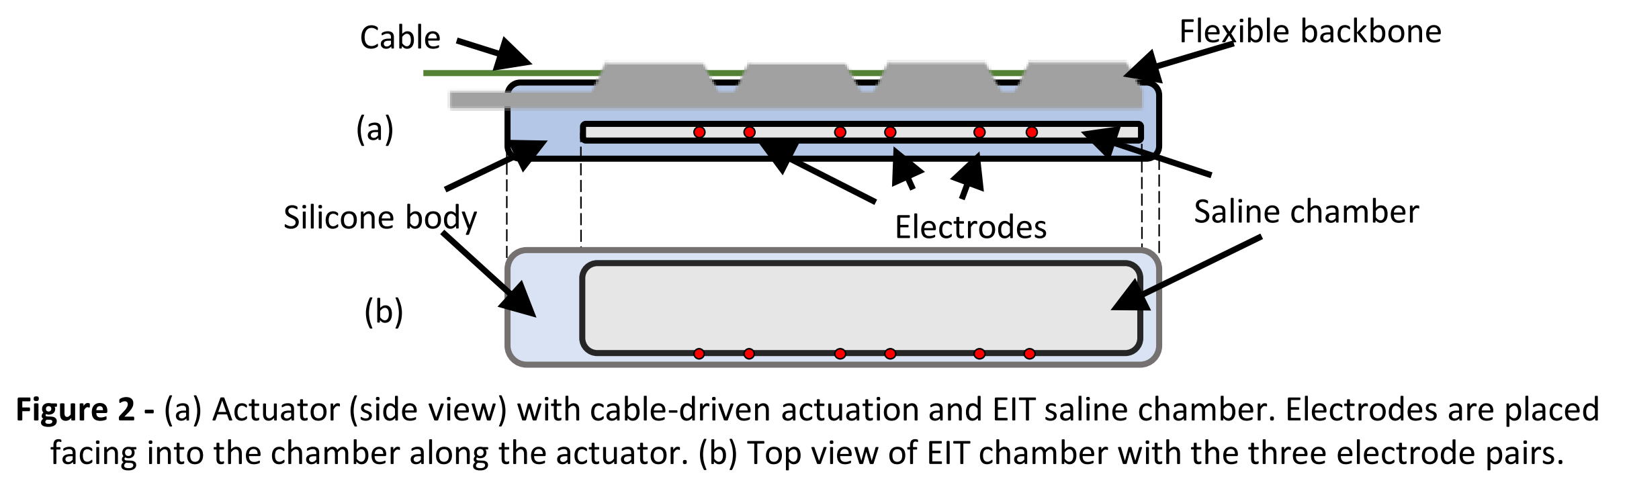
poster/actuator_diagram_w_description.png
