cdelor02/mres-thesis/poster/gripper_concept_improved.png

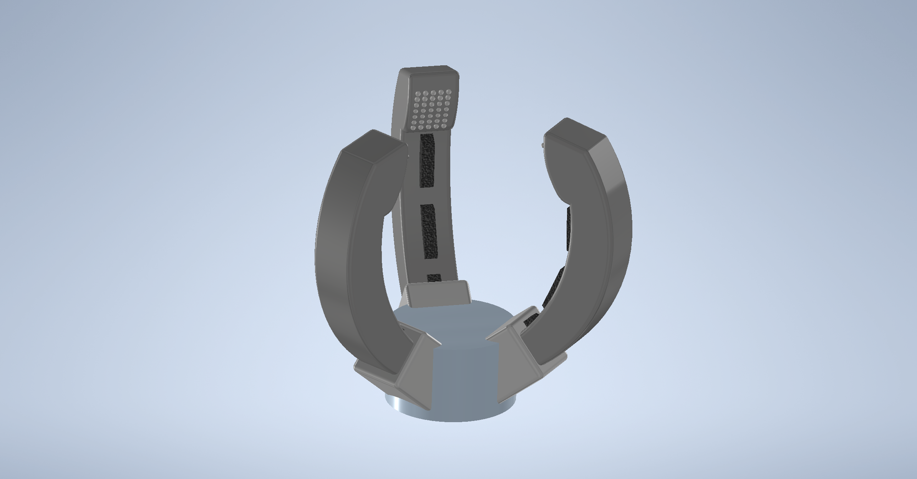
poster/gripper_concept_improved.png
