cdelor02/mres-thesis/poster/gripper_concept_improved_better_render_quality.png

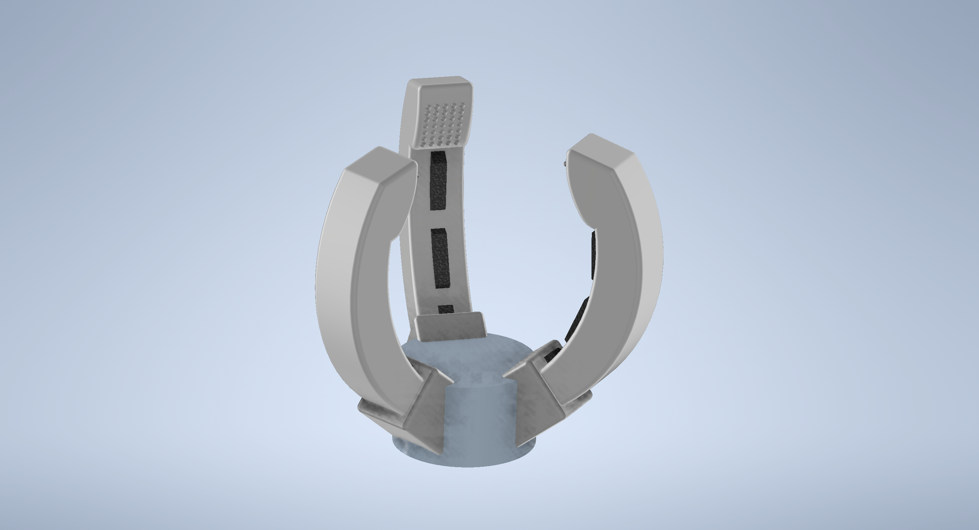
poster/gripper_concept_improved_better_render_quality.png
