cdelor02/mres-thesis/poster/soft_vs_rigid_robot_example.png

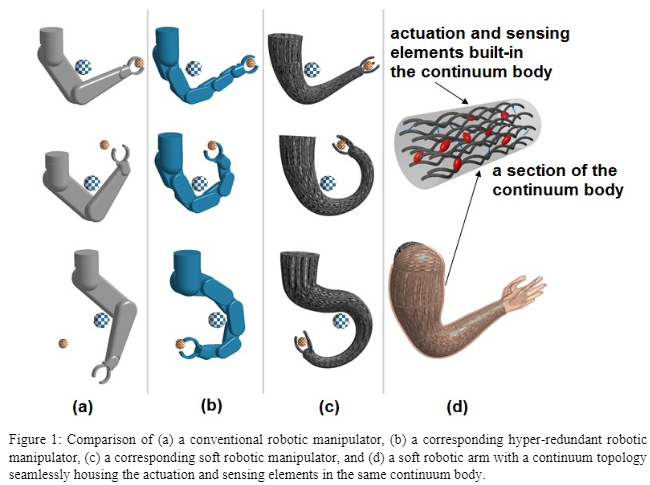
poster/soft_vs_rigid_robot_example.png
