cdelor02/mres-thesis/simulation/final_eit_chamber_injection_sim.png

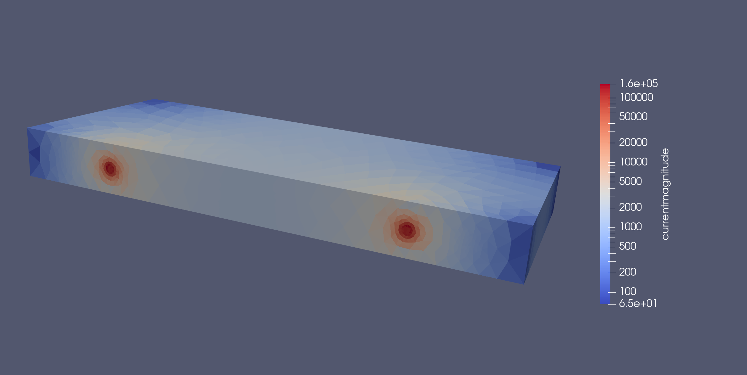
simulation/final_eit_chamber_injection_sim.png
