cdelor02/mres-thesis/SDM_actuator/actuator_backbone_fixings_for_measurements.stl

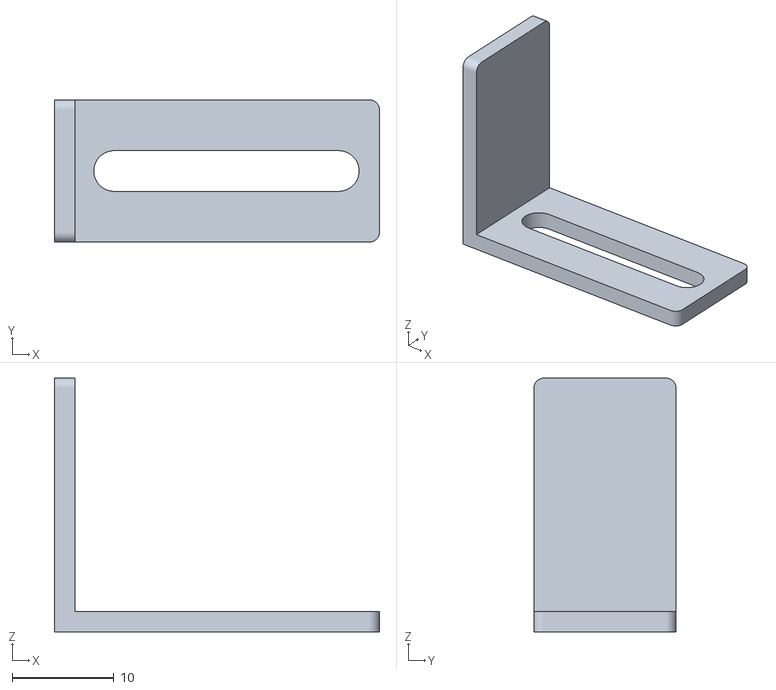
[picture p166: CAD file, 2021-09-18]
SDM_actuator/actuator_backbone_fixings_for_measurements.stl
32.0 x 14.0 x 25.0
