cdelor02/mres-thesis/SDM_actuator/probe_gimbal/improved_gimbal_ringed_rings_just_inner.stl

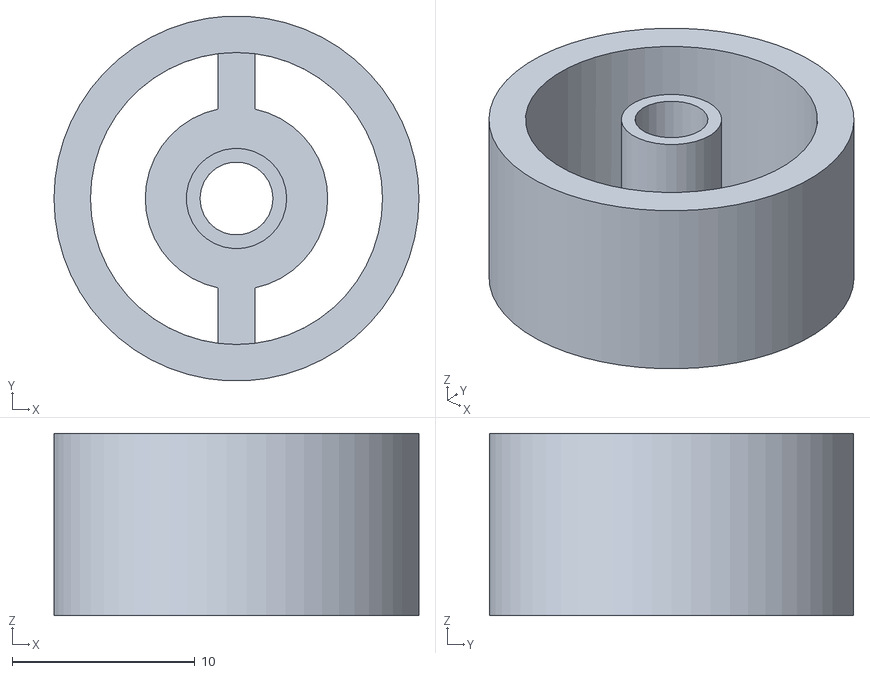
[picture p167: CAD file, 2021-06-29]
SDM_actuator/probe_gimbal/improved_gimbal_ringed_rings_just_inner.stl
20.0 x 20.0 x 10.0
