cdelor02/mres-thesis/simulation/pneunet_approximate_test_second_bend.STEP

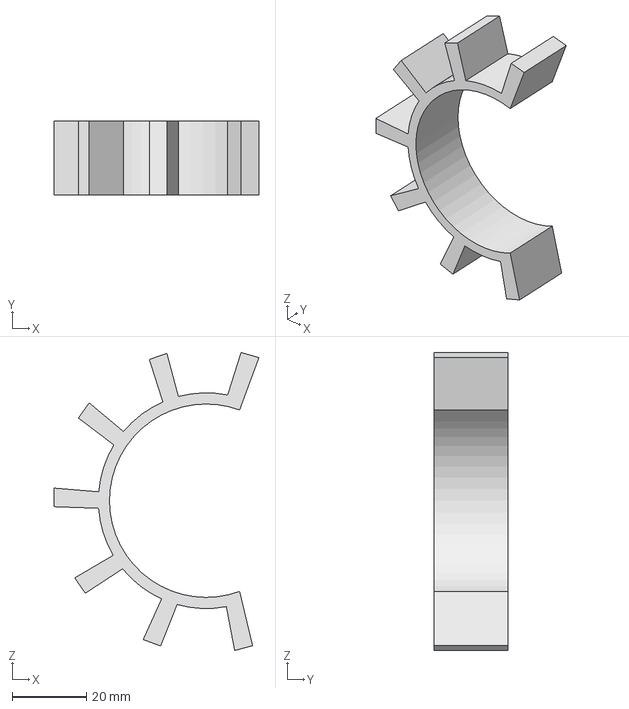
[picture p168: CAD file, 2021-03-29]
simulation/pneunet_approximate_test_second_bend.STEP
55.1 x 20.0 x 80.1 mm
