cdelor02/mres-thesis/single_chamber_test/3D_print_single_chamber.stl

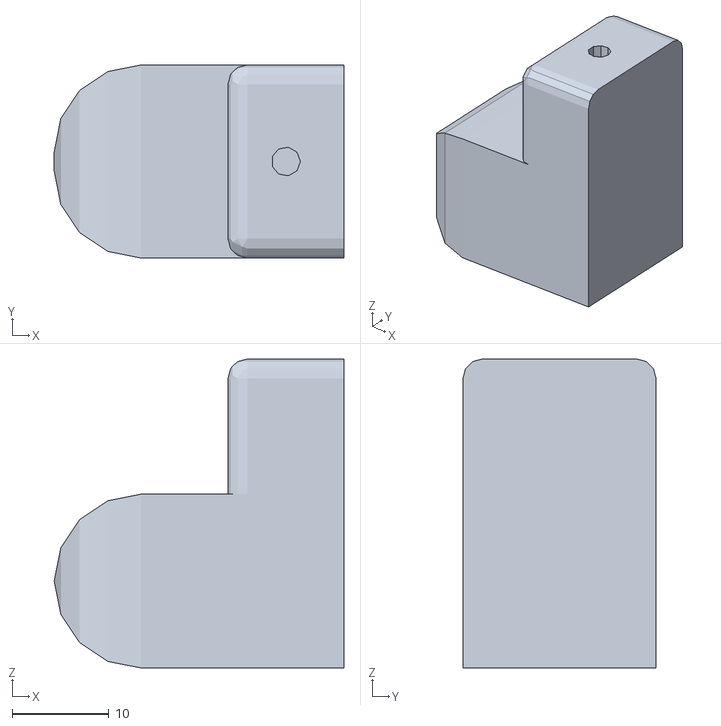
[picture p169: CAD file, 2021-04-22]
single_chamber_test/3D_print_single_chamber.stl
30.0 x 20.0 x 32.0
