cdelor02/mres-thesis/3d_printed_actuator/3D_print_actuator_parallel_eit_chamber.stl

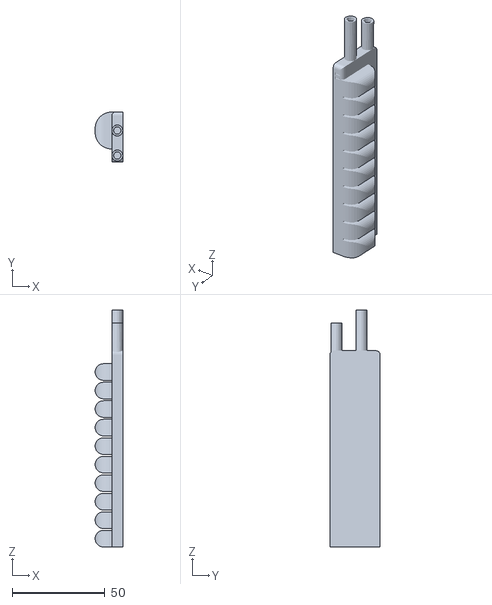
[picture p170: CAD file, 2021-05-18]
3d_printed_actuator/3D_print_actuator_parallel_eit_chamber.stl
15.0 x 27.0 x 128.0
