cdelor02/mres-thesis/SDM_actuator/probe_gimbal/improved_gimbal_ringed_rings.stl

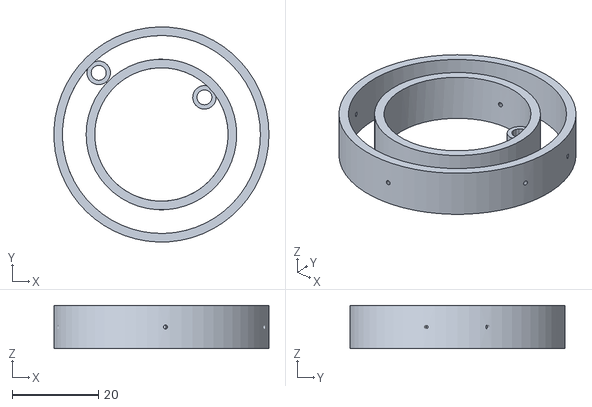
[picture p172: CAD file, 2021-06-29]
SDM_actuator/probe_gimbal/improved_gimbal_ringed_rings.stl
50.0 x 50.0 x 10.0
