cdelor02/mres-thesis/simulation/pneunet_approximate_test_first_bend.STEP

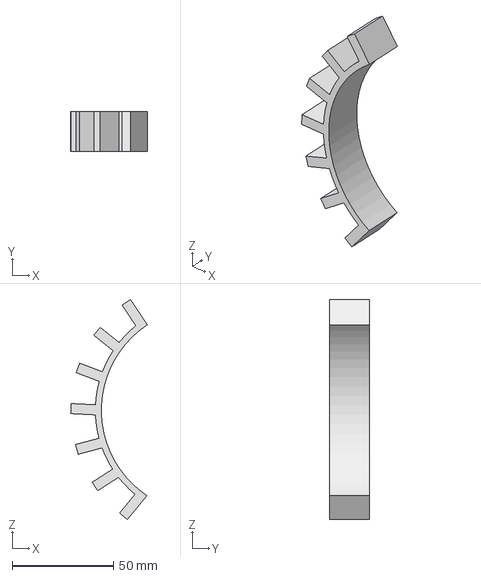
[picture p173: CAD file, 2021-03-26]
simulation/pneunet_approximate_test_first_bend.STEP
37.9 x 20.0 x 108.8 mm
