cdelor02/mres-thesis/single_chamber_test/single_chamber_inner_mould.stl

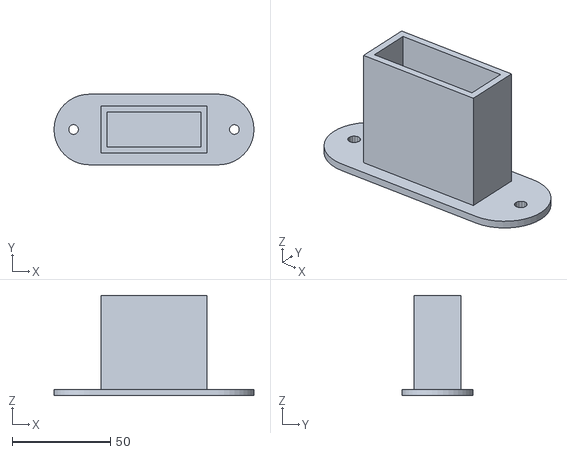
[picture p174: CAD file, 2021-04-14]
single_chamber_test/single_chamber_inner_mould.stl
102.0 x 36.0 x 51.0
