cdelor02/mres-thesis/3d_printed_actuator/3d_print_actuator_mount_2_chamber.stl

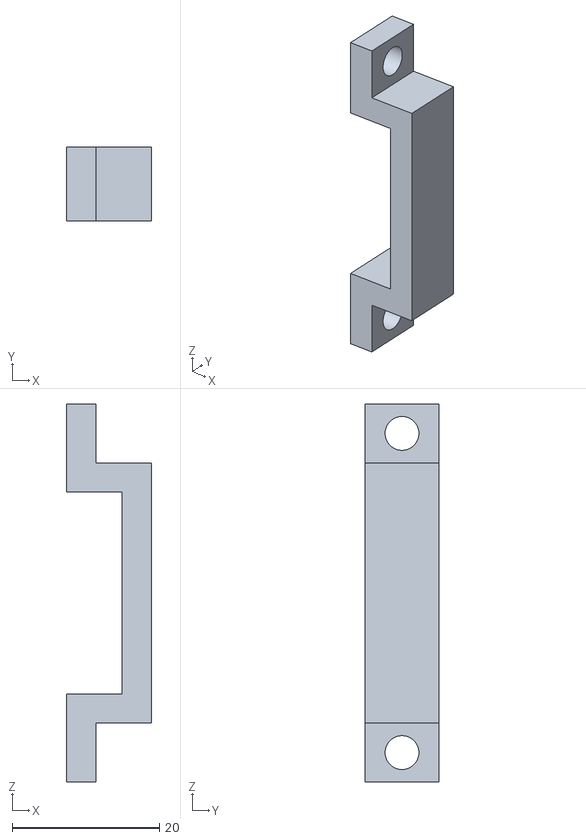
[picture p175: CAD file, 2021-05-18]
3d_printed_actuator/3d_print_actuator_mount_2_chamber.stl
11.5 x 10.0 x 51.4
