cdelor02/mres-thesis/SDM_actuator/SDM_actuator_mount.stl

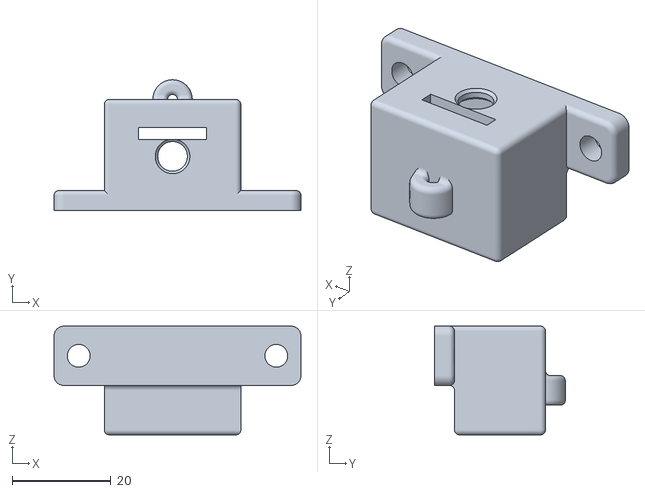
[picture p176: CAD file, 2021-08-25]
SDM_actuator/SDM_actuator_mount.stl
50.0 x 26.4 x 22.0
