cdelor02/mres-thesis/simulation/pneunet_approximate_test.STEP

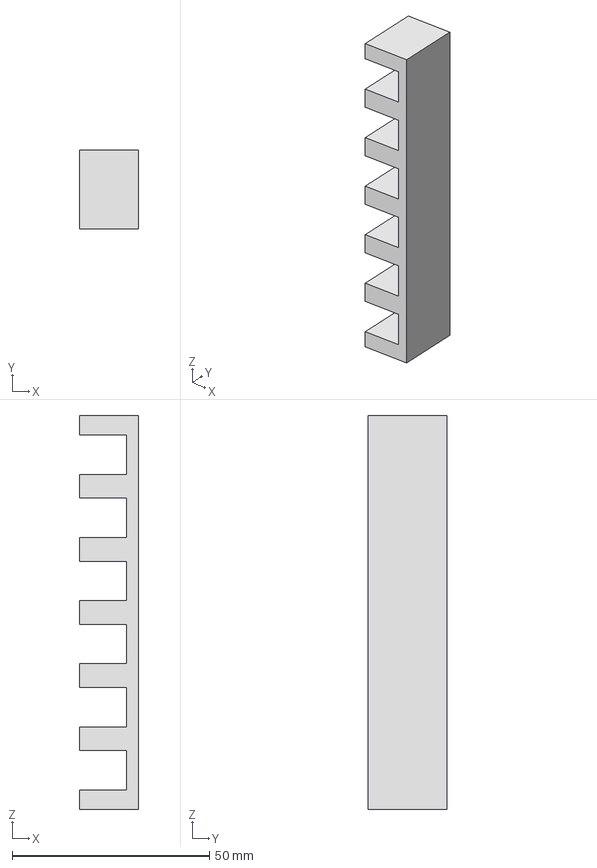
[picture p177: CAD file, 2021-03-25]
simulation/pneunet_approximate_test.STEP
15.0 x 20.0 x 100.0 mm
