cdelor02/mres-thesis/single_chamber_test/single_chamber_outer_mould.stl

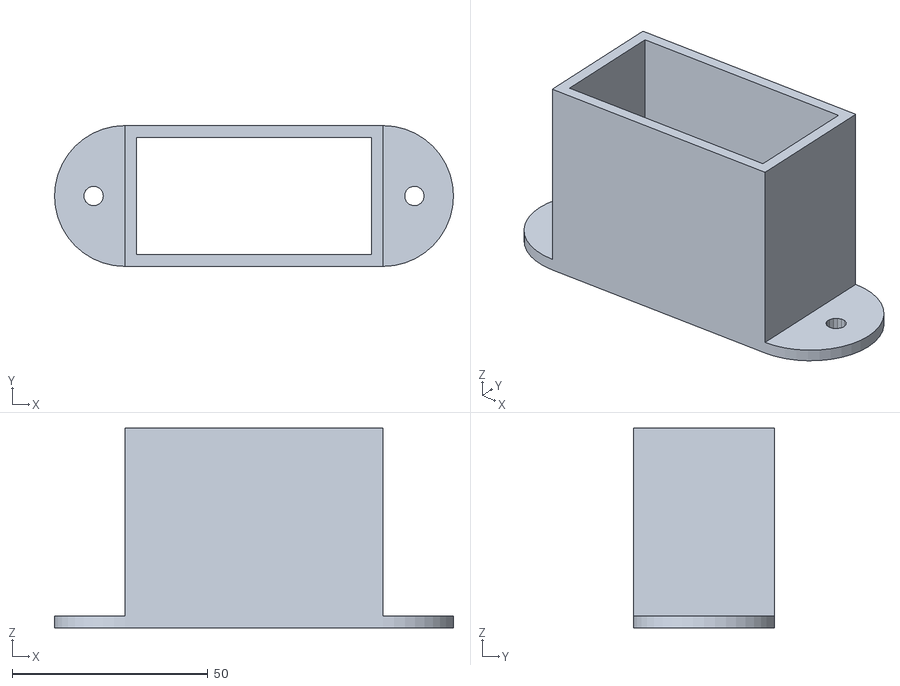
[picture p178: CAD file, 2021-04-14]
single_chamber_test/single_chamber_outer_mould.stl
102.0 x 36.0 x 51.0
