cdelor02/mres-thesis/3d_printed_actuator/linear_actuator.stl

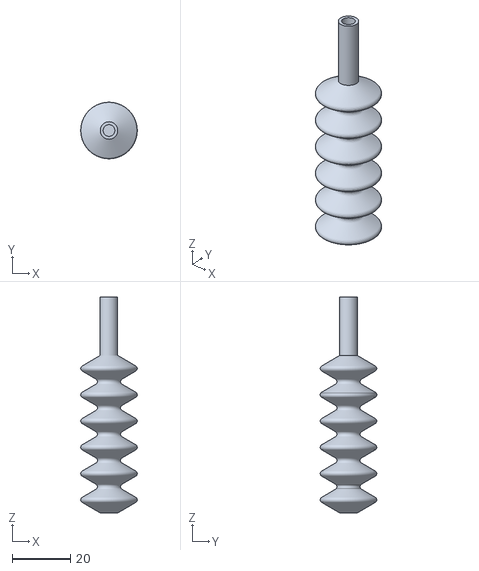
[picture p179: CAD file, 2021-05-18]
3d_printed_actuator/linear_actuator.stl
19.4 x 19.4 x 74.0
