cdelor02/mres-thesis/SDM_actuator/probe_gimbal/improved_gimbal.stl

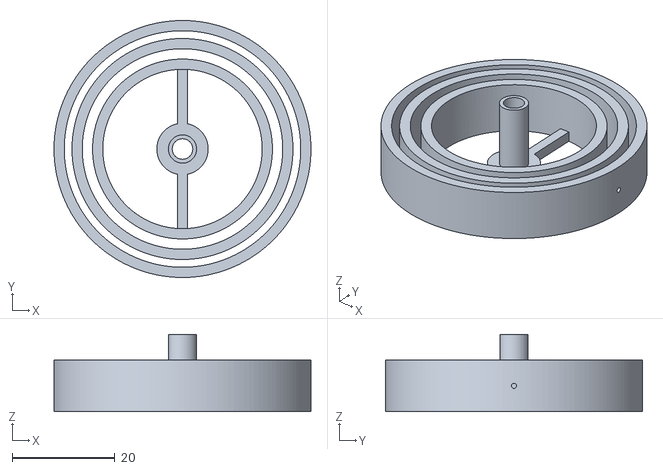
[picture p180: CAD file, 2021-06-29]
SDM_actuator/probe_gimbal/improved_gimbal.stl
50.0 x 50.0 x 15.0
