cdelor02/mres-thesis/SDM_actuator/sdm_finger_marker_jig.stl

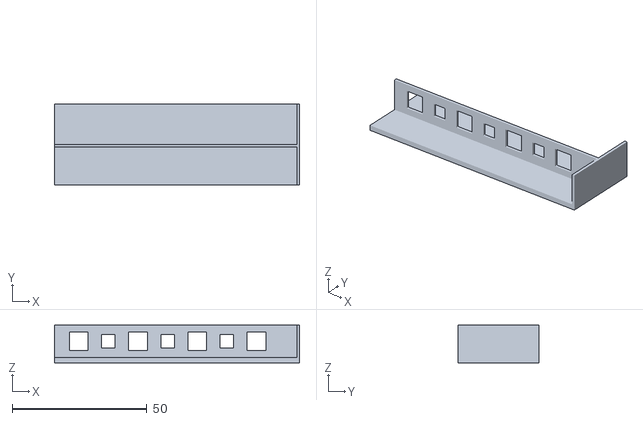
[picture p181: CAD file, 2021-08-17]
SDM_actuator/sdm_finger_marker_jig.stl
91.0 x 30.0 x 14.0
