cdelor02/mres-thesis/simulation/finger_two_bend_hollow.STEP

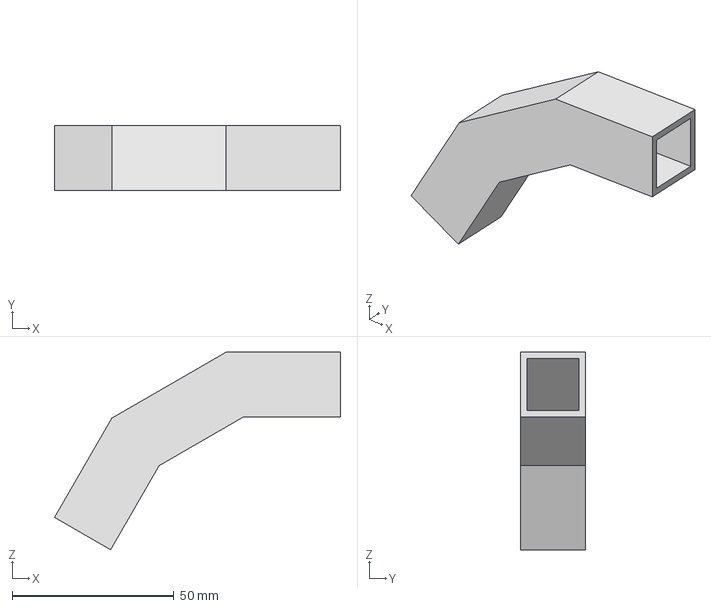
[picture p182: CAD file, 2021-03-20]
simulation/finger_two_bend_hollow.STEP
88.3 x 20.0 x 61.0 mm
