cdelor02/mres-thesis/SDM_actuator/sdm_finger_eit_chamber_mould_horizontal_e_holes.stl

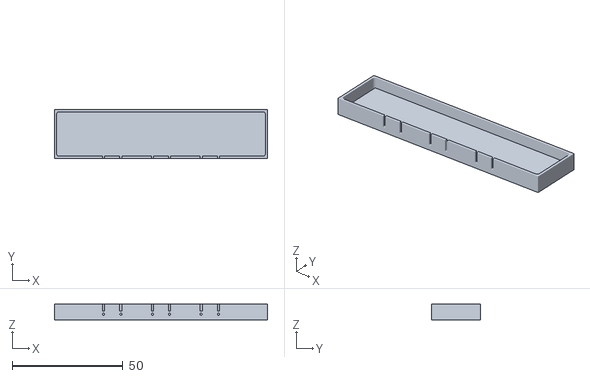
[picture p183: CAD file, 2021-08-17]
SDM_actuator/sdm_finger_eit_chamber_mould_horizontal_e_holes.stl
96.0 x 22.0 x 7.00
