cdelor02/mres-thesis/simulation/finger_one_bend_hollow.STEP

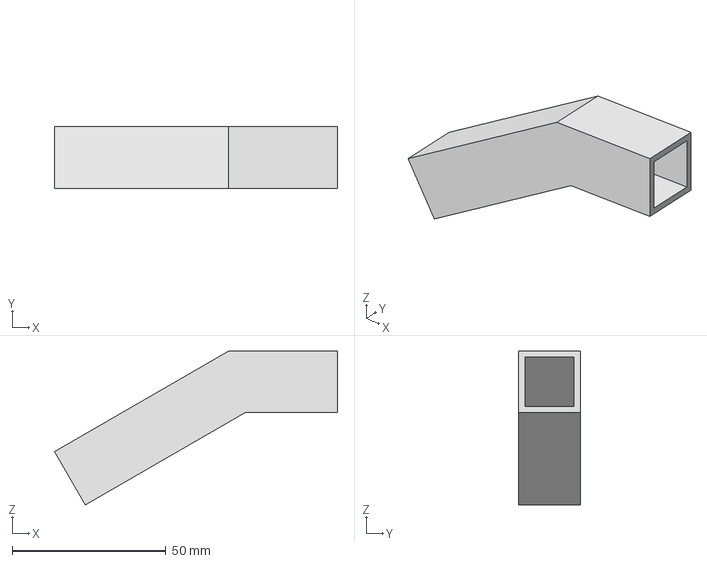
[picture p184: CAD file, 2021-03-16]
simulation/finger_one_bend_hollow.STEP
92.0 x 20.0 x 50.0 mm
