cdelor02/mres-thesis/3d_printed_actuator/eit_chamber_electrode_side.stl

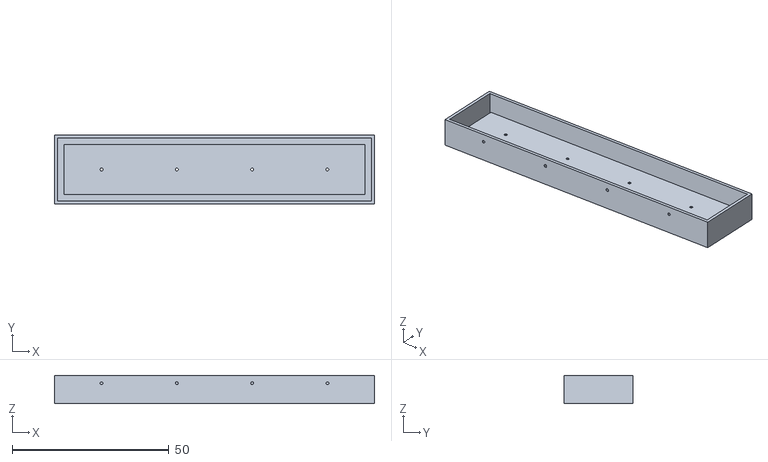
[picture p185: CAD file, 2021-05-18]
3d_printed_actuator/eit_chamber_electrode_side.stl
102.0 x 22.0 x 9.00
