cdelor02/mres-thesis/SDM_actuator/actuator_bone_joint_1.5mm_thick_no_cylinder_spine.stl

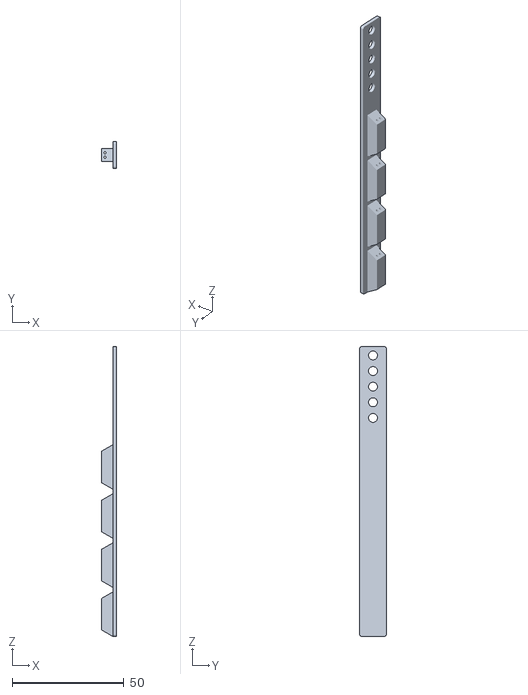
[picture p186: CAD file, 2021-08-17]
SDM_actuator/actuator_bone_joint_1.5mm_thick_no_cylinder_spine.stl
6.50 x 12.0 x 130.0
