cdelor02/mres-thesis/simulation/finger_straight_hollow.STEP

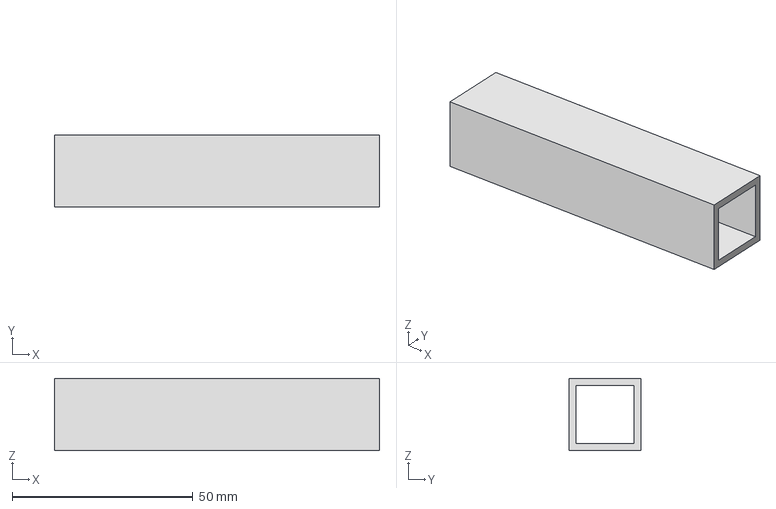
[picture p187: CAD file, 2021-03-16]
simulation/finger_straight_hollow.STEP
90.0 x 20.0 x 20.0 mm
