cdelor02/mres-thesis/simulation/finger_two_bend.STEP

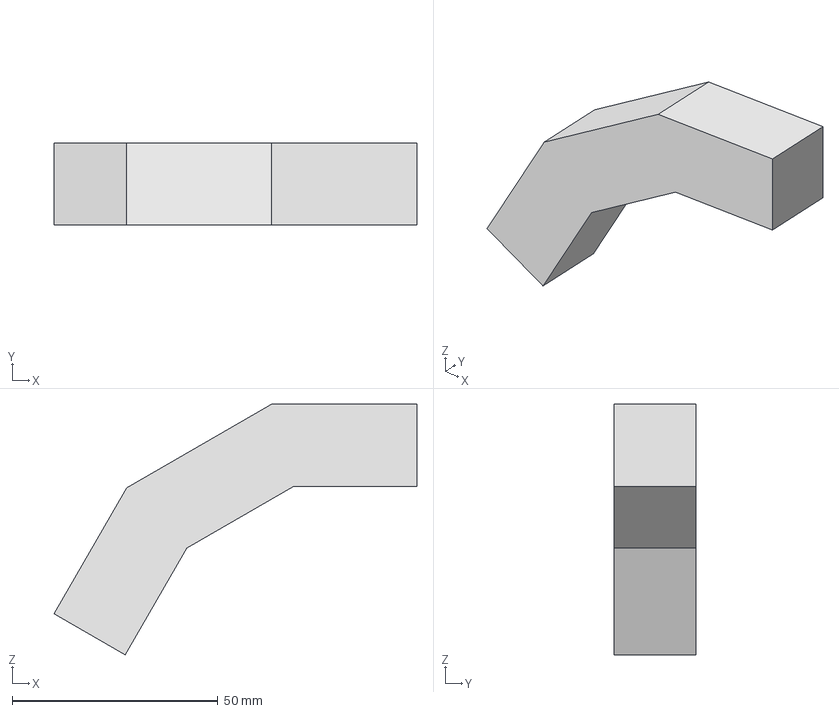
[picture p189: CAD file, 2021-03-11]
simulation/finger_two_bend.STEP
88.3 x 20.0 x 61.0 mm
