cdelor02/mres-thesis/3d_printed_actuator/actuator_tube.stl

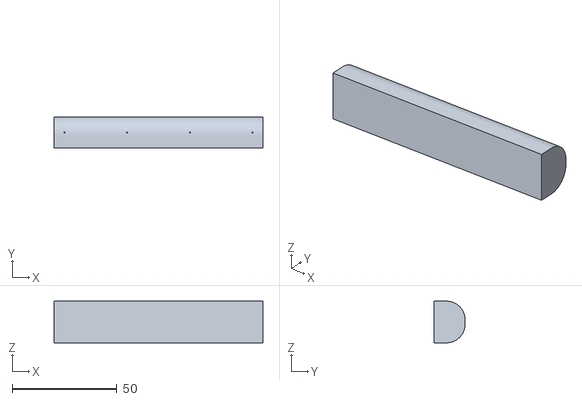
[picture p190: CAD file, 2021-05-05]
3d_printed_actuator/actuator_tube.stl
100.0 x 15.0 x 20.0
