cdelor02/mres-thesis/SDM_actuator/sdm_finger_bone_attachment_mould_v2.stl

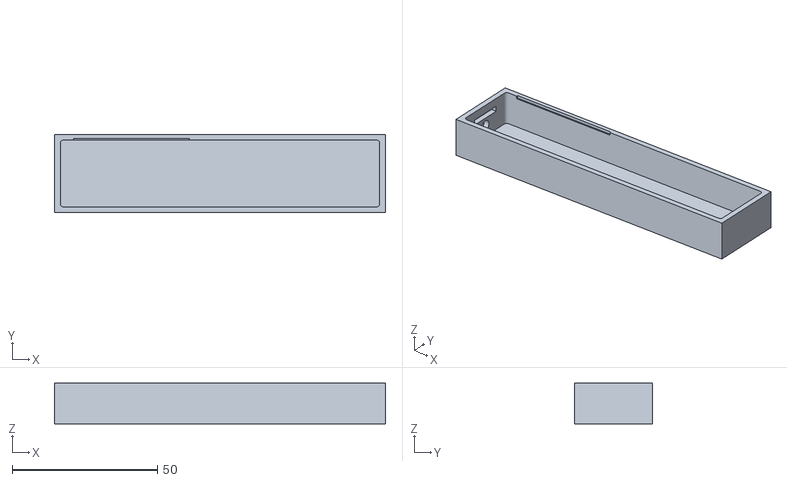
[picture p191: CAD file, 2021-08-17]
SDM_actuator/sdm_finger_bone_attachment_mould_v2.stl
114.0 x 27.0 x 14.0
