cdelor02/mres-thesis/3d_printed_actuator/actuator_tube_test.stl

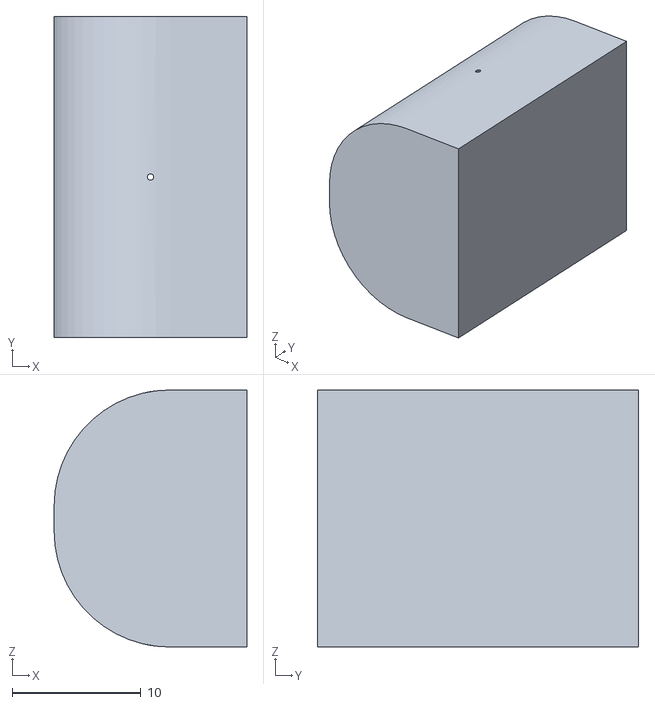
[picture p192: CAD file, 2021-05-05]
3d_printed_actuator/actuator_tube_test.stl
15.0 x 25.0 x 20.0
