cdelor02/mres-thesis/SDM_actuator/actuator_bone_joint_1.5mm_thick_w_cylinder_spine.stl

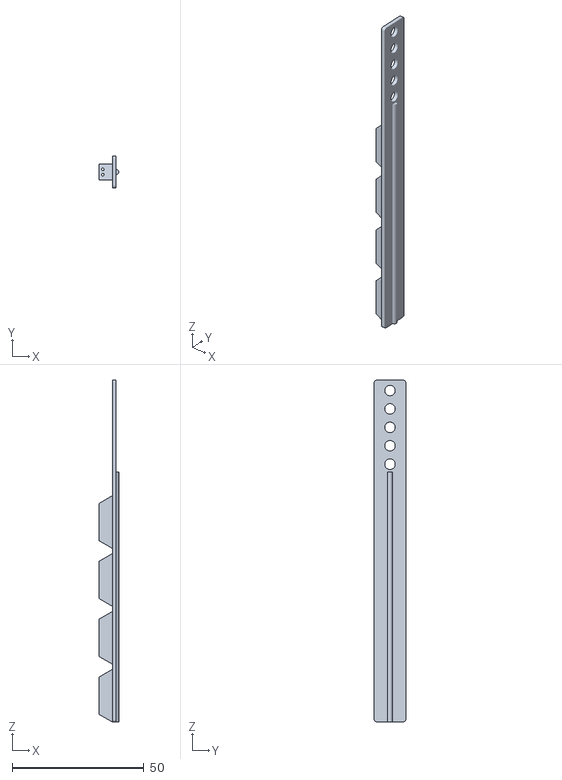
[picture p193: CAD file, 2021-08-06]
SDM_actuator/actuator_bone_joint_1.5mm_thick_w_cylinder_spine.stl
7.50 x 12.0 x 130.0
