cdelor02/mres-thesis/simulation/finger_one_bend.STEP

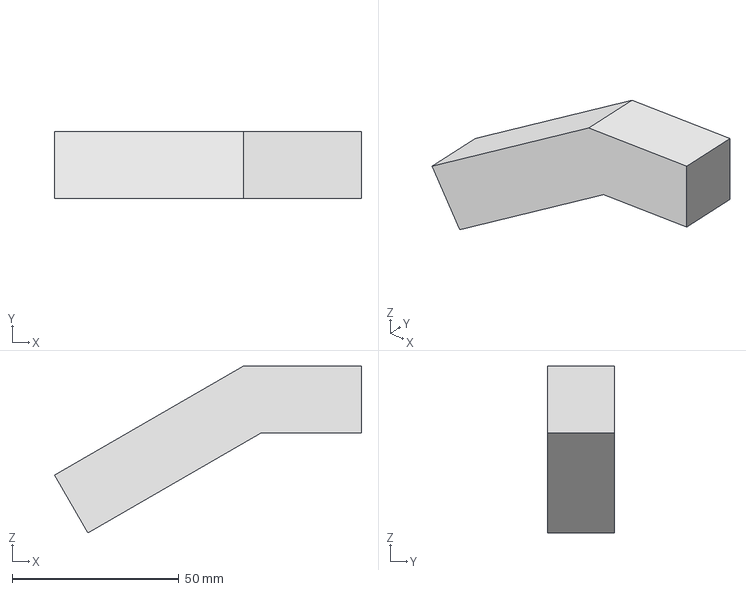
[picture p194: CAD file, 2021-03-11]
simulation/finger_one_bend.STEP
92.0 x 20.0 x 50.0 mm
