cdelor02/mres-thesis/3d_printed_actuator/3D_print_actuator_circle_arches.stl

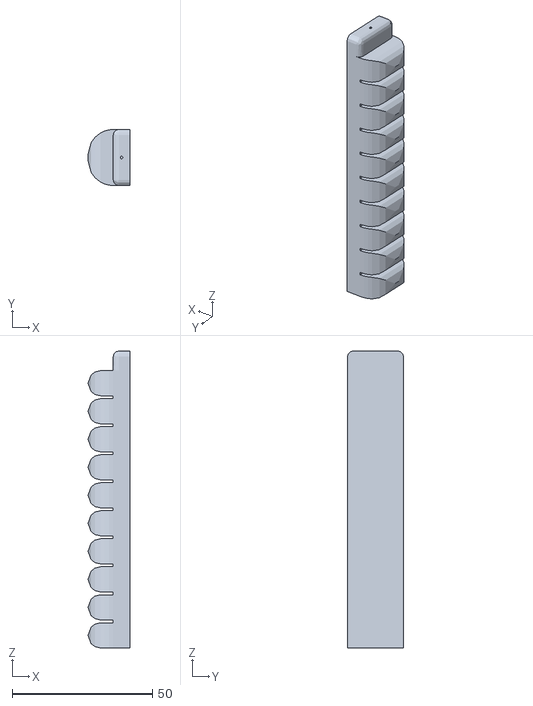
[picture p195: CAD file, 2021-05-05]
3d_printed_actuator/3D_print_actuator_circle_arches.stl
15.0 x 20.0 x 106.0
