cdelor02/mres-thesis/SDM_actuator/syringe_mount.stl

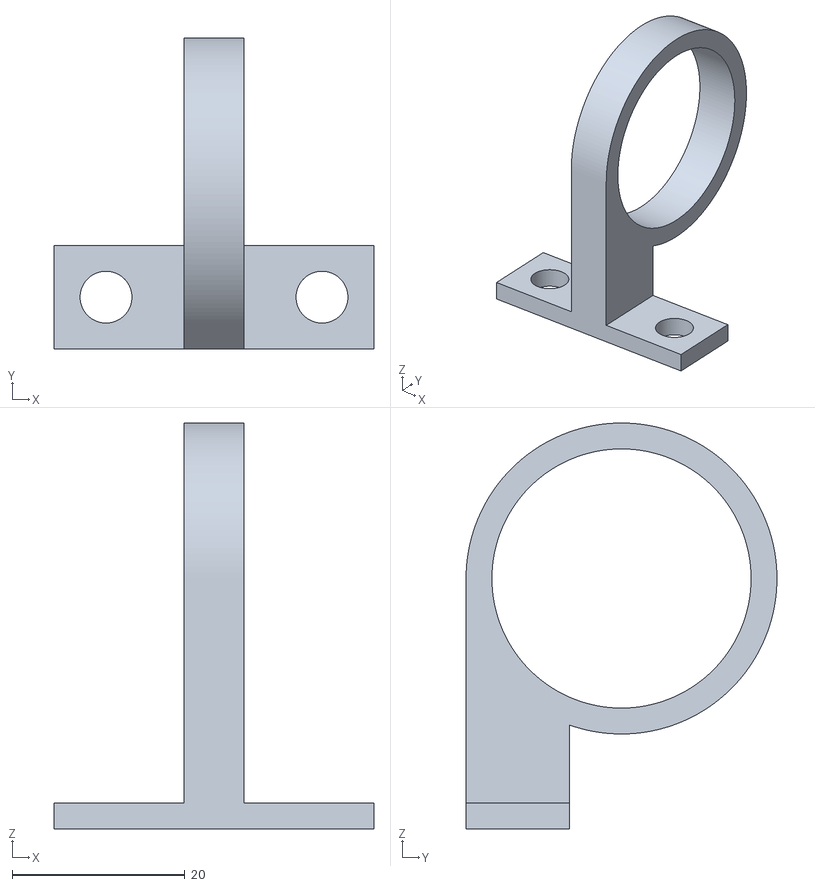
[picture p196: CAD file, 2021-07-23]
SDM_actuator/syringe_mount.stl
37.0 x 36.0 x 47.0
