cdelor02/mres-thesis/simulation/finger_chamber.STEP

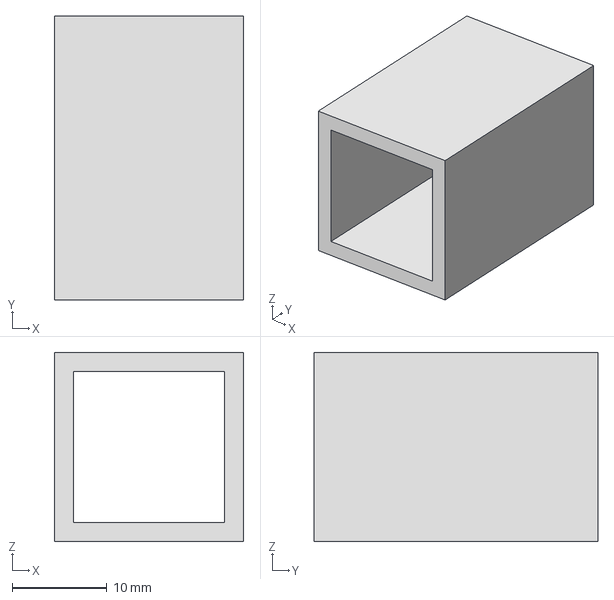
[picture p197: CAD file, 2021-03-11]
simulation/finger_chamber.STEP
20.0 x 30.0 x 20.0 mm
