cdelor02/mres-thesis/SDM_actuator/grid_board_8020_corner_mount.stl

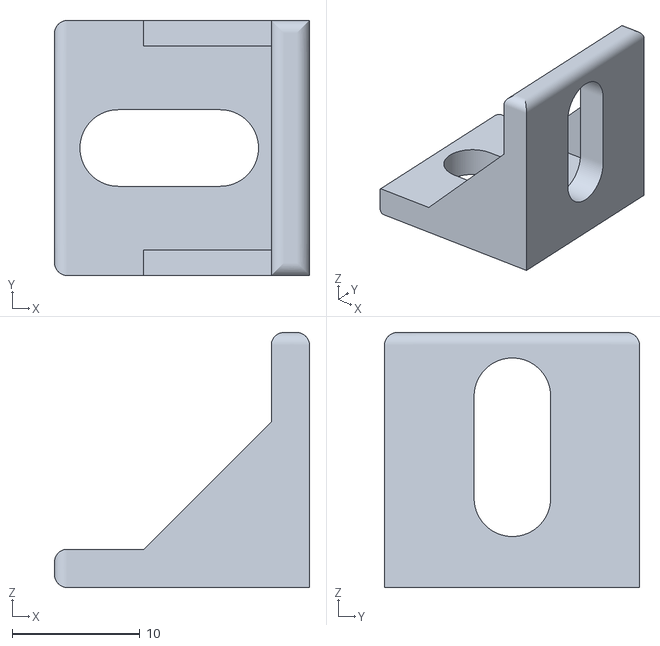
[picture p198: CAD file, 2021-07-15]
SDM_actuator/grid_board_8020_corner_mount.stl
20.0 x 20.0 x 20.0
