cdelor02/mres-thesis/simulation/bent_finger_model.STEP

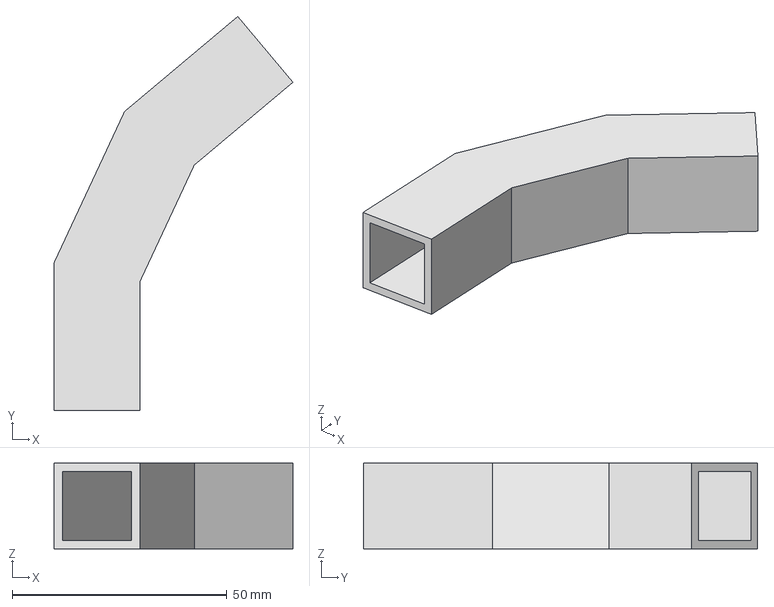
[picture p199: CAD file, 2021-03-11]
simulation/bent_finger_model.STEP
55.7 x 91.8 x 20.0 mm
