cdelor02/mres-thesis/3d_printed_actuator/3D_print_actuator_truncated.stl

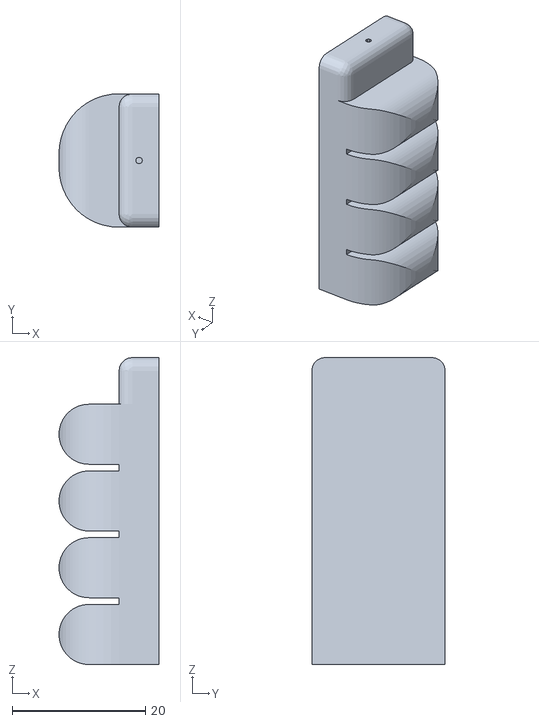
[picture p200: CAD file, 2021-04-22]
3d_printed_actuator/3D_print_actuator_truncated.stl
15.0 x 20.0 x 46.0
