cdelor02/mres-thesis/SDM_actuator/eit_electrode_board_mounting_base.stl

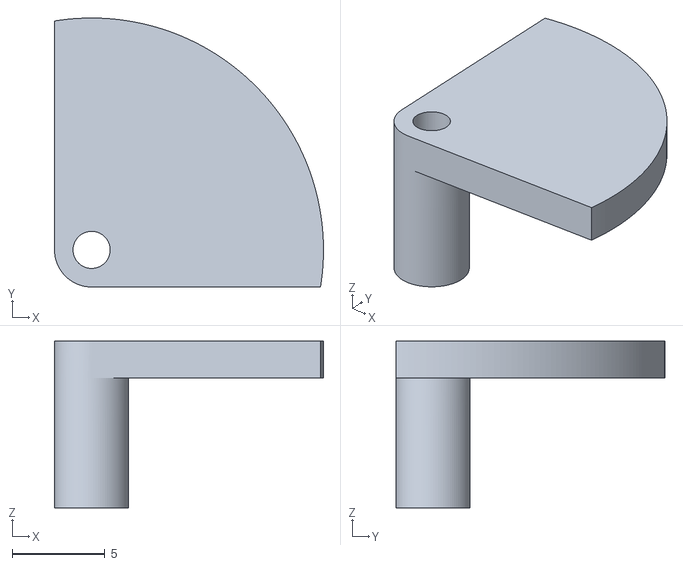
[picture p201: CAD file, 2021-07-06]
SDM_actuator/eit_electrode_board_mounting_base.stl
14.5 x 14.5 x 9.00
