cdelor02/mres-thesis/3d_printed_actuator/actuator_mount.stl

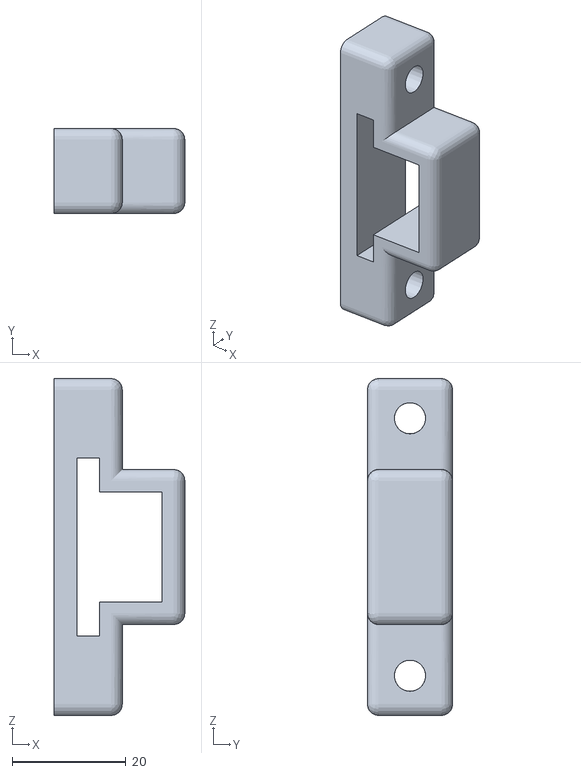
[picture p202: CAD file, 2021-04-19]
3d_printed_actuator/actuator_mount.stl
23.0 x 15.0 x 59.3
