cdelor02/mres-thesis/SDM_actuator/eit_electrode_board_mounting_simple.stl

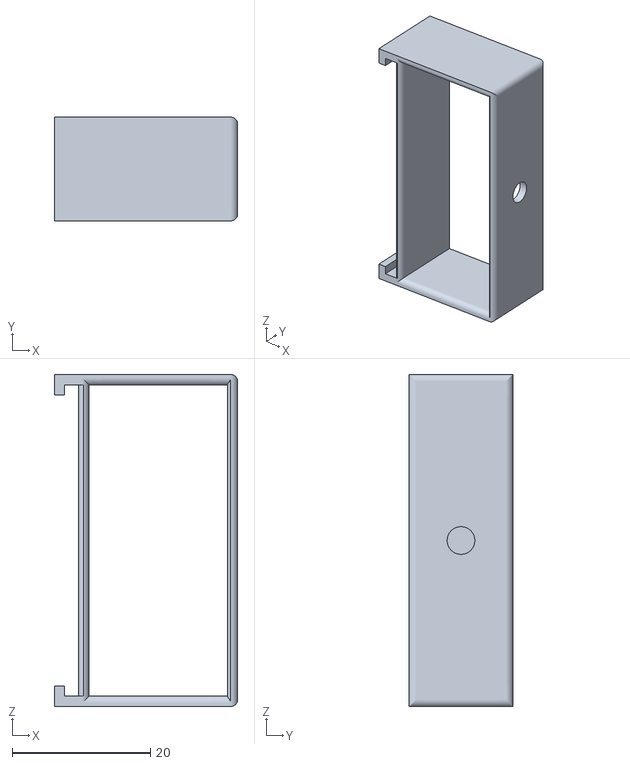
[picture p203: CAD file, 2021-07-06]
SDM_actuator/eit_electrode_board_mounting_simple.stl
26.5 x 15.0 x 48.0
