cdelor02/mres-thesis/3d_printed_actuator/3d_print_actuator_mount.stl

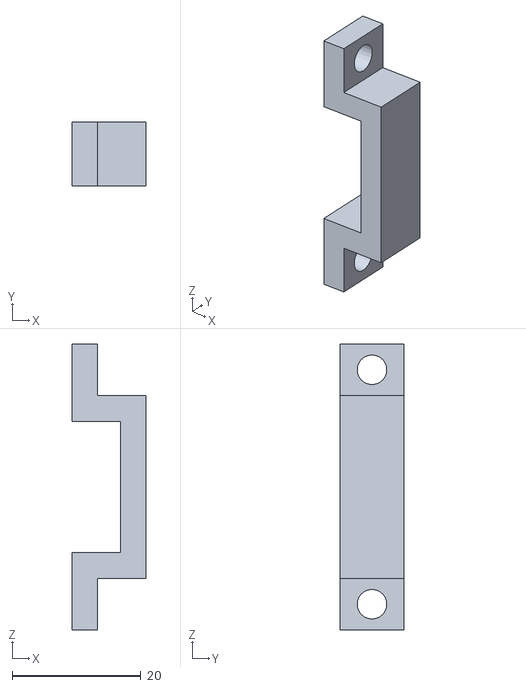
[picture p204: CAD file, 2021-04-19]
3d_printed_actuator/3d_print_actuator_mount.stl
11.5 x 10.0 x 44.4
