cdelor02/mres-thesis/SDM_actuator/eit_electrode_board_mounting_top.stl

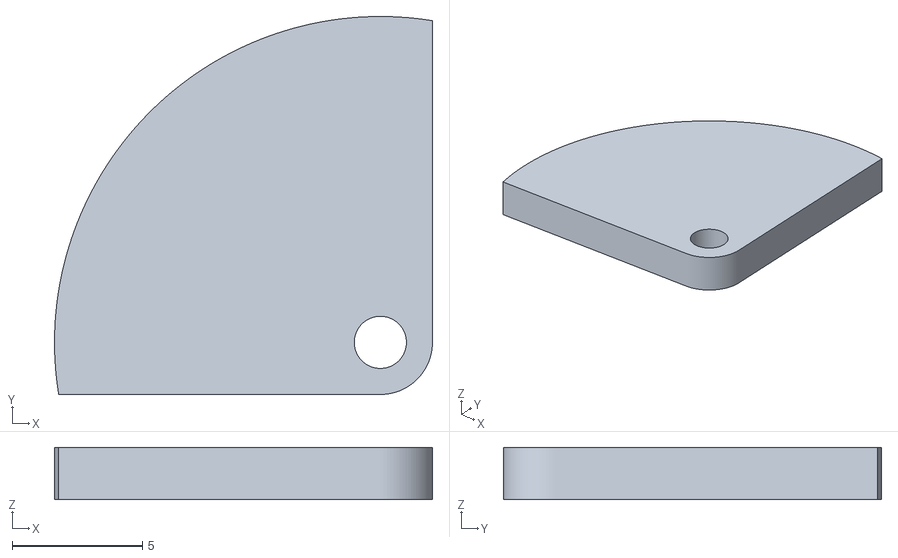
[picture p205: CAD file, 2021-07-06]
SDM_actuator/eit_electrode_board_mounting_top.stl
14.5 x 14.5 x 2.00
