cdelor02/mres-thesis/SDM_actuator/eit_electrode_board_mountings.stl

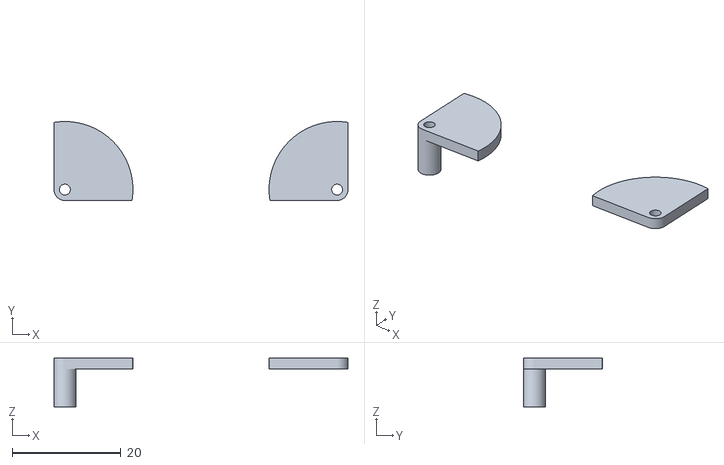
[picture p206: CAD file, 2021-07-06]
SDM_actuator/eit_electrode_board_mountings.stl
54.0 x 14.5 x 9.00
