cdelor02/mres-thesis/3d_printed_actuator/actuator_cross-section_arches.stl

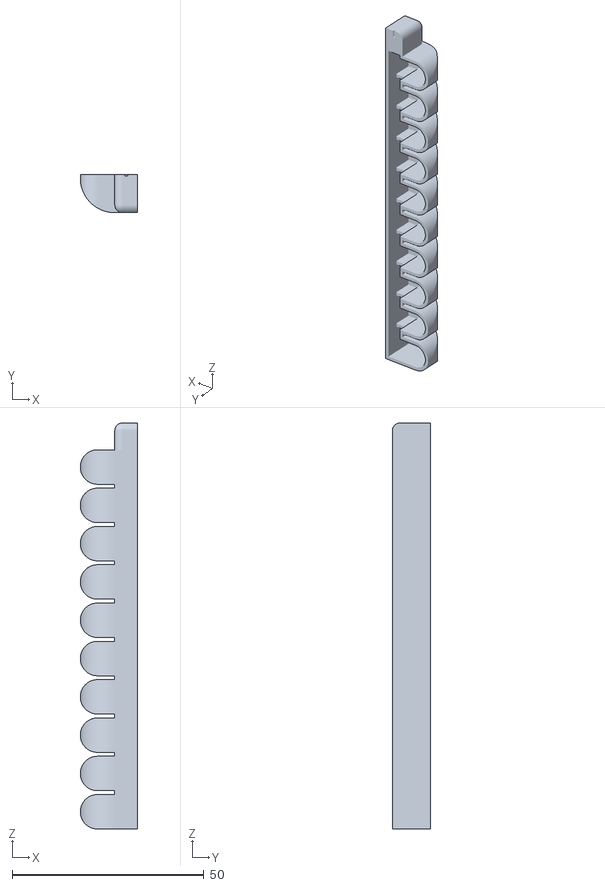
[picture p207: CAD file, 2021-04-19]
3d_printed_actuator/actuator_cross-section_arches.stl
15.0 x 10.0 x 106.0
