cdelor02/mres-thesis/SDM_actuator/stepper_mount.stl

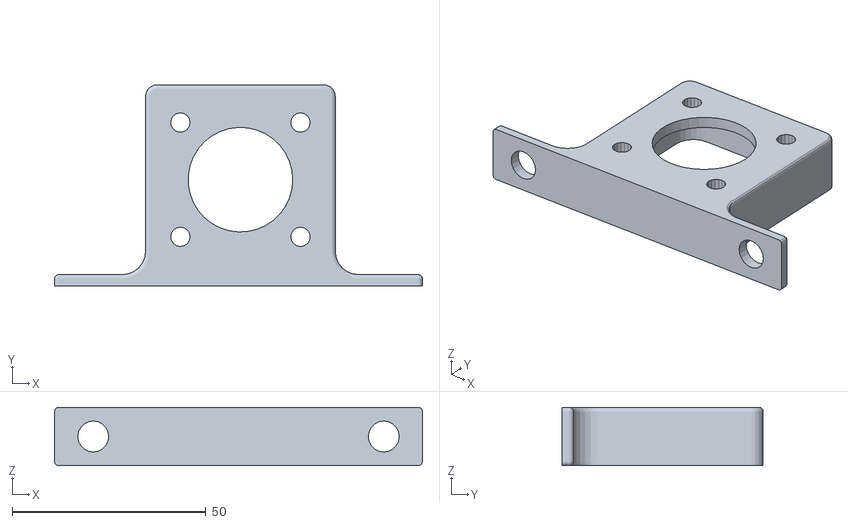
[picture p208: CAD file, 2021-06-29]
SDM_actuator/stepper_mount.stl
95.0 x 52.0 x 15.0
