cdelor02/mres-thesis/3d_printed_actuator/3D_print_actuator_cross-section.stl

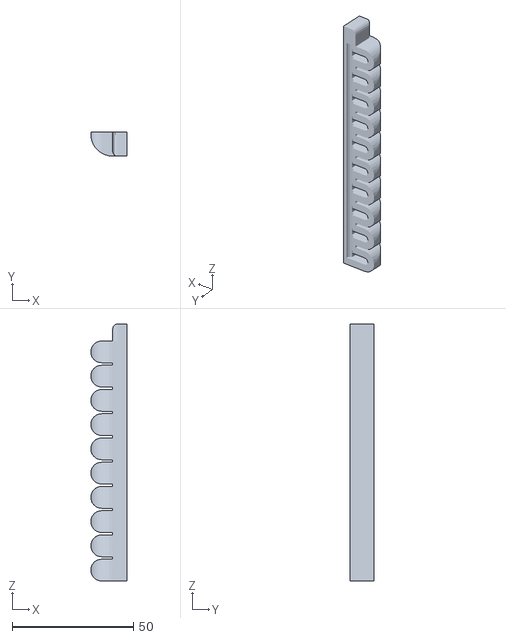
[picture p209: CAD file, 2021-04-14]
3d_printed_actuator/3D_print_actuator_cross-section.stl
15.0 x 10.0 x 106.0
