cdelor02/mres-thesis/SDM_actuator/actuator_bone_joint_thicker_w_cylinder_spine.stl

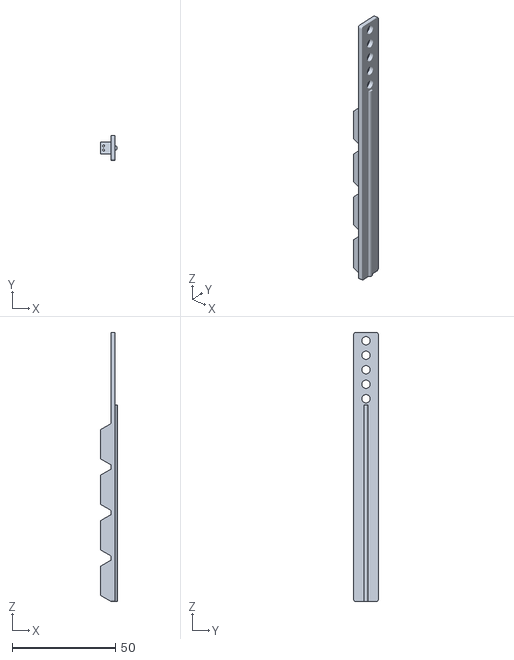
[picture p210: CAD file, 2021-06-29]
SDM_actuator/actuator_bone_joint_thicker_w_cylinder_spine.stl
8.00 x 12.0 x 130.0
