cdelor02/mres-thesis/3d_printed_actuator/3D_print_actuator.stl

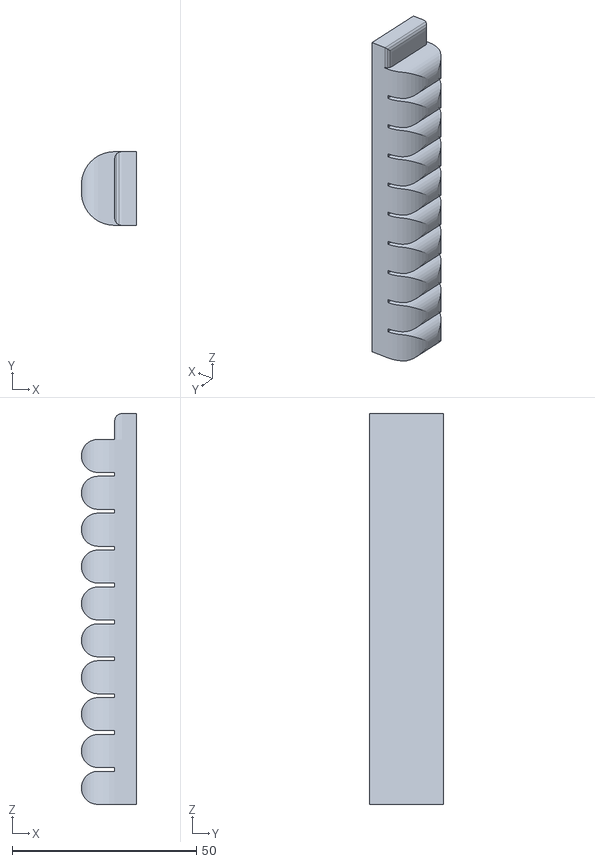
[picture p211: CAD file, 2021-04-14]
3d_printed_actuator/3D_print_actuator.stl
15.0 x 20.0 x 106.0
