cdelor02/mres-thesis/SDM_actuator/stepper_spool.stl

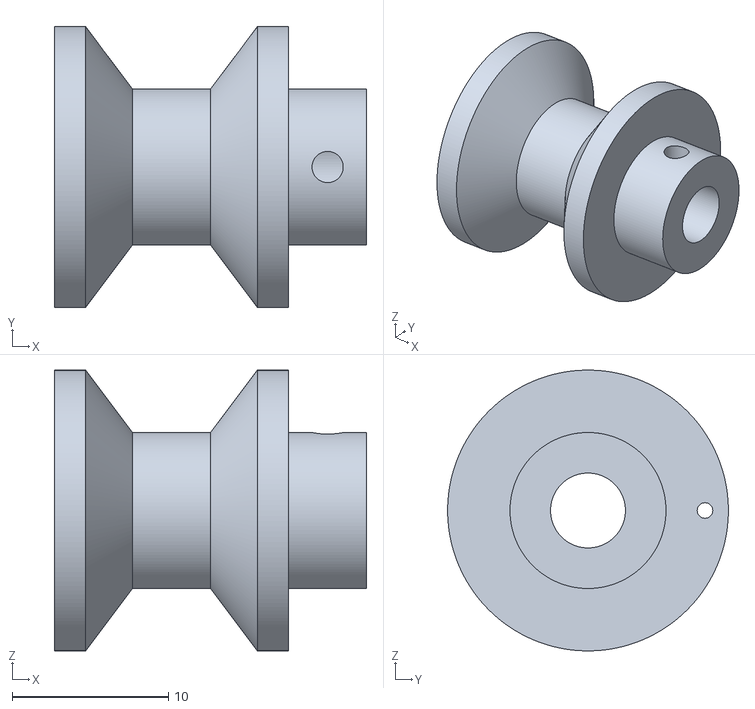
[picture p212: CAD file, 2021-06-29]
SDM_actuator/stepper_spool.stl
20.0 x 18.0 x 18.0
