cdelor02/mres-thesis/SDM_actuator/SDM_actuator_mount_bigger.stl

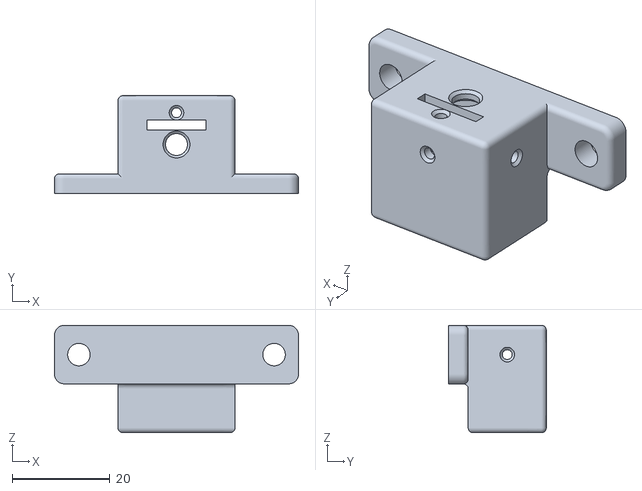
[picture p213: CAD file, 2021-06-29]
SDM_actuator/SDM_actuator_mount_bigger.stl
50.0 x 20.0 x 22.0
