cdelor02/mres-thesis/SDM_actuator/sdm_finger_eit_chamber_mould_v2.stl

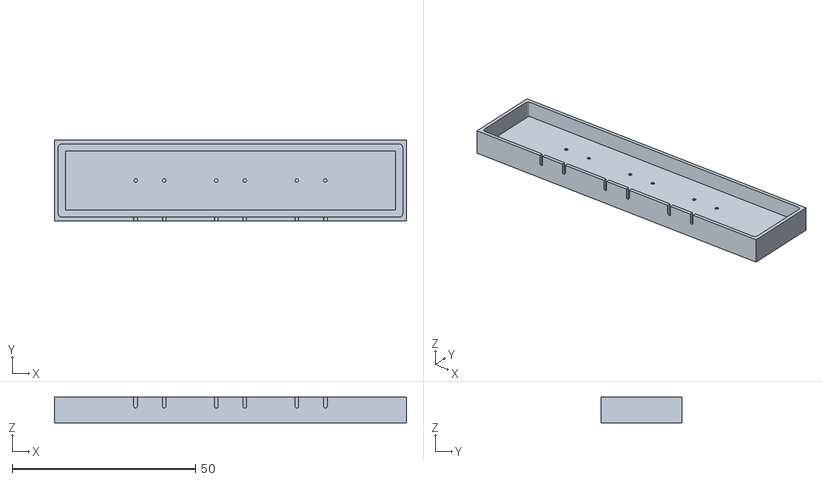
[picture p214: CAD file, 2021-06-29]
SDM_actuator/sdm_finger_eit_chamber_mould_v2.stl
96.0 x 22.0 x 7.00
