cdelor02/mres-thesis/SDM_actuator/actuator_bone_joint_cylinder_spine.stl

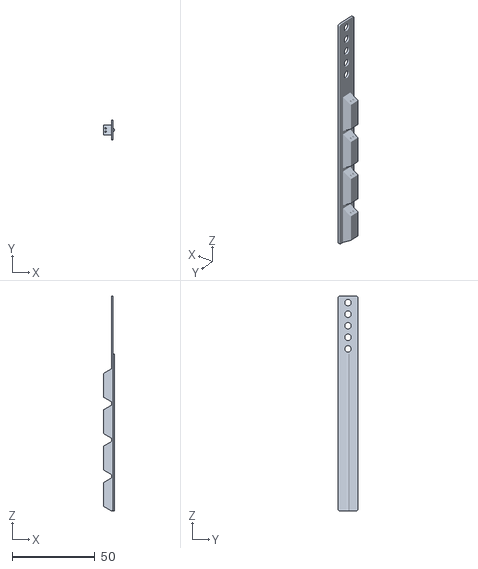
[picture p215: CAD file, 2021-06-03]
SDM_actuator/actuator_bone_joint_cylinder_spine.stl
6.95 x 12.0 x 130.0
