cdelor02/mres-thesis/SDM_actuator/actuator_bone_joint_pla_test.stl

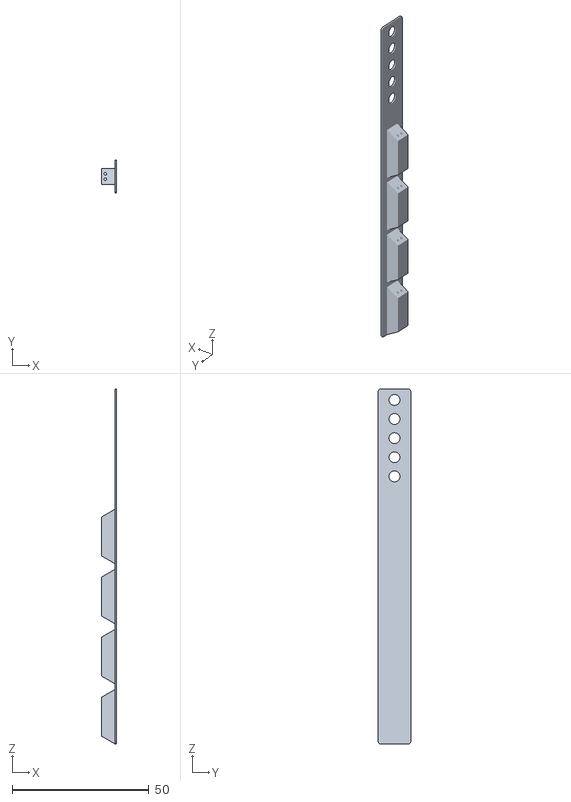
[picture p216: CAD file, 2021-06-03]
SDM_actuator/actuator_bone_joint_pla_test.stl
5.50 x 12.0 x 130.0
