cdelor02/mres-thesis/SDM_actuator/actuator_bone_joint.stl

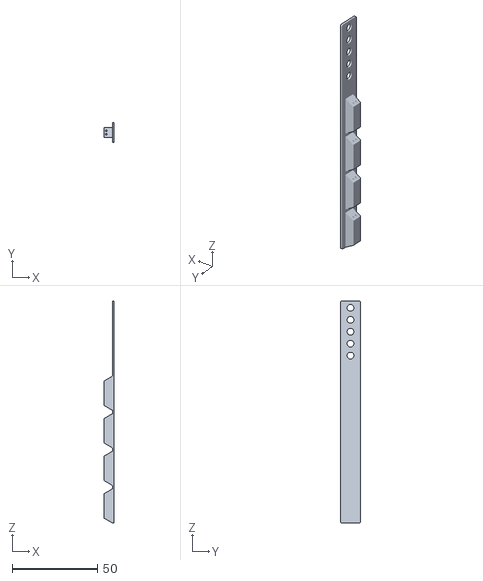
[picture p217: CAD file, 2021-05-28]
SDM_actuator/actuator_bone_joint.stl
6.00 x 12.0 x 130.0
