cdelor02/mres-thesis/computer_vision/wiredfingersetup.jpg_1220.jpg

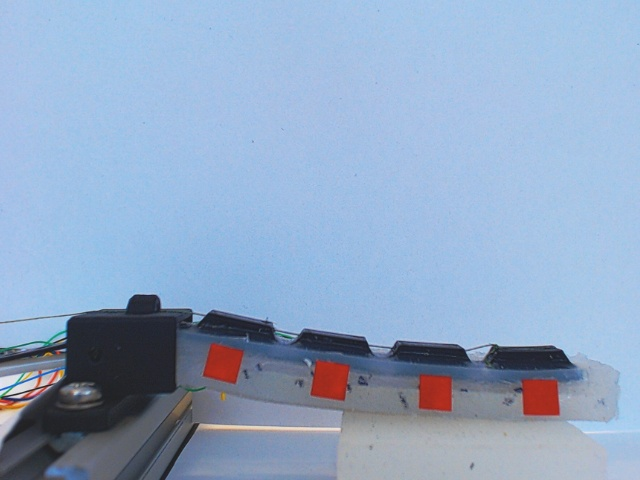
computer_vision/wiredfingersetup.jpg_1220.jpg
