cdelor02/mres-thesis/EIT_test_code/EIT_data_vs_steps--copper_actuator_test_fixed.jpg

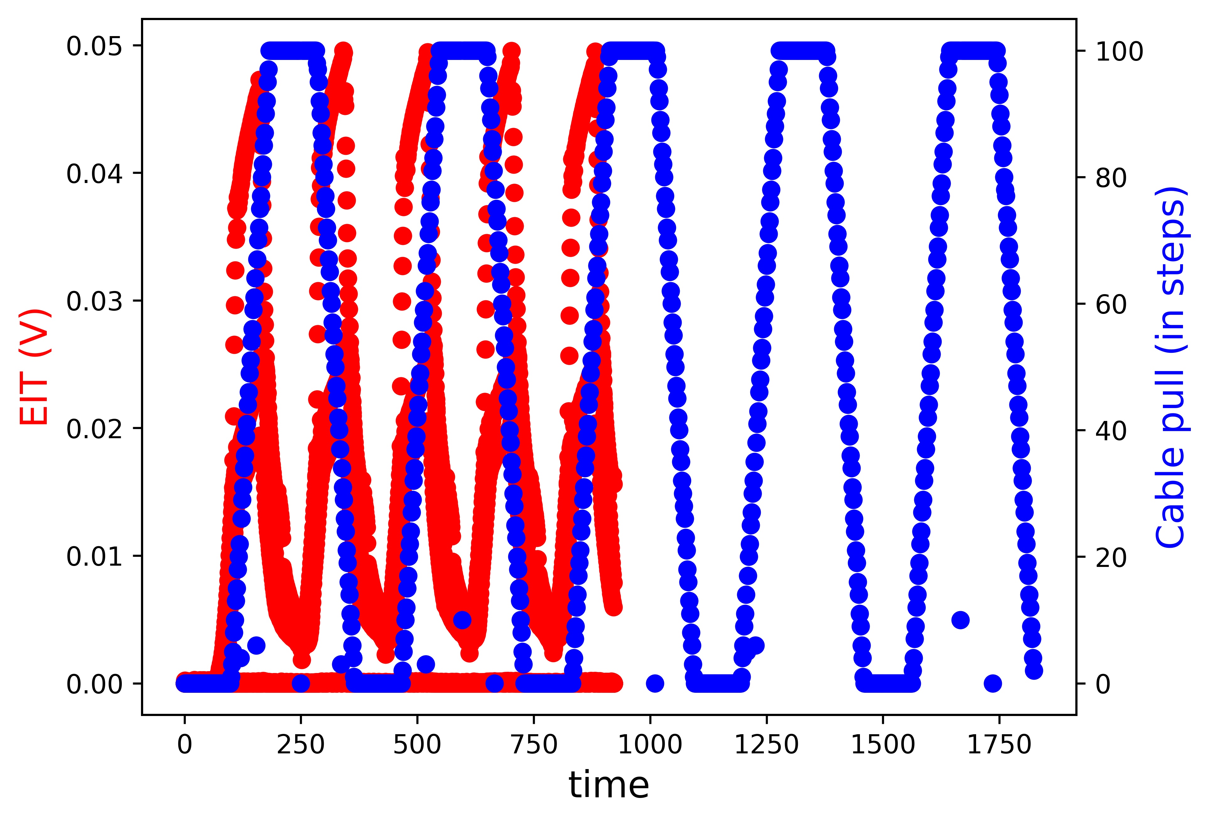
EIT_test_code/EIT_data_vs_steps--copper_actuator_test_fixed.jpg
