cdelor02/mres-thesis/images/3d_print_actuator_iso.jpg

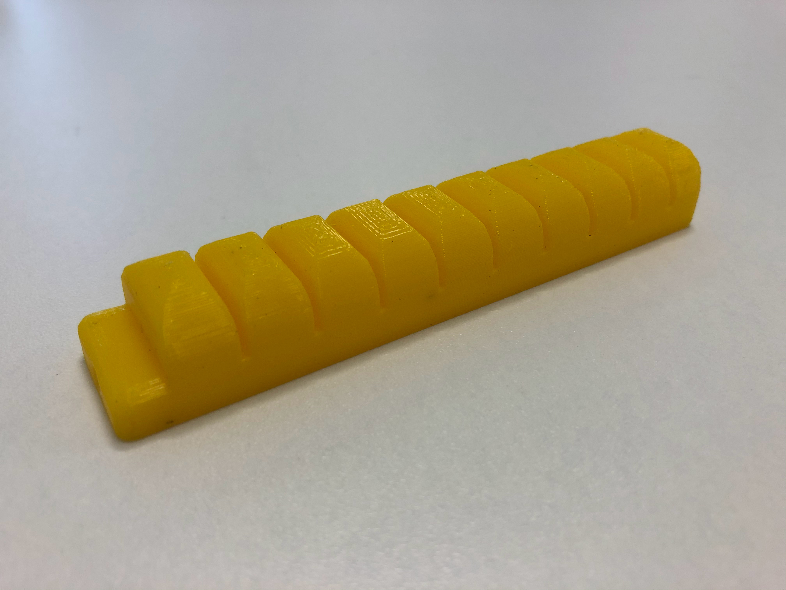
images/3d_print_actuator_iso.jpg
