cdelor02/mres-thesis/images/3d_print_actuator_section_view.png

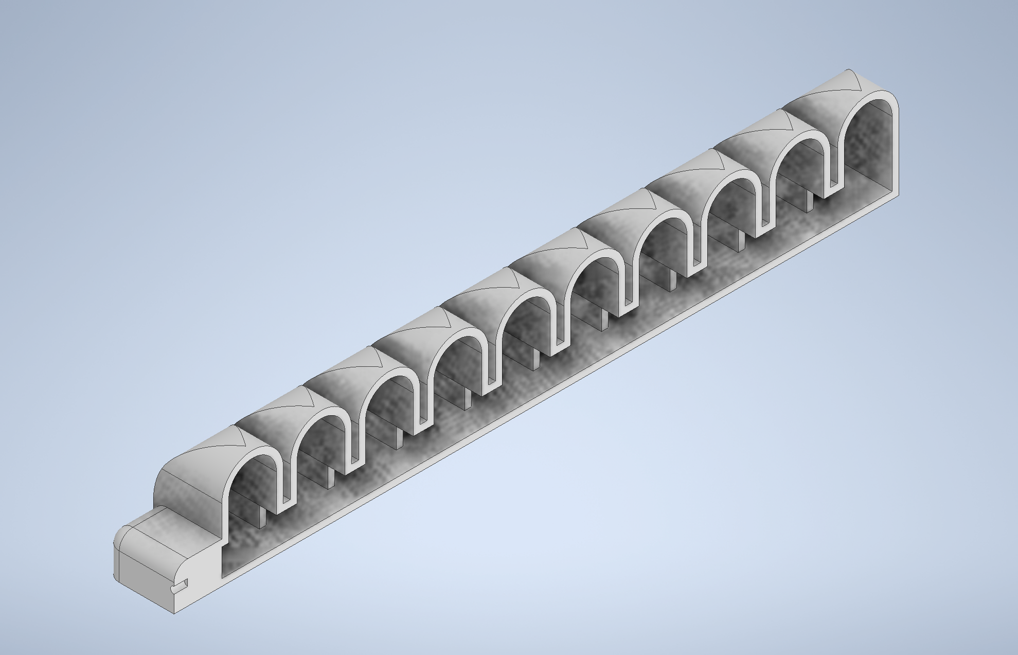
images/3d_print_actuator_section_view.png
