cdelor02/mres-thesis/images/35fast_chamber_100g_weight_plots/weight_lift_110_steps_EIT_data_w_xy_coord_values.png

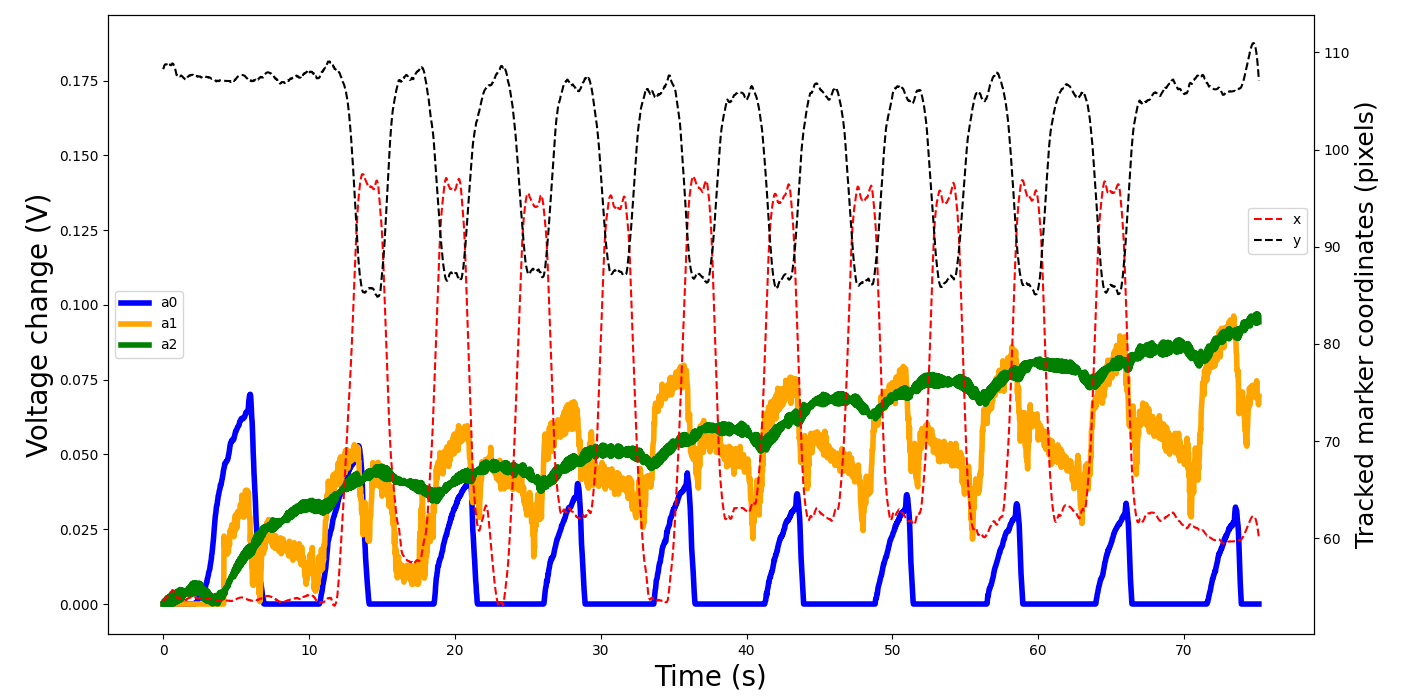
images/35fast_chamber_100g_weight_plots/weight_lift_110_steps_EIT_data_w_xy_coord_values.png
