cdelor02/mres-thesis/images/anterior_actuator_1_4_manual_eit_reading.png

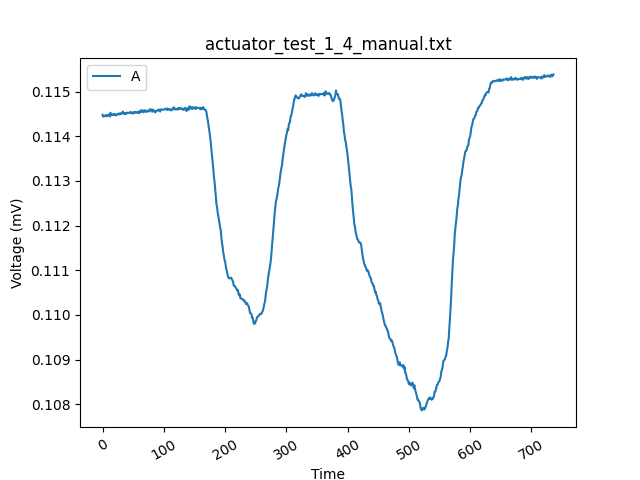
images/anterior_actuator_1_4_manual_eit_reading.png
