cdelor02/mres-thesis/images/cable_pull_with_manufactured_lengths.png

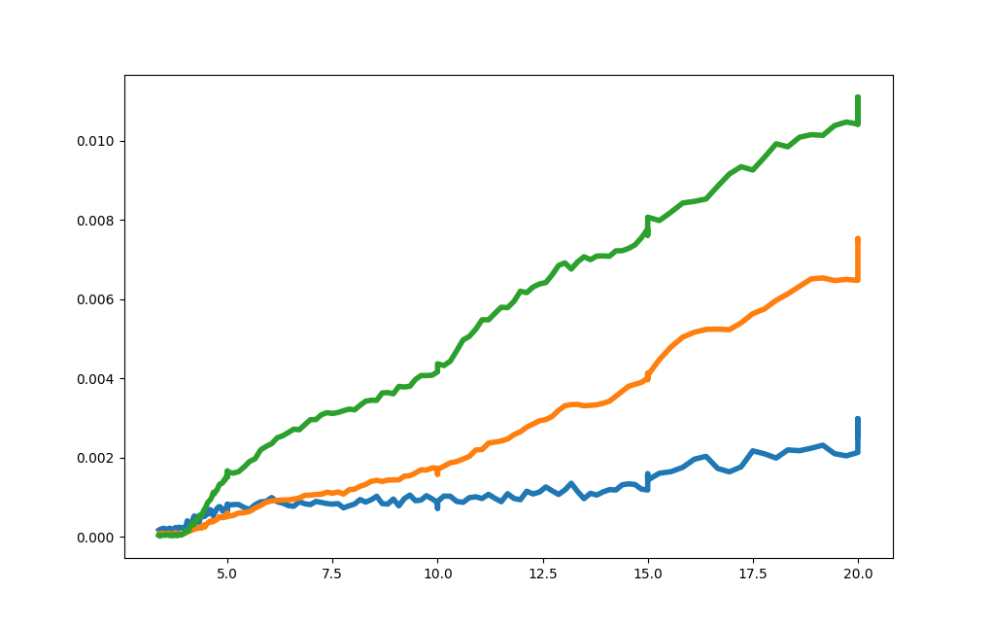
images/cable_pull_with_manufactured_lengths.png
