cdelor02/mres-thesis/images/random_steps_plots/random_steps_ep3.png

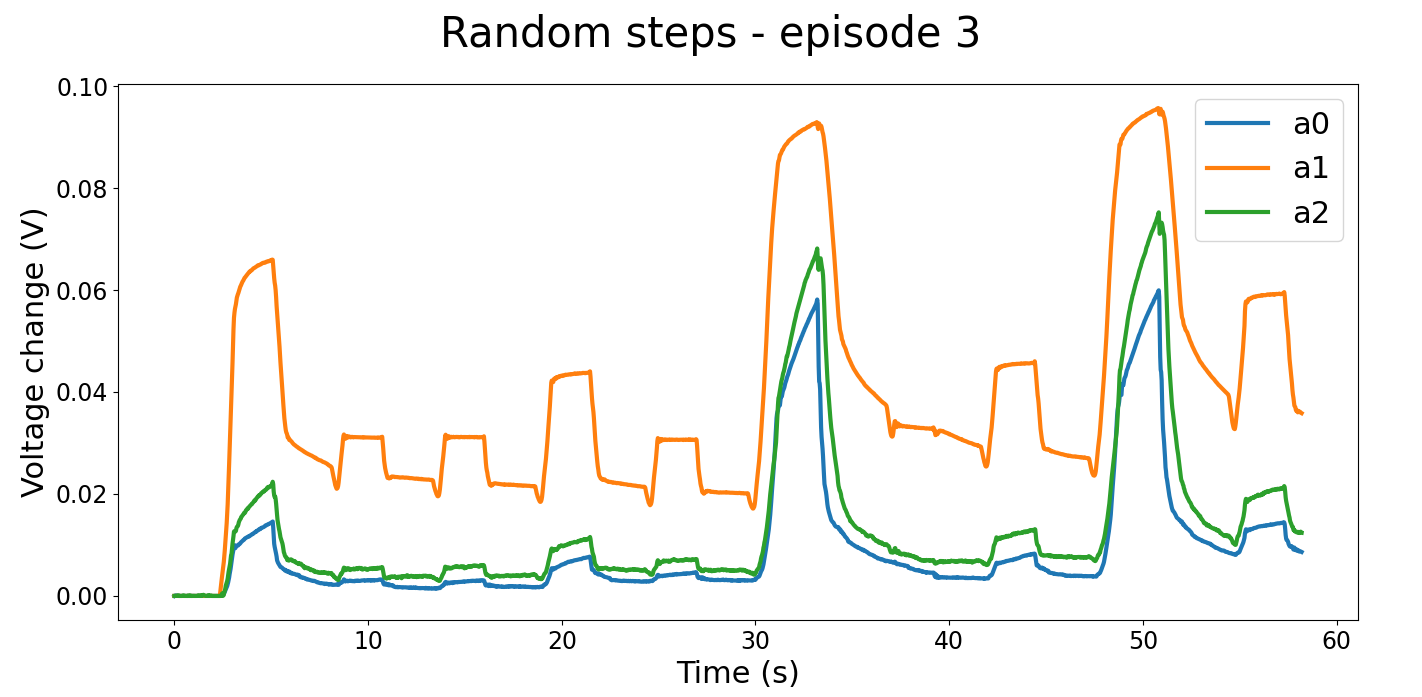
images/random_steps_plots/random_steps_ep3.png
