cdelor02/mres-thesis/images/random_steps_plots/random_steps_ep4.png

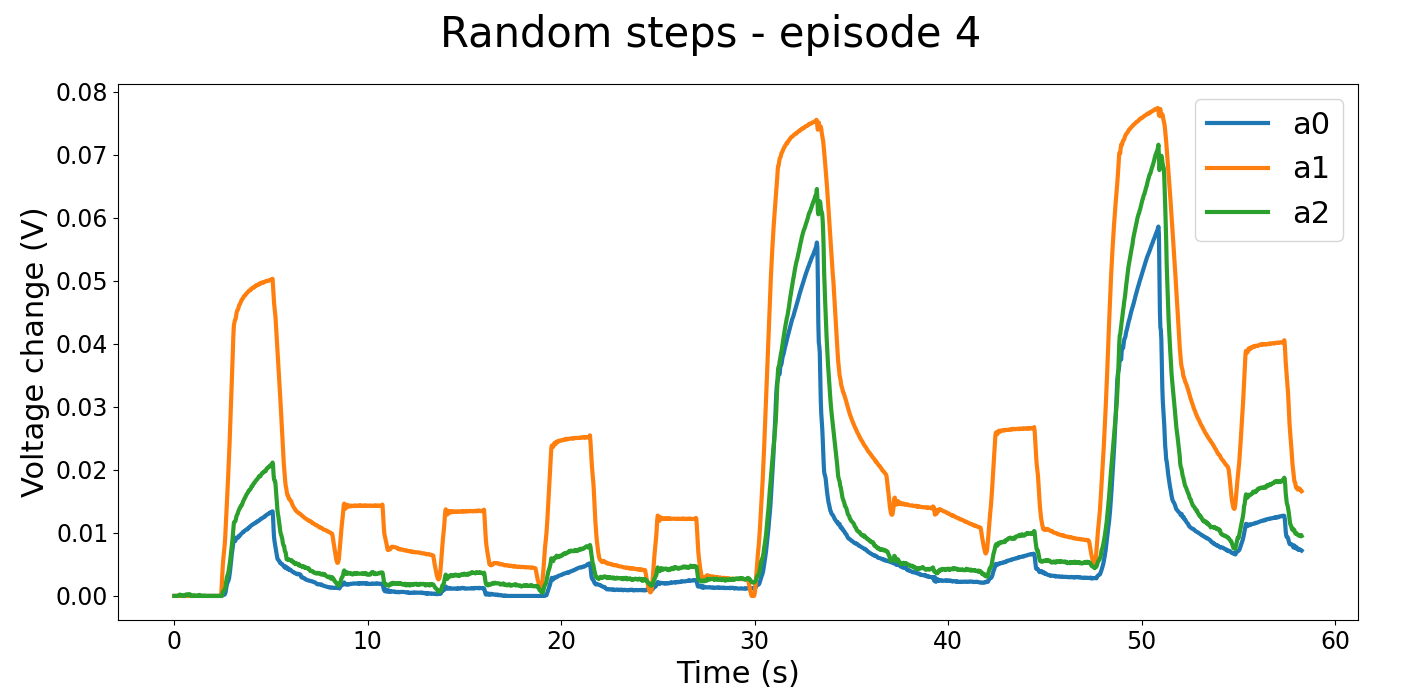
images/random_steps_plots/random_steps_ep4.png
