cdelor02/mres-thesis/images/sdm_actuator_incremental_steps_figure_white_space_cropped.png

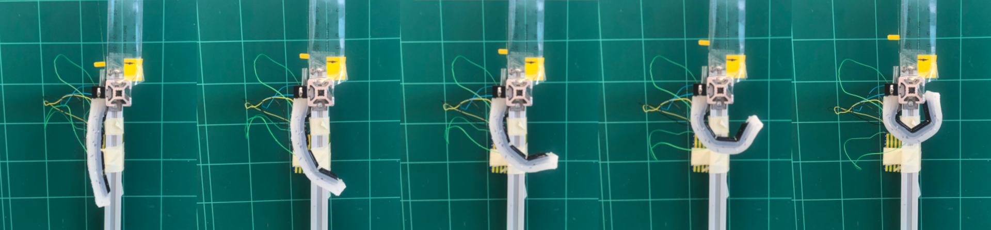
images/sdm_actuator_incremental_steps_figure_white_space_cropped.png
