cdelor02/mres-thesis/journal_club_presentation/soft_robot_actuator_figures/Fig_S6_sensor_fabrication_diagram.png

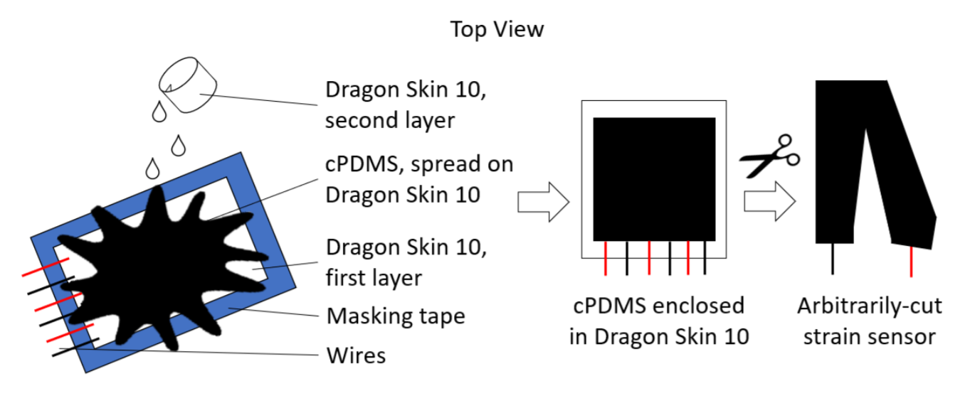
journal_club_presentation/soft_robot_actuator_figures/Fig_S6_sensor_fabrication_diagram.png
