cdelor02/mres-thesis/SDM_actuator/probe_gimbal/gimbal_prototype_assembly.png

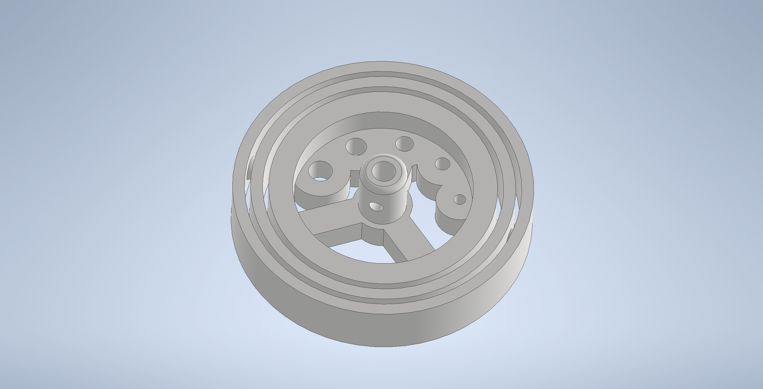
SDM_actuator/probe_gimbal/gimbal_prototype_assembly.png
