cdelor02/mres-thesis/SDM_actuator/sdm_actuator_assembly_first_render.png

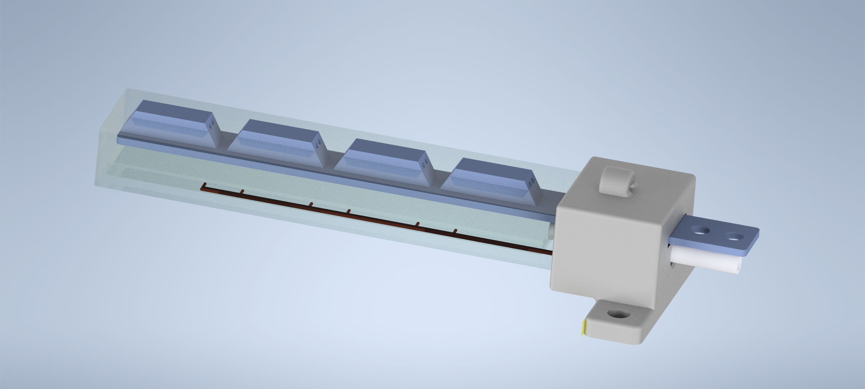
SDM_actuator/sdm_actuator_assembly_first_render.png
