cdelor02/mres-thesis/EIT_test_code/data_for_matlab_lin_reg.csv

 | a0 | a1 | a2 | xpt
0 | 0.0 | 0.0 | 0.0 | 508.0
1 | 0.0 | 0.0 | 0.0 | 508.0
2 | 0.0 | 3.399999999997849e-05 | 0.0 | 508.0
3 | 0.0 | 5.1999999999996493e-05 | 0.0 | 508.0
4 | 5.8000000000002494e-05 | 3.100000000000325e-05 | 0.0 | 508.0
5 | 0.0 | 4.199999999998649e-05 | 0.0 | 508.0
6 | 0.0 | 0.0 | 1.8999999999991246e-05 | 508.0
7 | 0.0 | 7.999999999996898e-05 | 1.6000000000016e-05 | 508.0
8 | 0.0 | 7.599999999996498e-05 | 0.00014500000000000624 | 508.0
9 | 0.0 | 0.0 | 3.599999999998049e-05 | 508.0
10 | 0.0 | 4.499999999996174e-05 | 6.899999999998574e-05 | 509.0
11 | 0.0 | 0.00010299999999996423 | 3.399999999997849e-05 | 508.0
12 | 0.0 | 0.00015100000000001224 | 6.699999999998374e-05 | 508.0
13 | 0.0 | 0.00017400000000000748 | 0.00011099999999997223 | 508.0
14 | 0.0 | 0.00014900000000001024 | 0.00013699999999999823 | 508.0
15 | 0.0 | 0.00018899999999999473 | 0.00015699999999996272 | 508.0
16 | 0.0 | 0.00024999999999997247 | 0.00018099999999998673 | 508.0
17 | 0.0 | 0.00028600000000000847 | 0.0002809999999999757 | 508.0
18 | 0.0 | 0.0003110000000000057 | 0.00030799999999997496 | 509.0
19 | 0.0 | 0.00031799999999998496 | 0.0003529999999999922 | 508.0
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
