cdelor02/mres-thesis/computer_vision/actuator_10_iterations_experiments_baseline.png_200.jpg

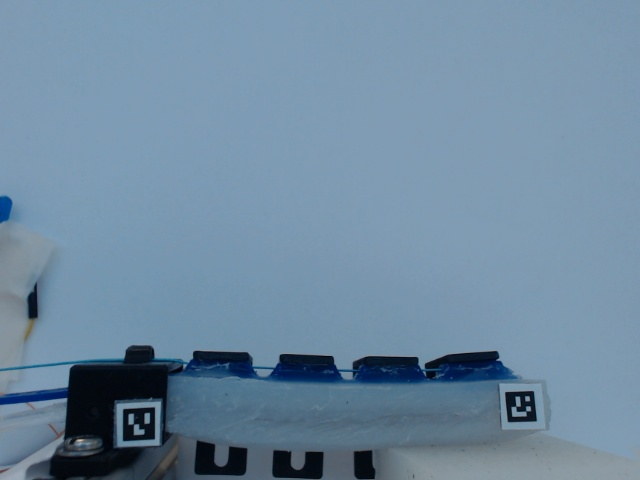
computer_vision/actuator_10_iterations_experiments_baseline.png_200.jpg
