cdelor02/mres-thesis/computer_vision/actuator_10_iterations_experiments_baseline.png_234.jpg

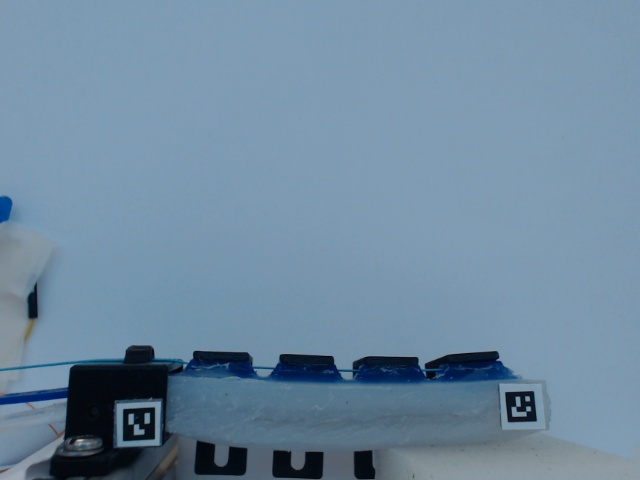
computer_vision/actuator_10_iterations_experiments_baseline.png_234.jpg
