cdelor02/mres-thesis/computer_vision/camera_calibration_attempt-2021-08-20/camera_params-transl-rota-intrinsic_parameters.png

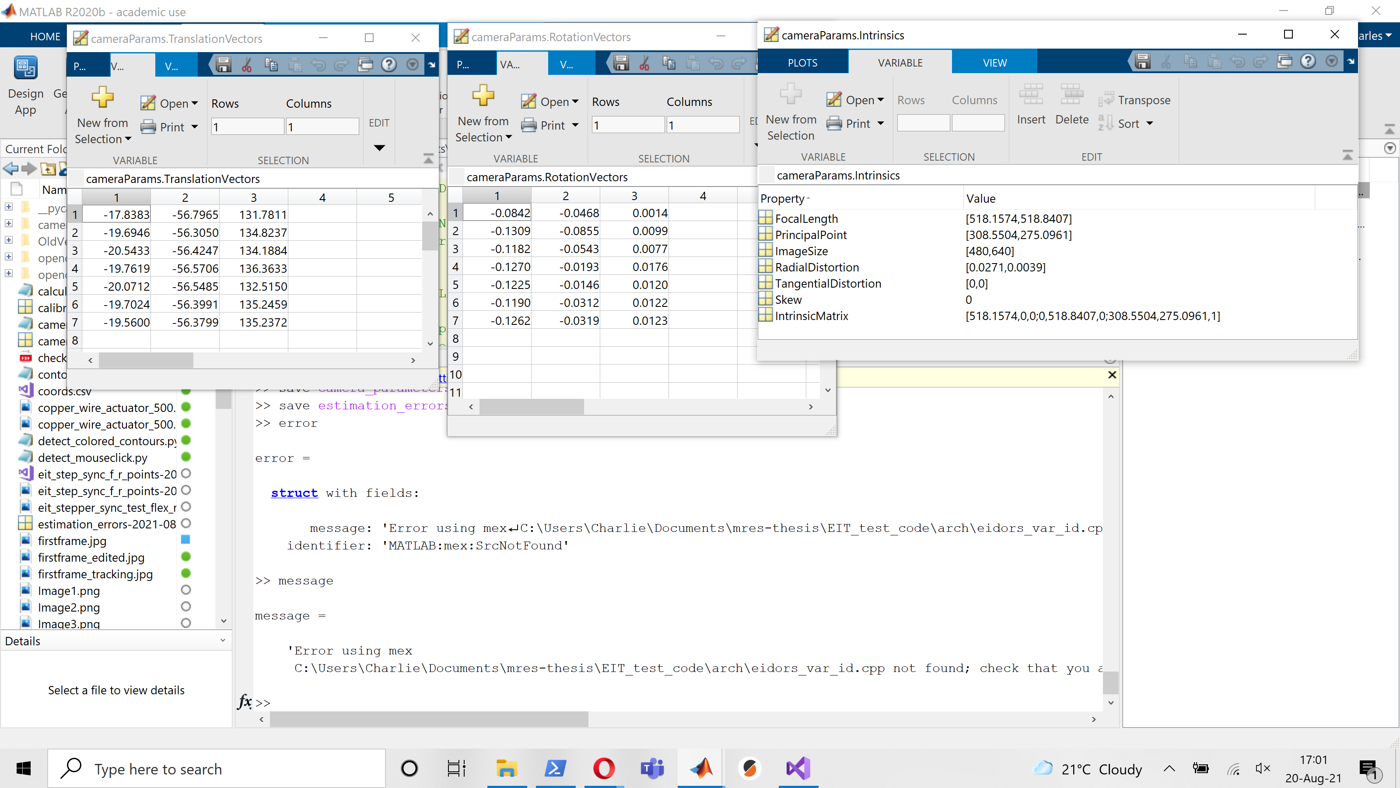
computer_vision/camera_calibration_attempt-2021-08-20/camera_params-transl-rota-intrinsic_parameters.png
