cdelor02/mres-thesis/computer_vision/camera_calibration_attempt-2021-08-20/camera_params-world_points.png

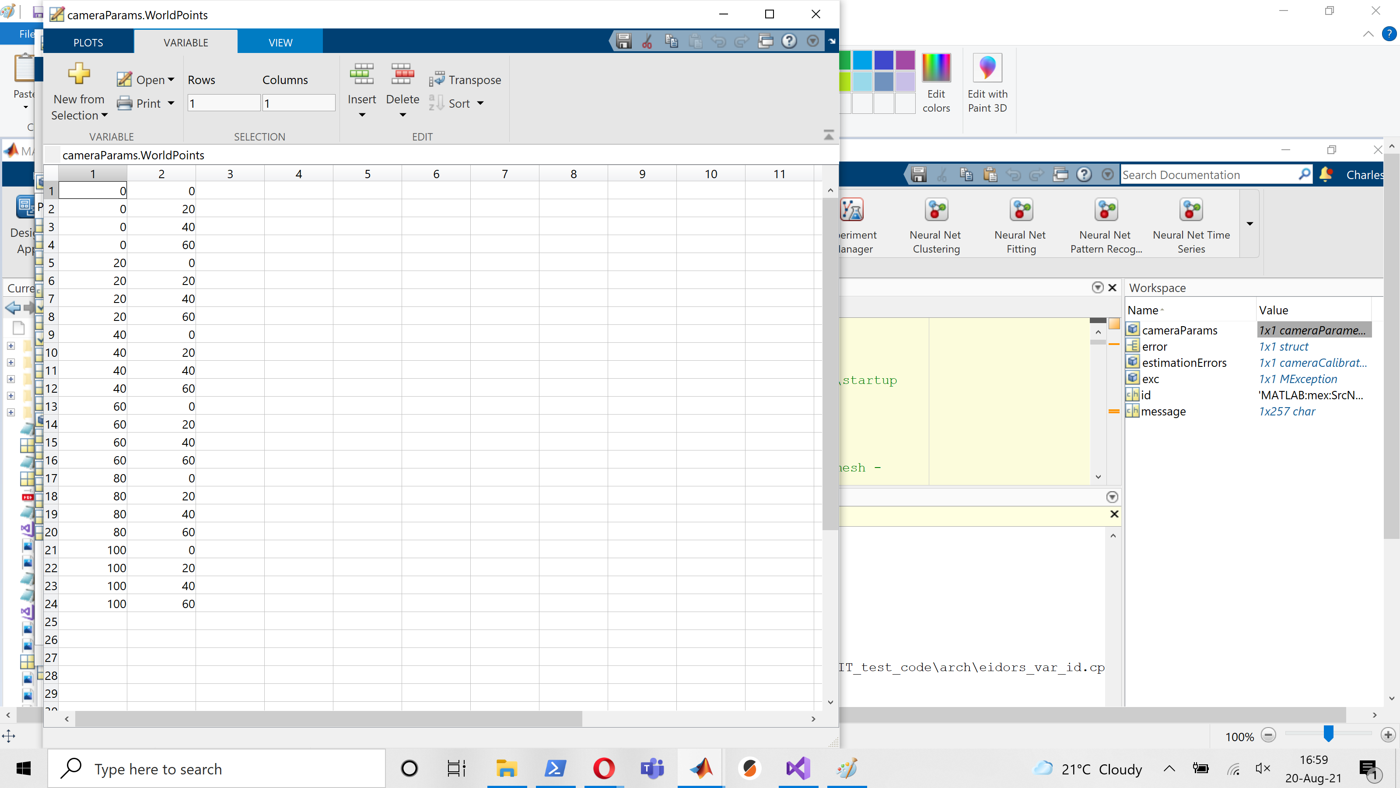
computer_vision/camera_calibration_attempt-2021-08-20/camera_params-world_points.png
