cdelor02/mres-thesis/computer_vision/camera_calibration_attempt-2021-08-20/Image5.png

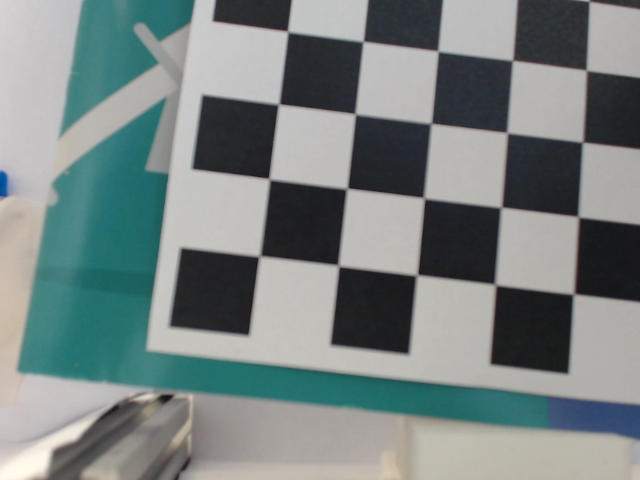
computer_vision/camera_calibration_attempt-2021-08-20/Image5.png
