cdelor02/mres-thesis/computer_vision/camera_calibration_attempt-2021-08-20/Image6.png

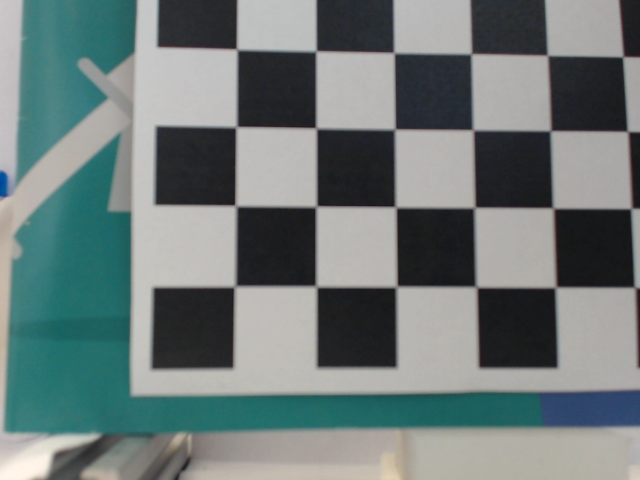
computer_vision/camera_calibration_attempt-2021-08-20/Image6.png
