cdelor02/mres-thesis/computer_vision/eit_stepper_sync_test_flex_relax_all_4_markers_tracked.png

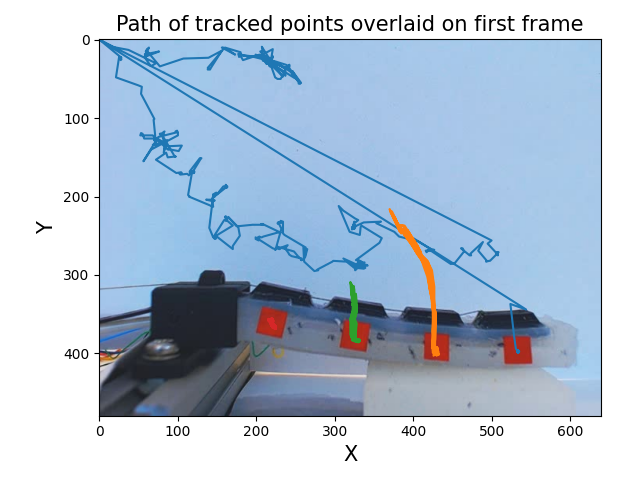
computer_vision/eit_stepper_sync_test_flex_relax_all_4_markers_tracked.png
