cdelor02/mres-thesis/data/10_iterations_10_experiments_done_on-2021-09-01/copper_wire_actuator_35fast_chamber_5_maxmin_10_iterations_2-2021-09-01.png

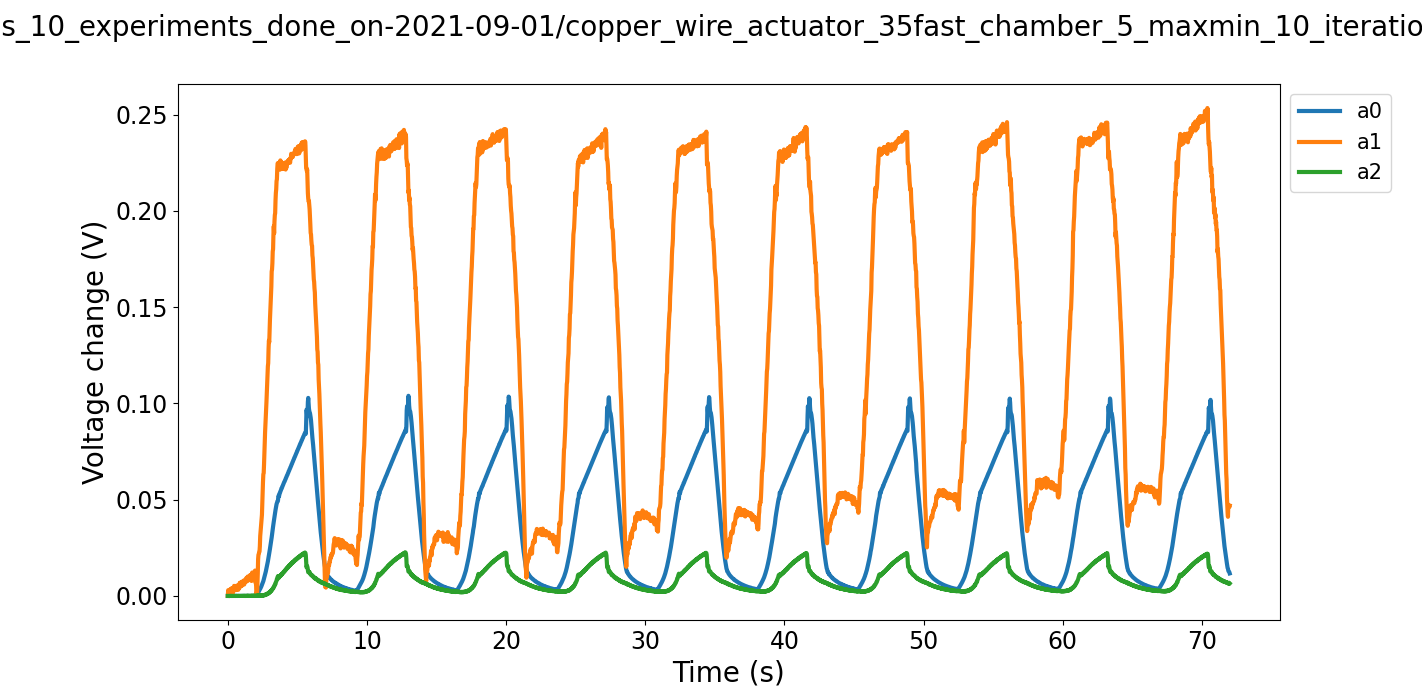
data/10_iterations_10_experiments_done_on-2021-09-01/copper_wire_actuator_35fast_chamber_5_maxmin_10_iterations_2-2021-09-01.png
