cdelor02/mres-thesis/data/actuator_experiments_fixed_a0-2021-09-10/actuator_10_iterations_experiments_10_no34.jpg

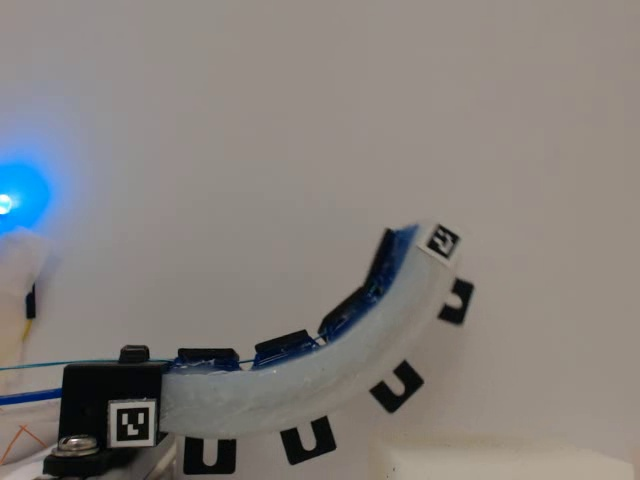
data/actuator_experiments_fixed_a0-2021-09-10/actuator_10_iterations_experiments_10_no34.jpg
