cdelor02/mres-thesis/data/actuator_experiments_fixed_a0-2021-09-10/linear_reg_predictions_fixed_a0_6_experiment.png

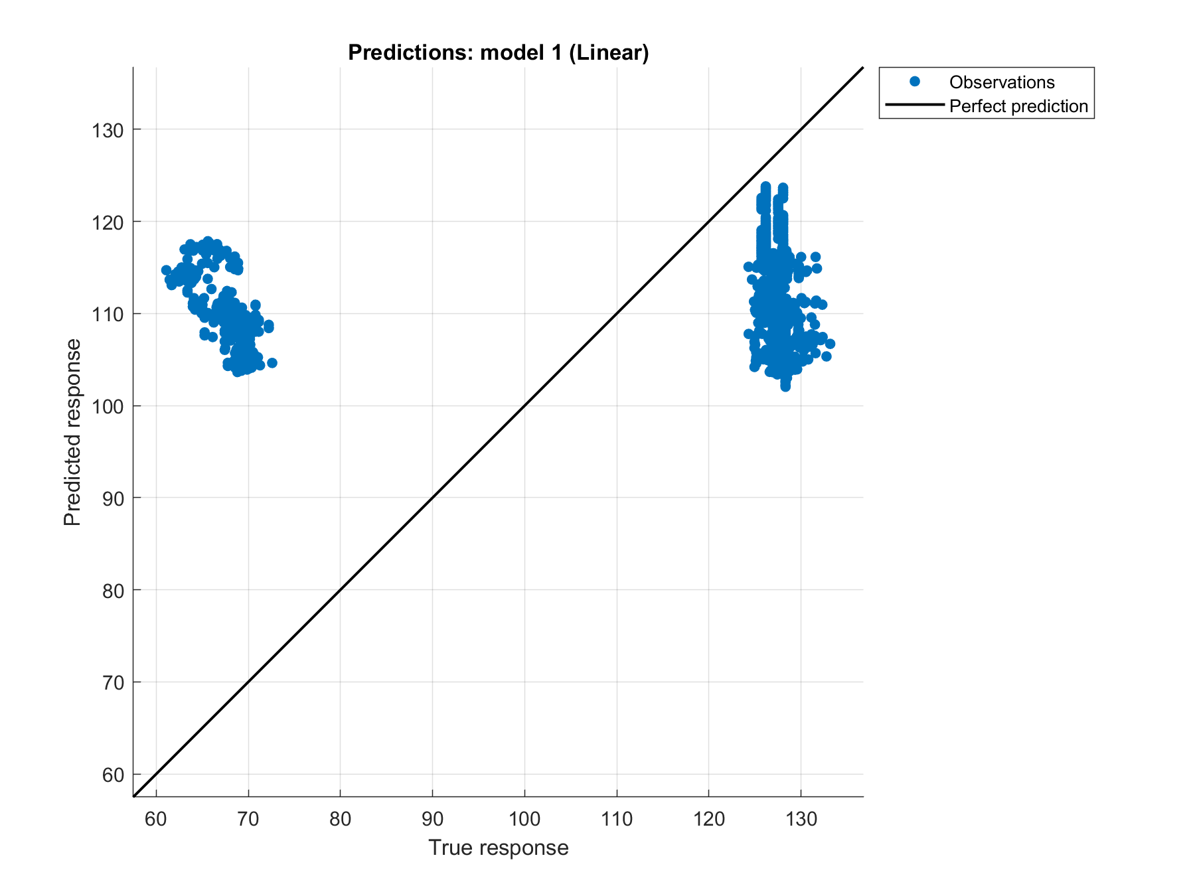
data/actuator_experiments_fixed_a0-2021-09-10/linear_reg_predictions_fixed_a0_6_experiment.png
