cdelor02/mres-thesis/data/actuator_experiments_rand_step-2021-09-10/labview_code_randstep_actuator_experiments.png

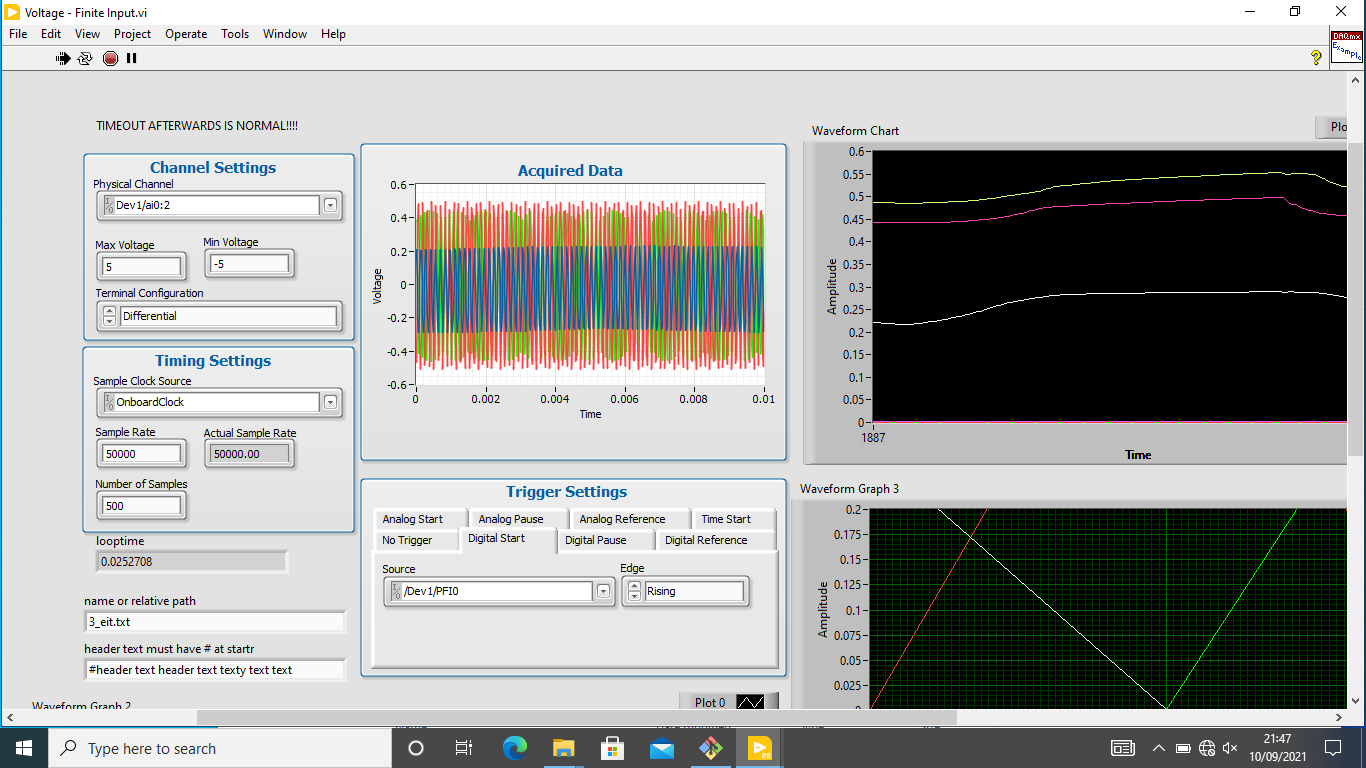
data/actuator_experiments_rand_step-2021-09-10/labview_code_randstep_actuator_experiments.png
