cdelor02/mres-thesis/data/joint_angle_measurements-2021-08-24/joint_angle_measurements.png

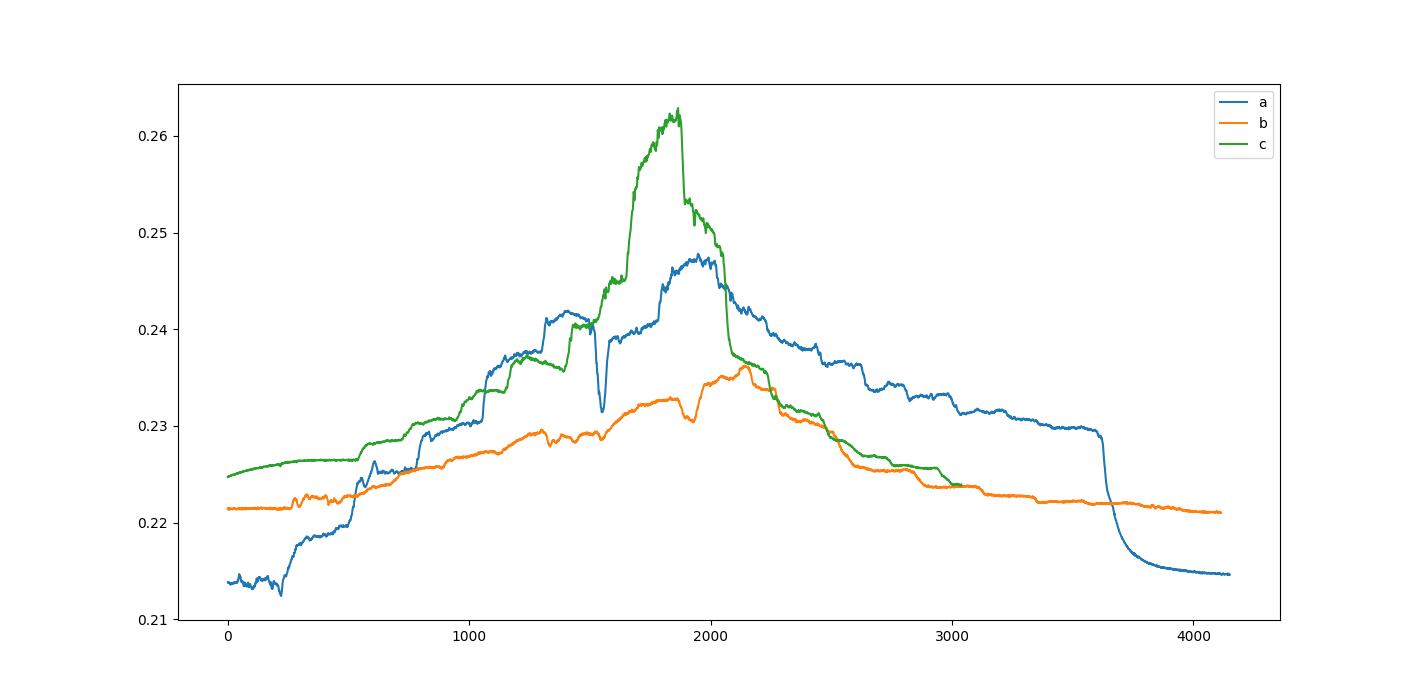
data/joint_angle_measurements-2021-08-24/joint_angle_measurements.png
