cdelor02/mres-thesis/data/joint_angle_measurements_individual-2021-08-25/a0_20deg_odd_oscillations.png

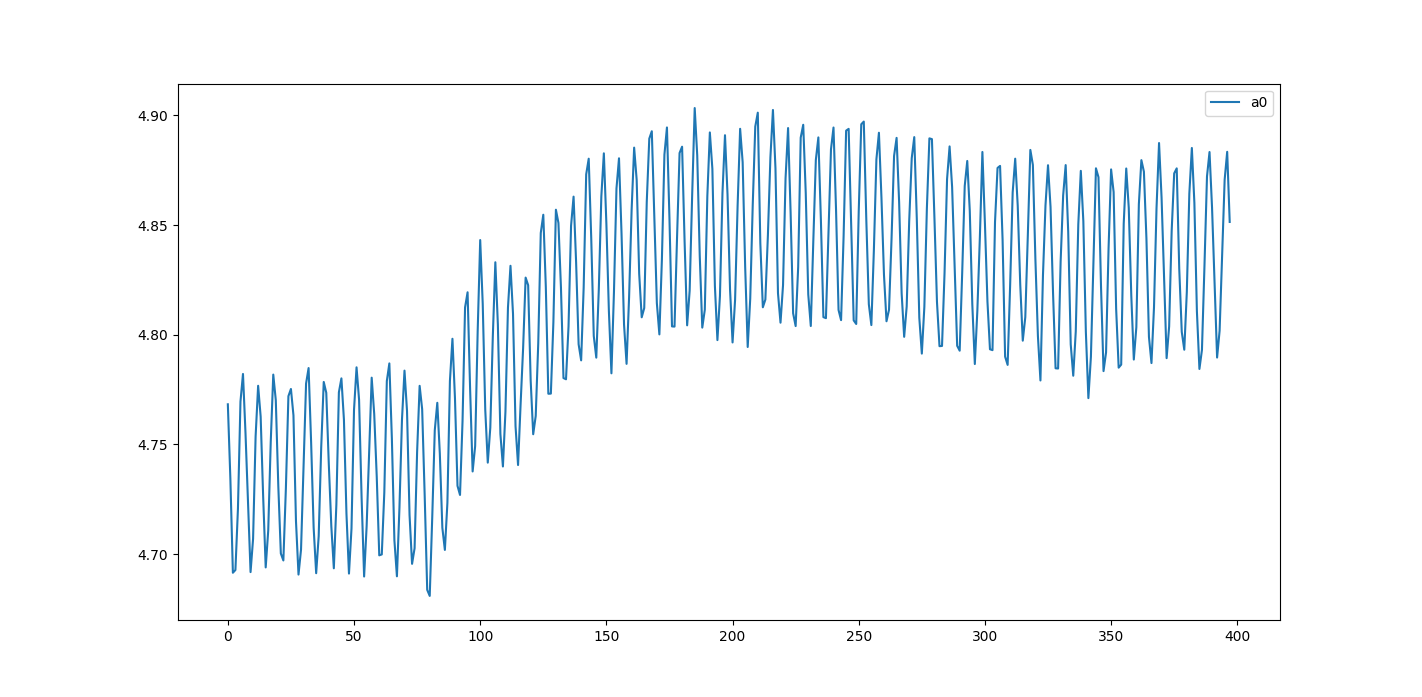
data/joint_angle_measurements_individual-2021-08-25/a0_20deg_odd_oscillations.png
