cdelor02/mres-thesis/data/joint_angle_measurements_individual-2021-08-25/Figure_1.png

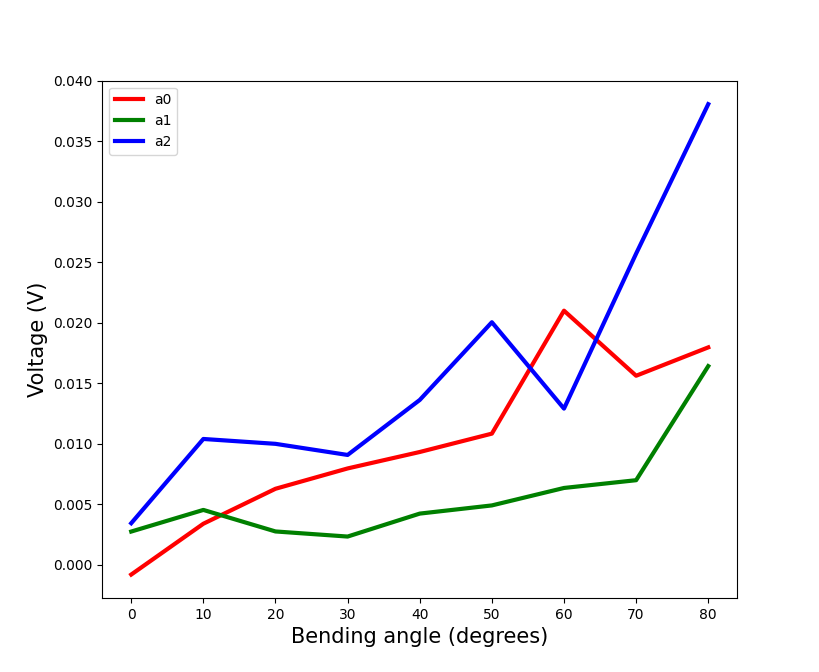
data/joint_angle_measurements_individual-2021-08-25/Figure_1.png
