cdelor02/mres-thesis/data/joint_angle_measurements_individual-2021-08-25/voltage_vs_angle-2021-08-25.png

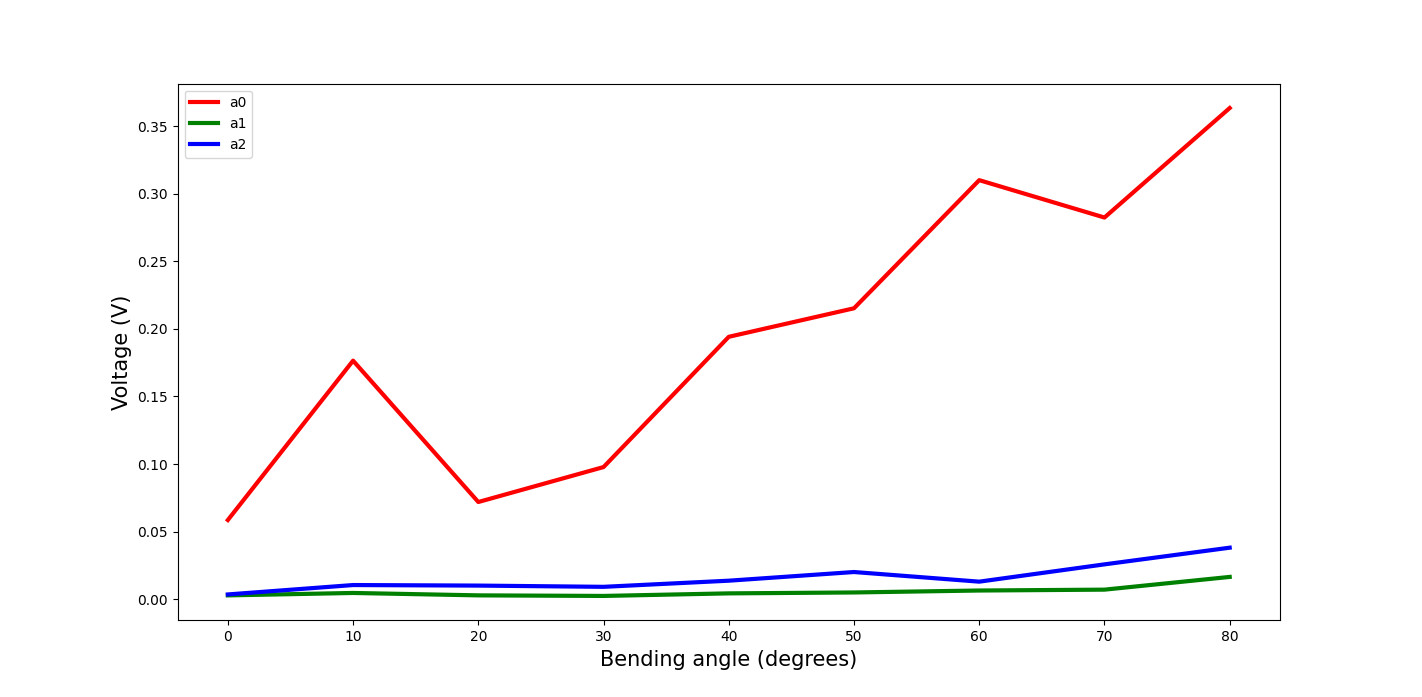
data/joint_angle_measurements_individual-2021-08-25/voltage_vs_angle-2021-08-25.png
