cdelor02/mres-thesis/EIT_test_code/from_copper_actuator_test_fixed-EIT_vs_cable_pull_data--5_iterations_bigger_font_2.jpg

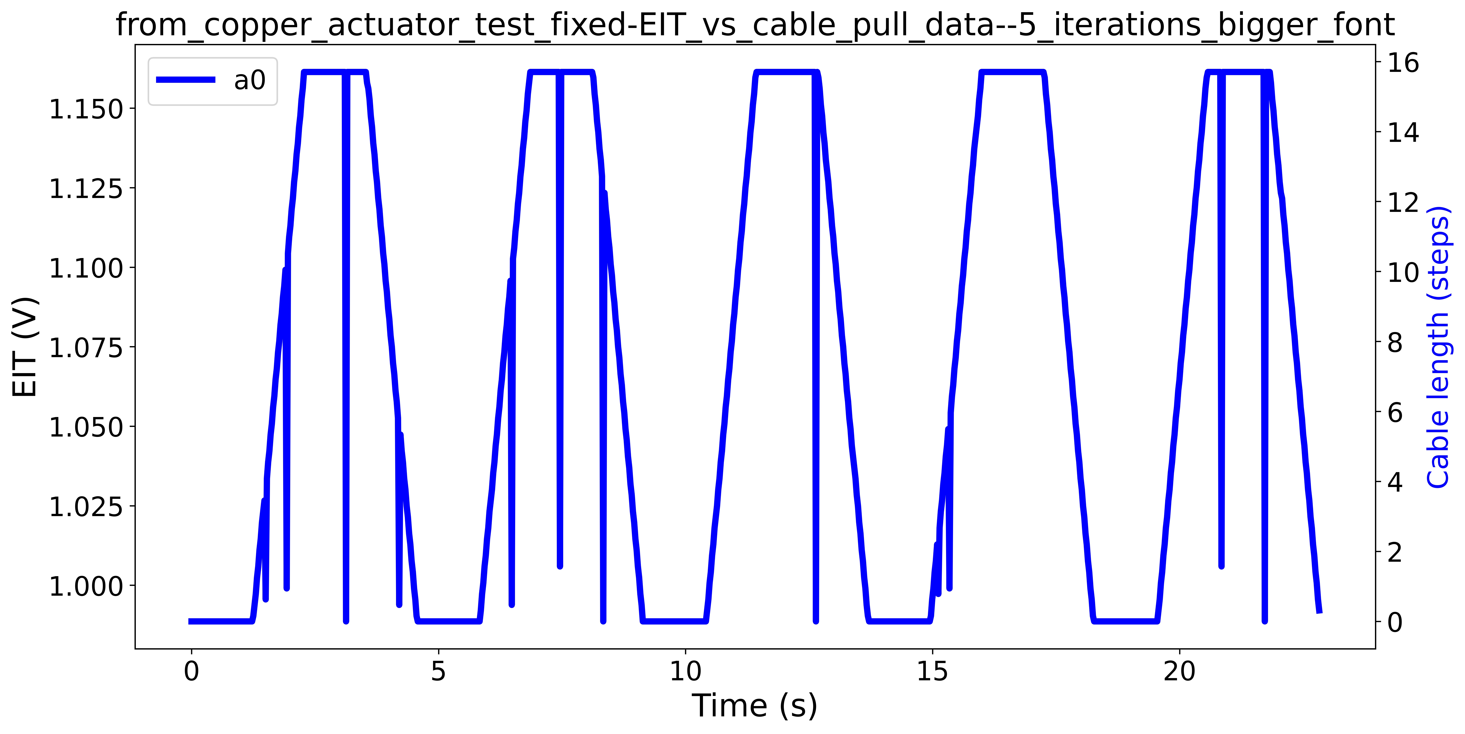
EIT_test_code/from_copper_actuator_test_fixed-EIT_vs_cable_pull_data--5_iterations_bigger_font_2.jpg
