cdelor02/mres-thesis/images/5__duetimer_test_data.png

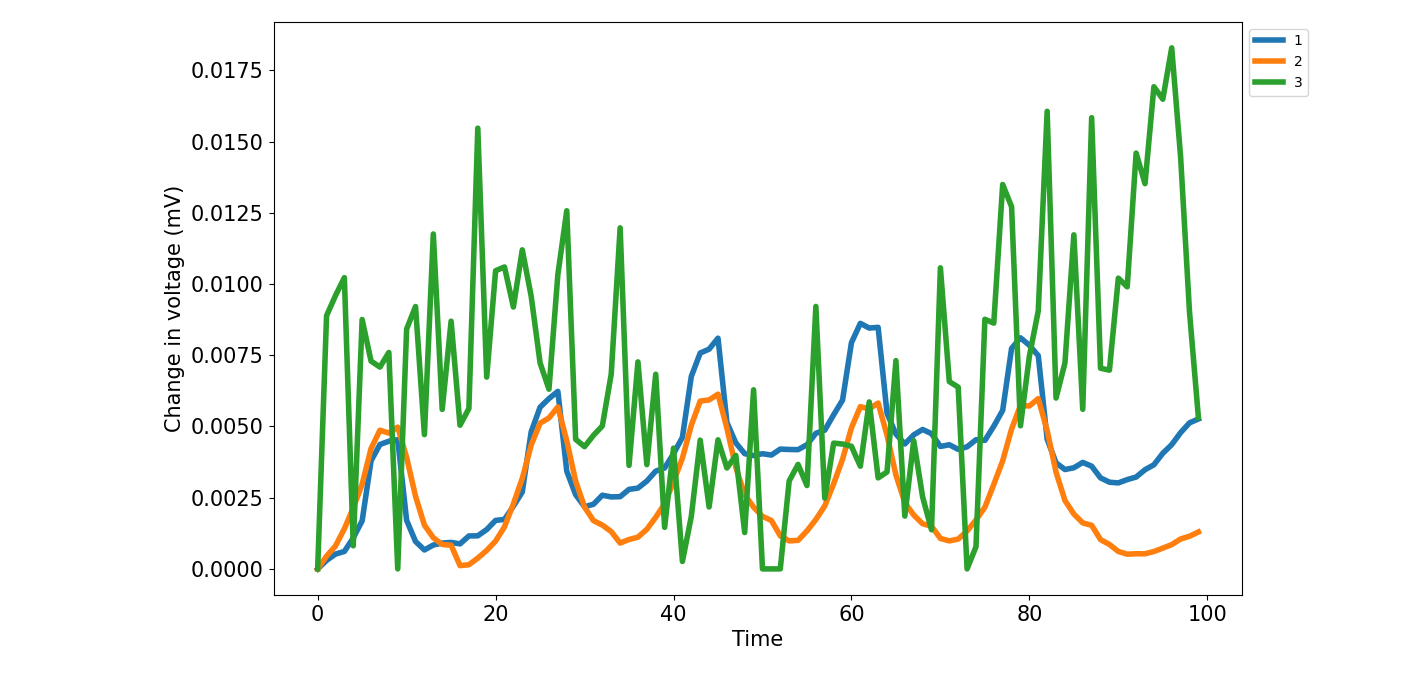
images/5__duetimer_test_data.png
