cdelor02/mres-thesis/images/5_epoch_tested_data.png

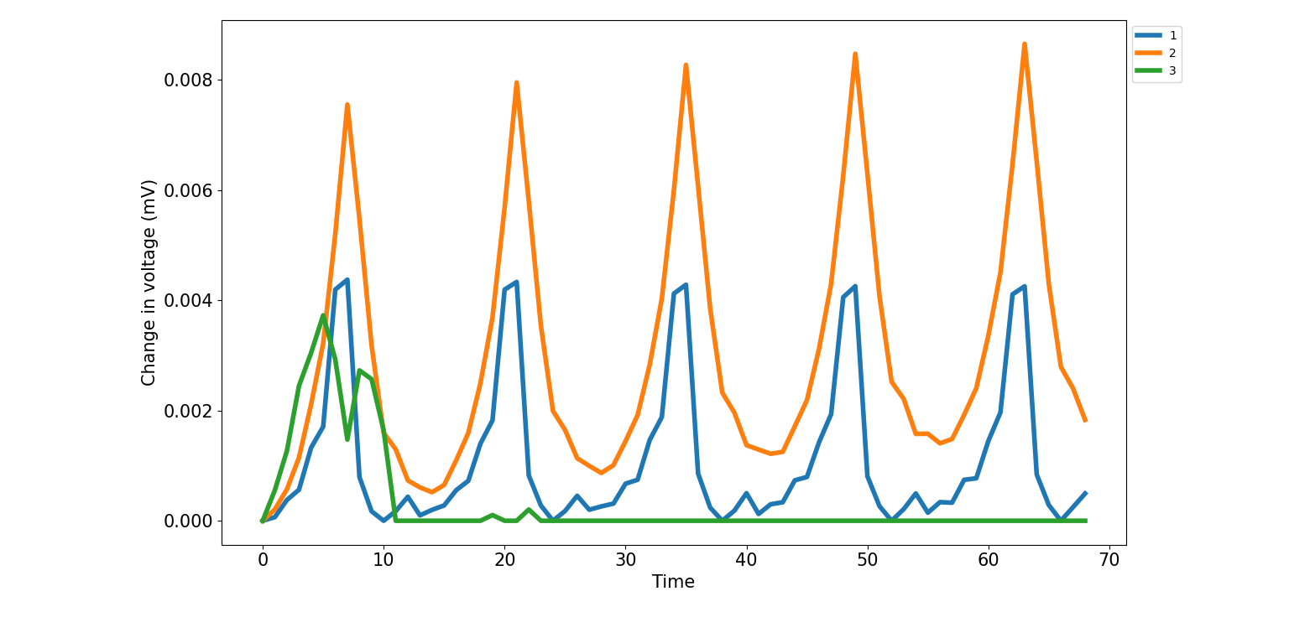
images/5_epoch_tested_data.png
