cdelor02/mres-thesis/images/10_epoch_tested_data.png

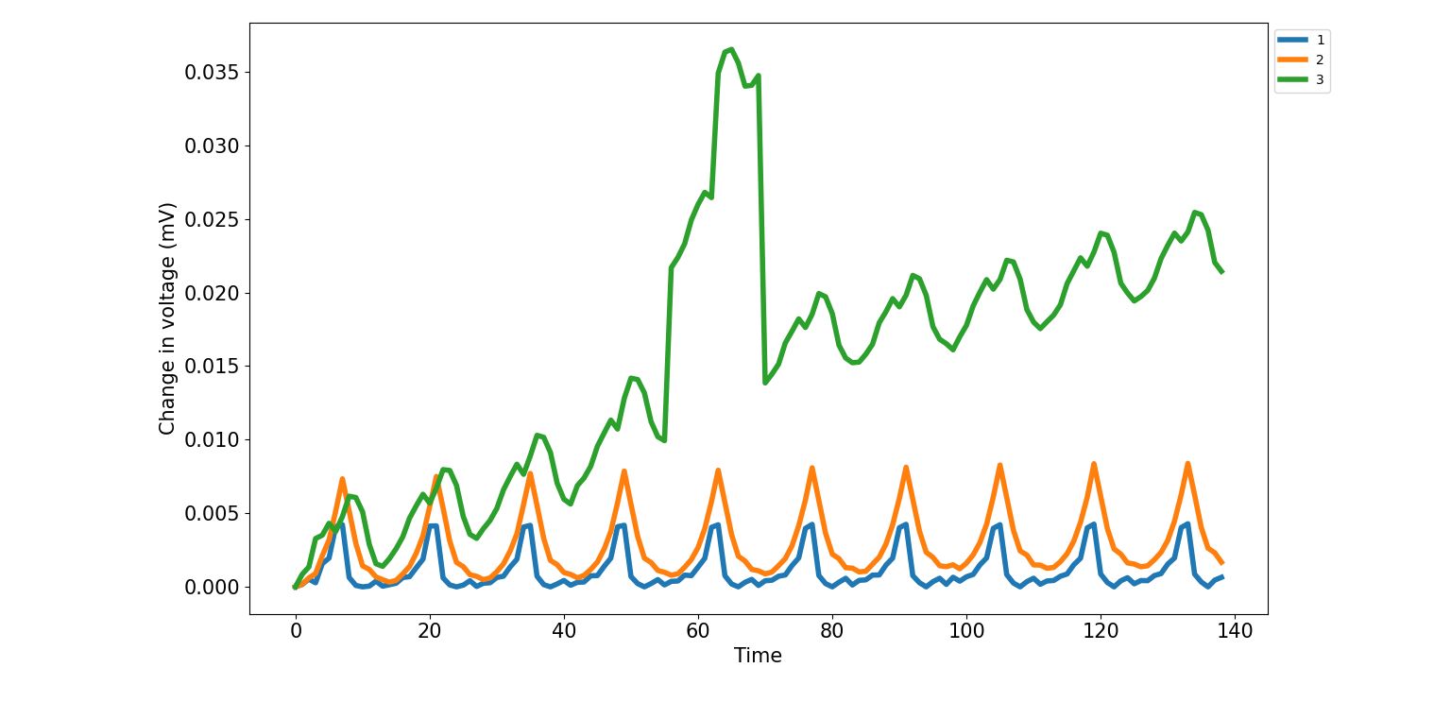
images/10_epoch_tested_data.png
