cdelor02/mres-thesis/images/bending_angle_w_measured_voltage_by_joint_thorough_experiment-2021-09-05.png

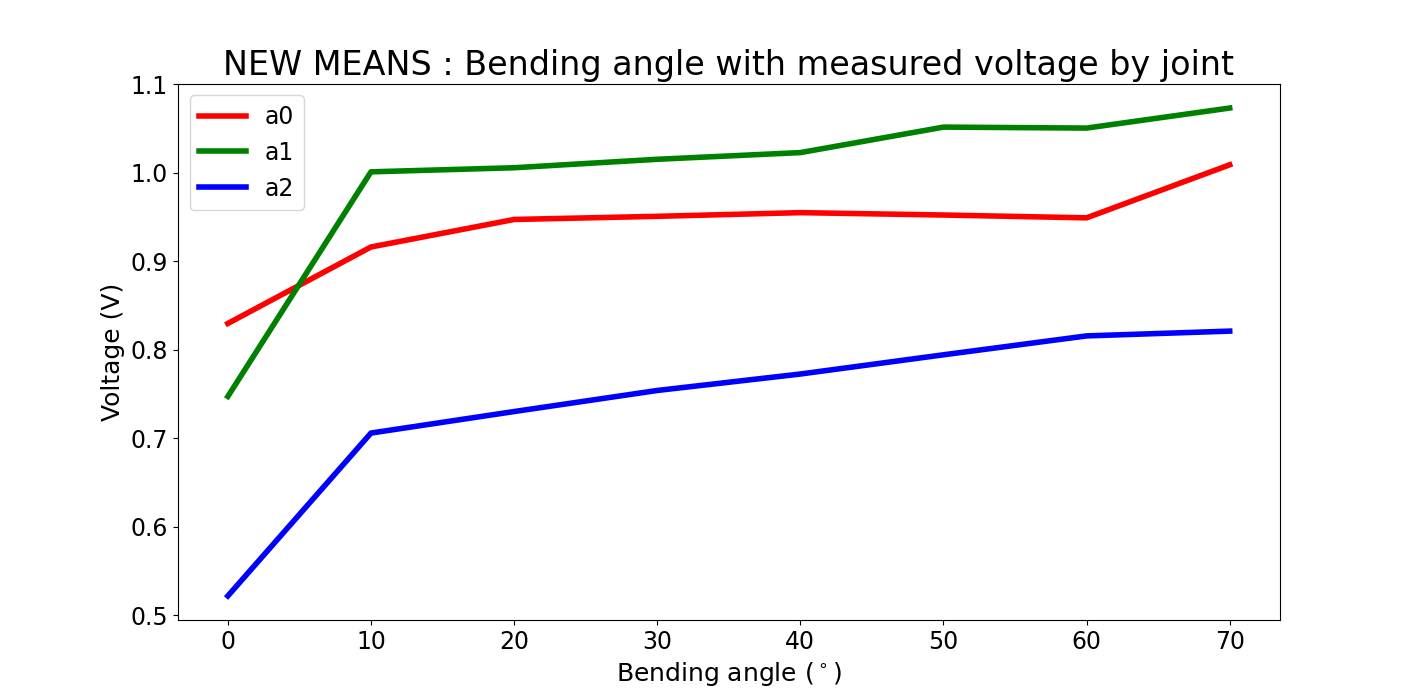
images/bending_angle_w_measured_voltage_by_joint_thorough_experiment-2021-09-05.png
