cdelor02/mres-thesis/images/colored_by_epair-5__duetimer_test_data.png

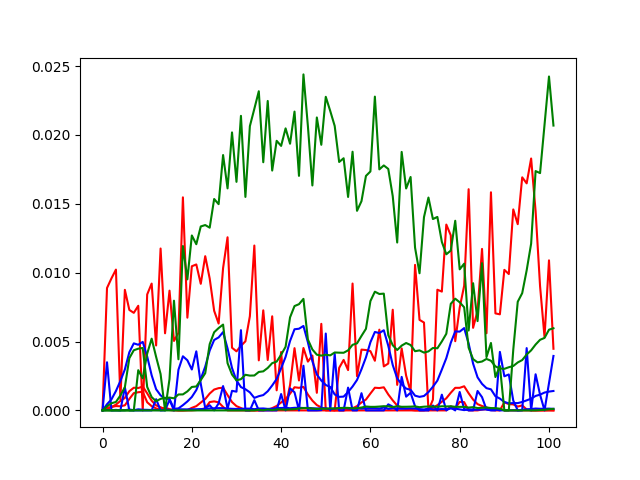
images/colored_by_epair-5__duetimer_test_data.png
