cdelor02/mres-thesis/images/copper_wire_actuator_test_fixed_plot-2021-08-09.png

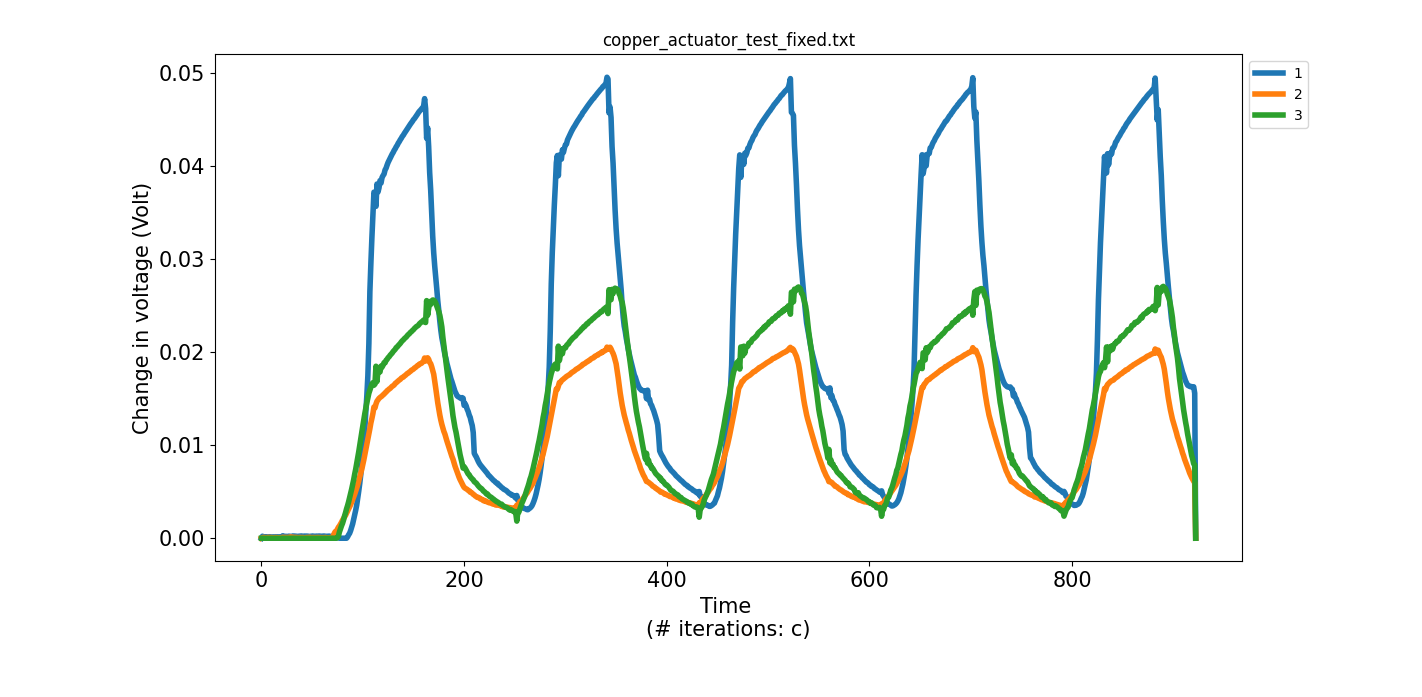
images/copper_wire_actuator_test_fixed_plot-2021-08-09.png
