cdelor02/mres-thesis/images/eit_chamber_glove_test_3_image.png

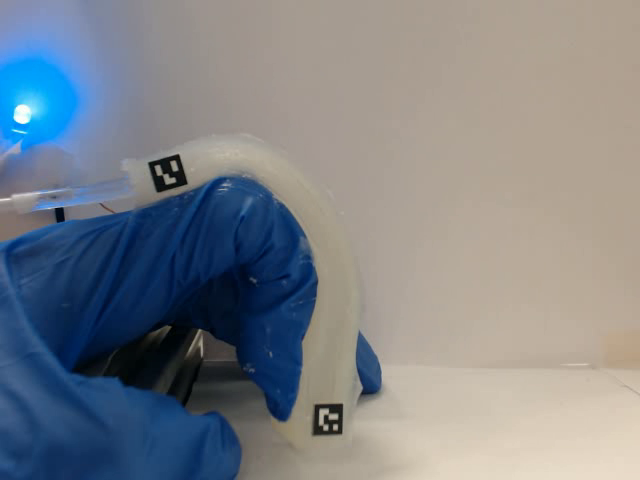
images/eit_chamber_glove_test_3_image.png
