cdelor02/mres-thesis/images/eit_chamber_glove_test_4_peak1.png

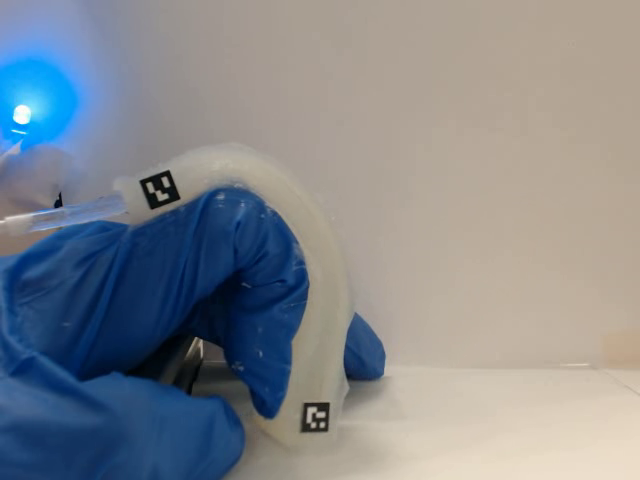
images/eit_chamber_glove_test_4_peak1.png
