cdelor02/mres-thesis/images/eit_chamber_glove_test_6_bitbeforepeak.png

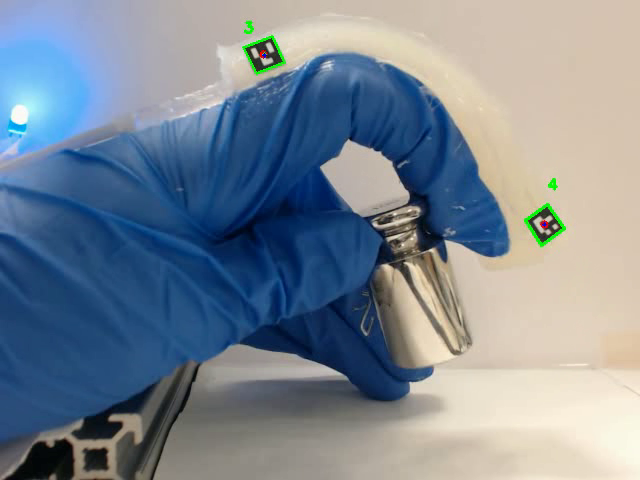
images/eit_chamber_glove_test_6_bitbeforepeak.png
