cdelor02/mres-thesis/images/eit_chamber_glove_test_8_second_plateau.png

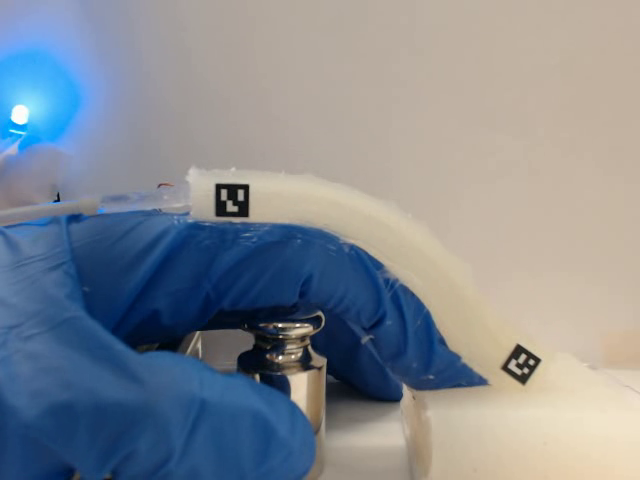
images/eit_chamber_glove_test_8_second_plateau.png
