cdelor02/mres-thesis/images/eit_large_chamber_test.jpg

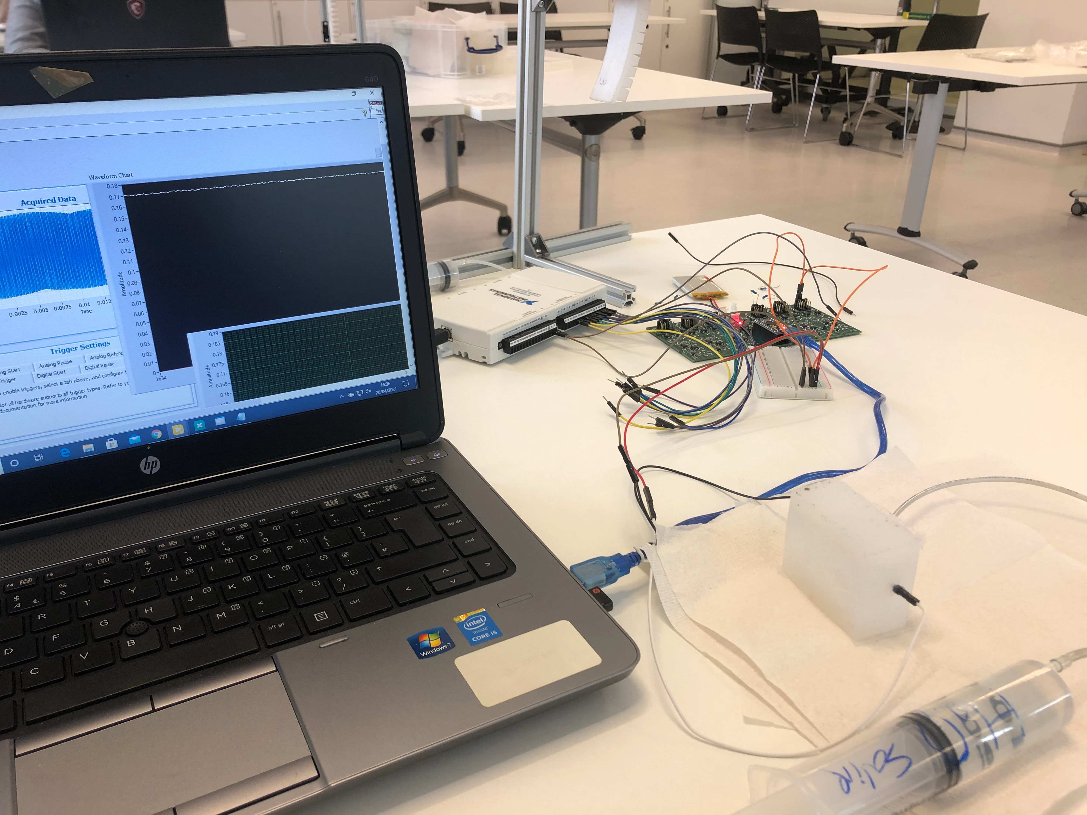
images/eit_large_chamber_test.jpg
