cdelor02/mres-thesis/images/labview_test.png

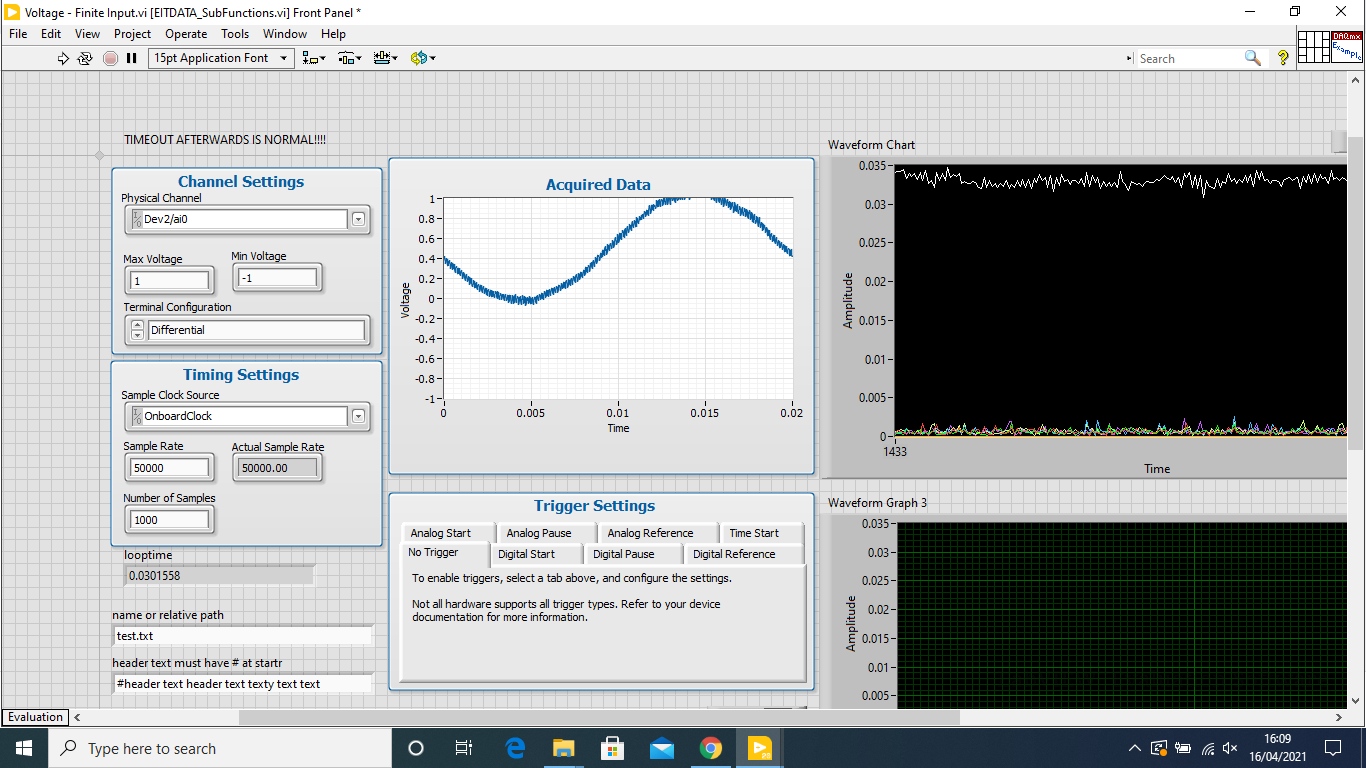
images/labview_test.png
