cdelor02/mres-thesis/images/linear_actuator_test.jpg

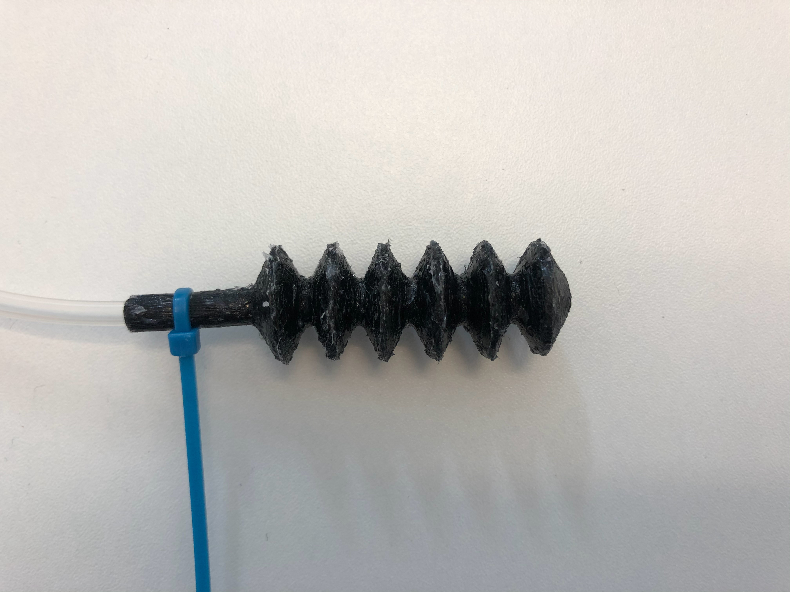
images/linear_actuator_test.jpg
