cdelor02/mres-thesis/images/measurement_of_bending_angle_vs_voltage-2021-08-27.png

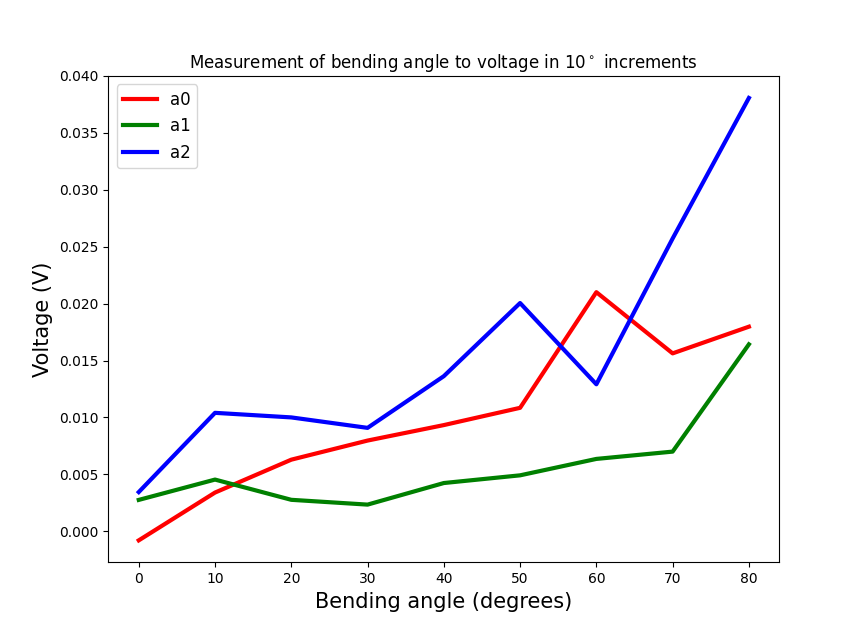
images/measurement_of_bending_angle_vs_voltage-2021-08-27.png
