cdelor02/mres-thesis/images/single_epoch_tested_data.png

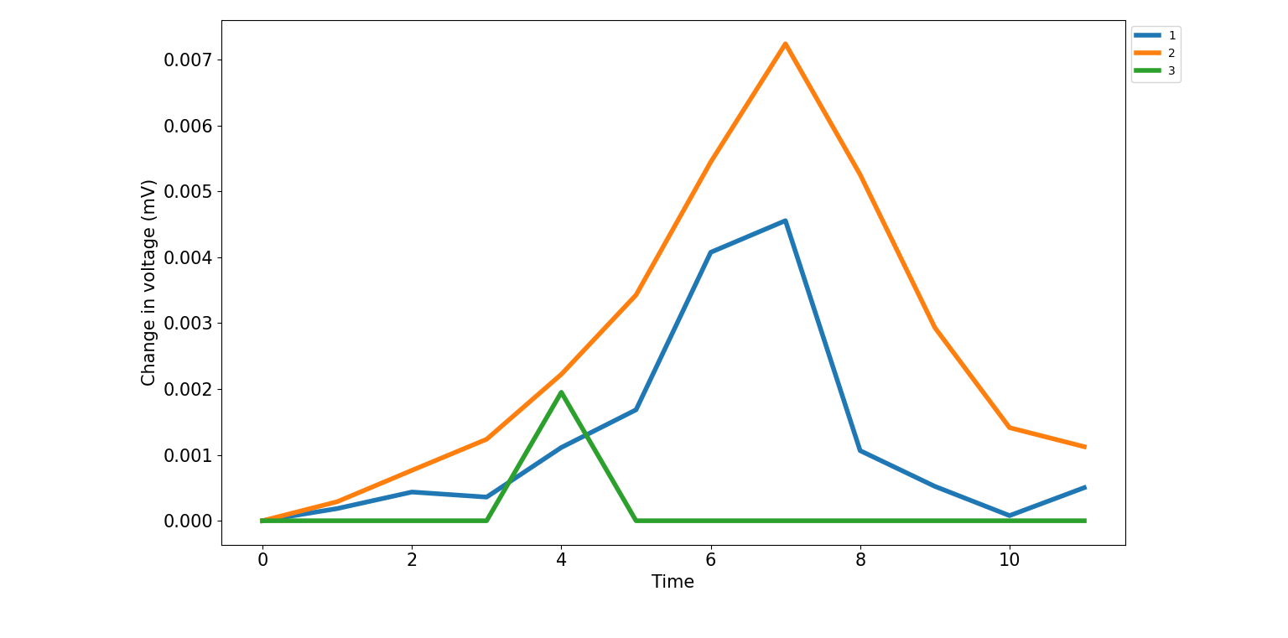
images/single_epoch_tested_data.png
