cdelor02/mres-thesis/images/test_panels_analog_output.png

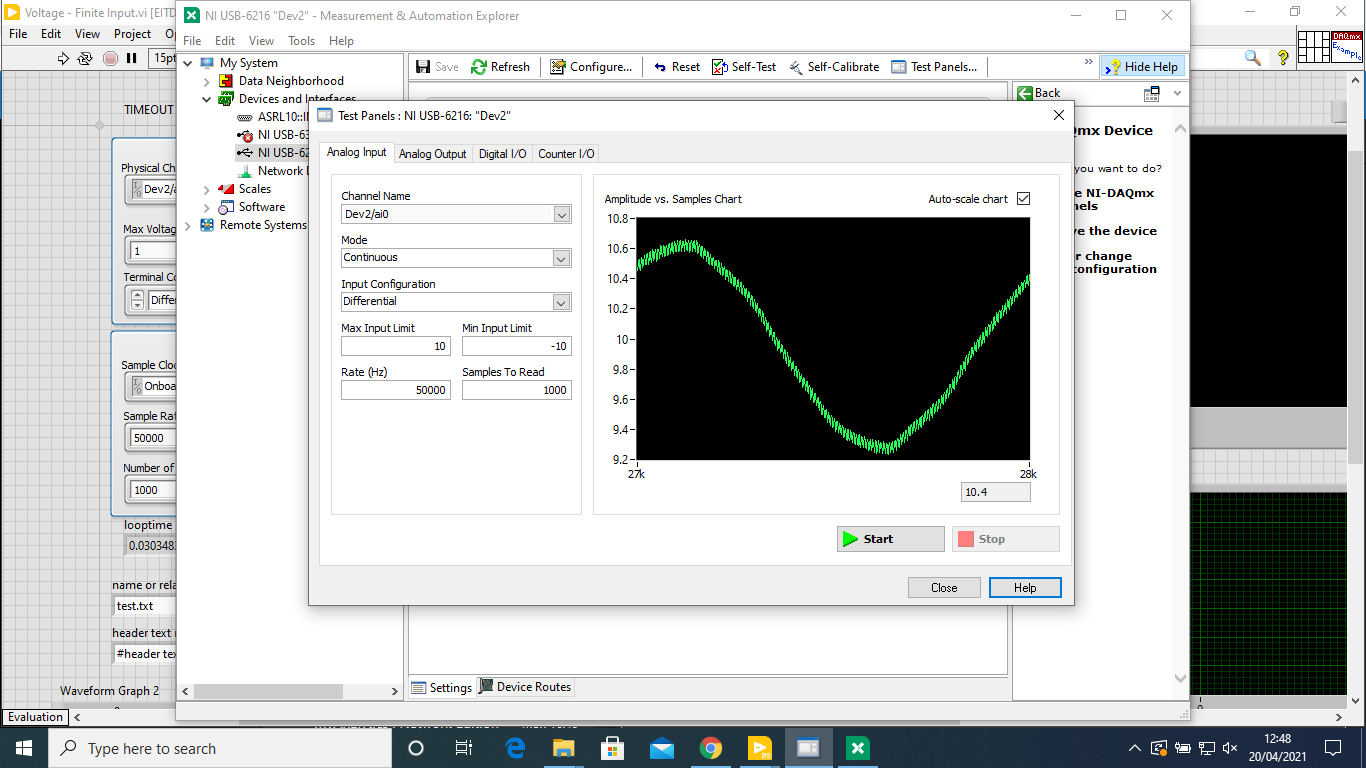
images/test_panels_analog_output.png
