cdelor02/mres-thesis/poster/good_poster_results_figure_4.png

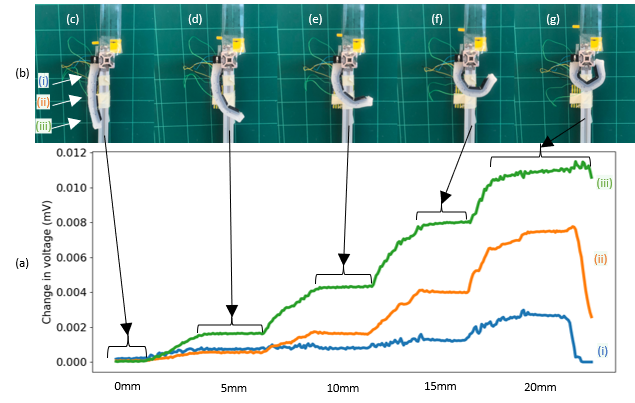
poster/good_poster_results_figure_4.png
