cdelor02/mres-thesis/poster/soft_vs_rigid_robot_test_example.gif

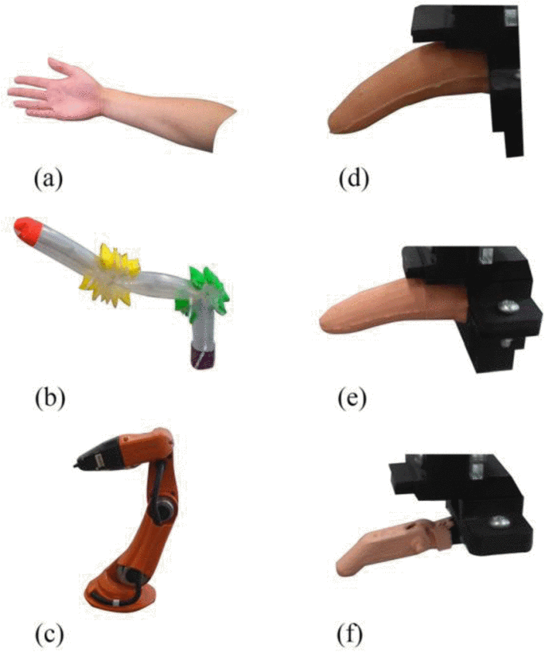
poster/soft_vs_rigid_robot_test_example.gif
