cdelor02/mres-thesis/poster/soft_vs_rigid_robot_test_example_landscape.gif

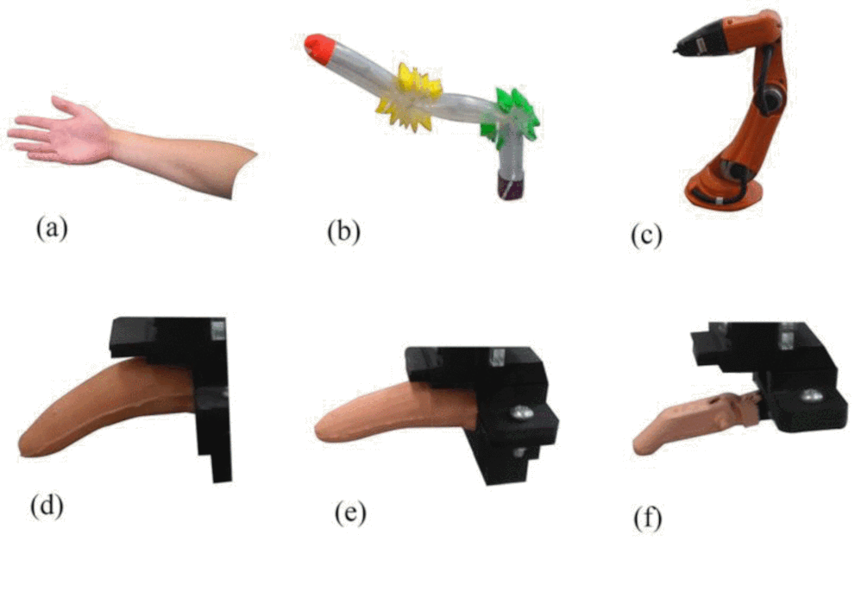
poster/soft_vs_rigid_robot_test_example_landscape.gif
