cdelor02/mres-thesis/journal_club_presentation/soft_robot_actuator_figures/F4.large.jpg

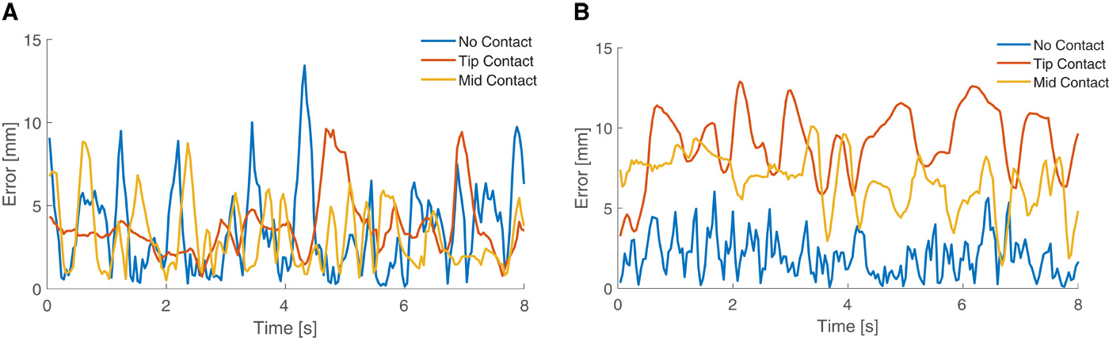
journal_club_presentation/soft_robot_actuator_figures/F4.large.jpg
