cdelor02/mres-thesis/journal_club_presentation/soft_robot_actuator_figures/Fig_S2_cPDMS_vs_flex_sensor.png

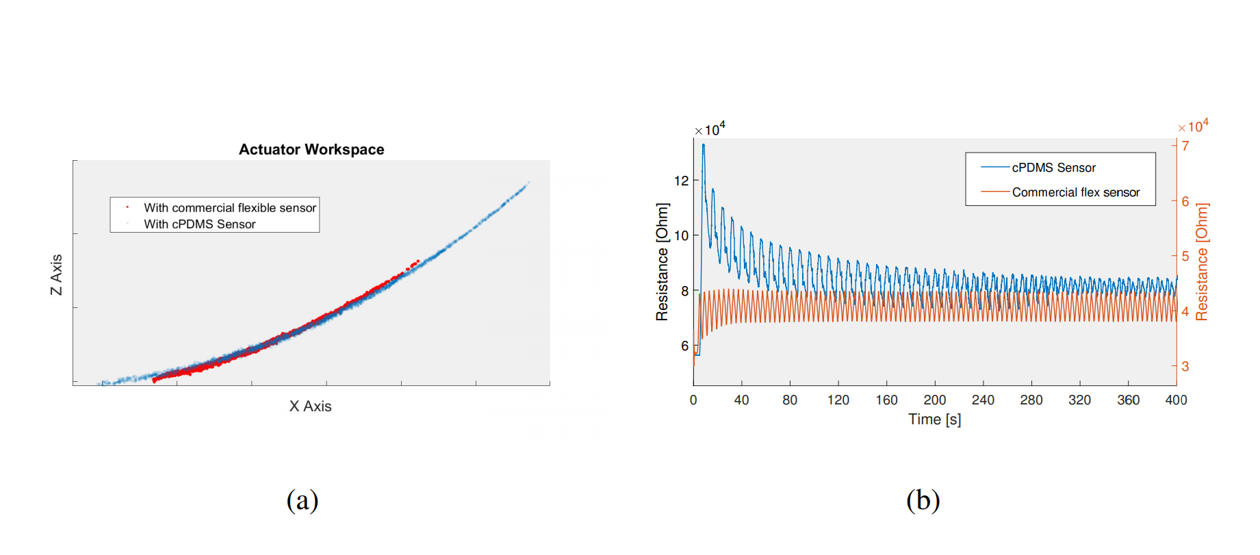
journal_club_presentation/soft_robot_actuator_figures/Fig_S2_cPDMS_vs_flex_sensor.png
