cdelor02/mres-thesis/journal_club_presentation/soft_robot_actuator_figures/Fig_S7_sensor_actuator_topology.png

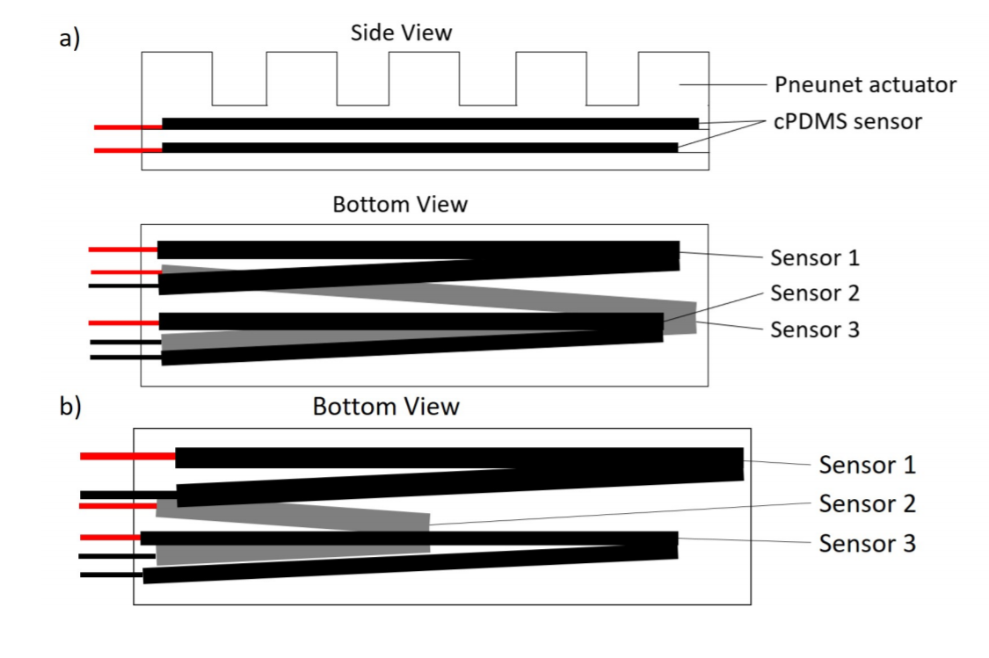
journal_club_presentation/soft_robot_actuator_figures/Fig_S7_sensor_actuator_topology.png
