cdelor02/mres-thesis/EIT_test_code/ardInterface.py

"""
Set of functions to facilitate connection to syringe pumps, which are controlled by arduinos.
Arduinos connected to a USB hub so COM port names must be checked in main code.
Enables connection, pressure monitoring, and step count monitoring for later burst
protection and volume calculation.
"""
import serial 
import time
import numpy as np

class ardInterface:

    def __init__(self, ardName, numPort):
        self.ardName = ardName
        self.portNumber = numPort
        self.ser = serial.Serial()
        self.ser.port = 'COM%s' % (self.portNumber) 
        self.ser.baudrate = 9600
        self.ser.timeout = 0

        self.curr_stp = 0

        self.press1 = 0.0
        self.press2 = 0.0
        self.press3 = 0.0
        self.press4 = 0.0
        self.press5 = 0.0
        self.press6 = 0.0
        self.press7 = 0.0
        self.press8 = 0.0
        self.press9 = 0.0
        self.press10 = 0.0
        #self.pressArray = np.array([self.press1, self.press2, 
        #                            self.press3, self.press4, 
        #                            self.press5, self.press6, 
        #                            self.press7, self.press8, 
        #                            self.press9, self.press10])
        #self.pressMed = np.median(self.pressArray)
        #self.pressMedPrev = self.pressMed

        self.derivThresh = 20
        self.deriv2Thresh = 30

        self.conDetected = False
    

    def connect(self):
        """
        Modified to 
        Each pump requires verification of the cable it is contolling (top, lhs, or rhs).
        Pumps will function normally when the pumpName sent here matches the name hardcoded 
        on each arduino.
        e.g. top = connect("TOP", 4)
        """
        self.ser.open()
        message = self.ardName + "\n"
        reply = ""
        message = message.encode('utf-8')    #Encode message
        print("Message - ", message)
        time.sleep(1)     #give arduino time to set up (there are delays in arduino code for pressure sensor)
        while(1):
            time.sleep(0.5)     #delay before sending message again
            self.ser.write(message)
            print("Handshake: ", message)
            if self.ser.in_waiting > 0:
                reply = self.ser.readline().strip()
                self.ser.reset_input_buffer()
                reply = reply.decode('ascii')#, errors='replace')

                if reply == self.ardName:
                    self.ser.reset_output_buffer()
                    break

        # return open serial connection to allow pumps to be controlled in main code
        return reply



    def sendStep(self, stepNumber):
        """
        This function sends ideal position (stepNumber) then receives
        the real step count (stepCount) from arduino.
        steps = sendStep(serialConnection, stepNumber)
        """
        if type(stepNumber) != str:
            stepString = "{:04d}".format(stepNumber)
        else:
            stepString = stepNumber
        message = "S" + stepString + "\n"
        # print("Message: ", repr(message))
        message = message.encode('utf-8')
        self.ser.write(message)
        return



    def listenReply(self):
        x = "e"
        stepPress = b""
        noBytes = self.ser.in_waiting
        # Wait here for reply - source of delay
        while noBytes == 0:
            noBytes = self.ser.in_waiting
        # Read all bytes in input buffer
        # stepPress = ser.read(noBytes)
        # Check for end character
        while ord(x) != ord("E"):
            x = self.ser.read()
            if x == b"":
                break
            elif x == b"E":
                break
            stepPress = stepPress + x

        stepPress = stepPress.decode('utf-8')
        stepPress = stepPress.split(',')
        # print(stepPress)
        self.ser.reset_input_buffer()
        self.ser.reset_output_buffer()

        # IF STEP COUNT = L_'pumpName' STOP AND DISCONNECT ALL

        if stepPress == ['']:
            stepCount = "S_Empty" # Change this later to handle dropped values
            pumpPress = "P_Empty"
            pumpTime = "T_Empty"
        else:
            stepCount = stepPress[0]
            if "L " in stepCount: # If "L " in stepPress then limit hit/pressure error
                print("In from arduino: ", stepPress)
                raise TypeError('Pressure limit or switch hit in main loop')
            pumpPress = float(stepPress[1])/10
            # if pumpPress < 0:
            #     print("Negative pressure: ", stepPress)
            #     raise TypeError('Error reading pressure in main loop')
            pumpTime = int(stepPress[2])
        return stepCount, pumpPress, pumpTime


"""
    def listenZero(self, isPumpZero, pressIn, timeIn):
        # If calibration done, don't wait for arduino
        if (isPumpZero == True):
            stepCount = 0
            pumpPress = pressIn
            pumpTime = timeIn
            return stepCount, pumpPress, pumpTime
        else:
            x = "e"
            stepPress = b""
            while self.ser.in_waiting == 0:
                pass
            # Check for end character
            while ord(x) != ord("E"):
                x = self.ser.read()
                if x == b"":
                    break
                elif x == b"E":
                    break
                stepPress = stepPress + x

            stepPress = stepPress.decode('utf-8')
            stepPress = stepPress.split(',')
            self.ser.reset_input_buffer()
            self.ser.reset_output_buffer()

            if stepPress == b"":
                stepCount = "S_Empty" # Change this later to handle dropped values
                pumpPress = "P_Empty"
                pumpTime = "T_Empty"
            else:
                # print(stepPress)
                stepCount = stepPress[0]
                if "L " in stepCount: # If "L " in stepPress then limit hit/pressure error
                    print("In from arduino: ", stepPress)
                    raise TypeError('Pressure limit or switch hit during calibration')
                pumpPress = float(stepPress[1])/10
                # if pumpPress < 0:
                #     print("Negative pressure: ", stepPress)
                #     raise TypeError('Error reading pressure during calibration')
                pumpTime = int(stepPress[2])

            # if (isPumpZero == True):
            #     stepCount = 0
            #     pumpPress = pressIn
            #     pumpTime = timeIn
            return stepCount, pumpPress, pumpTime

    def newPressMed(self, newPress):
        self.press10 = self.press9
        self.press9 = self.press8
        self.press8 = self.press7
        self.press7 = self.press6
        self.press6 = self.press5
        self.press5 = self.press4
        self.press4 = self.press3
        self.press3 = self.press2
        self.press2 = self.press1
        self.press1 = newPress
        self.pressArray = np.array([self.press1, self.press2, self.press3, self.press4, self.press5,\
            self.press6, self.press7, self.press8, self.press9, self.press10])
        self.pressMedPrev = self.pressMed
        self.pressMed = np.median(self.pressArray)

        return self.pressMed

    def derivPress(self, newTime, prevTime):
        realTimeStep = (newTime - prevTime)/1000
        # Prevent div by zero errors / limit noise?
        if realTimeStep <= 0.001:
            realTimeStep = 0.001
        pressDiff = self.pressMed - self.pressMedPrev
        deriv = pressDiff/realTimeStep
        deriv2 = deriv/realTimeStep
        # Check derivatives against heuristically determined threshold values to determine contact:
        self.conDetected = (abs(deriv) > self.derivThresh) & (abs(deriv2) > self.deriv2Thresh)
        # 1 means actuator in tension, -1 means compression, 0 means no contact
        self.conDetected = self.conDetected*np.sign(deriv)
        return self.conDetected, deriv

    def initPress(self, pressIndex, pressVal):
        self.pressArray[pressIndex] = float(pressVal)
"""
