cdelor02/mres-thesis/EIT_test_code/eit_data_parsing.py

# data parsing and cleaning

import pandas as pd
import sys

filename = sys.argv[1]
col = sys.argv[2]

df = pd.read_csv(filename, sep='\t', 
	lineterminator='\n', skiprows=1, names=["A", "B", "C", "D", "E", "F", "G", "H"])

new_df = df[[col]]

new_df.to_csv(filename[:-4]+'_parsed'+'.txt', sep='\t', line_terminator='\n', float_format='%.6f')
